UncleRus/quorum-reborn/resources/DiskDrive/disk5buf.png

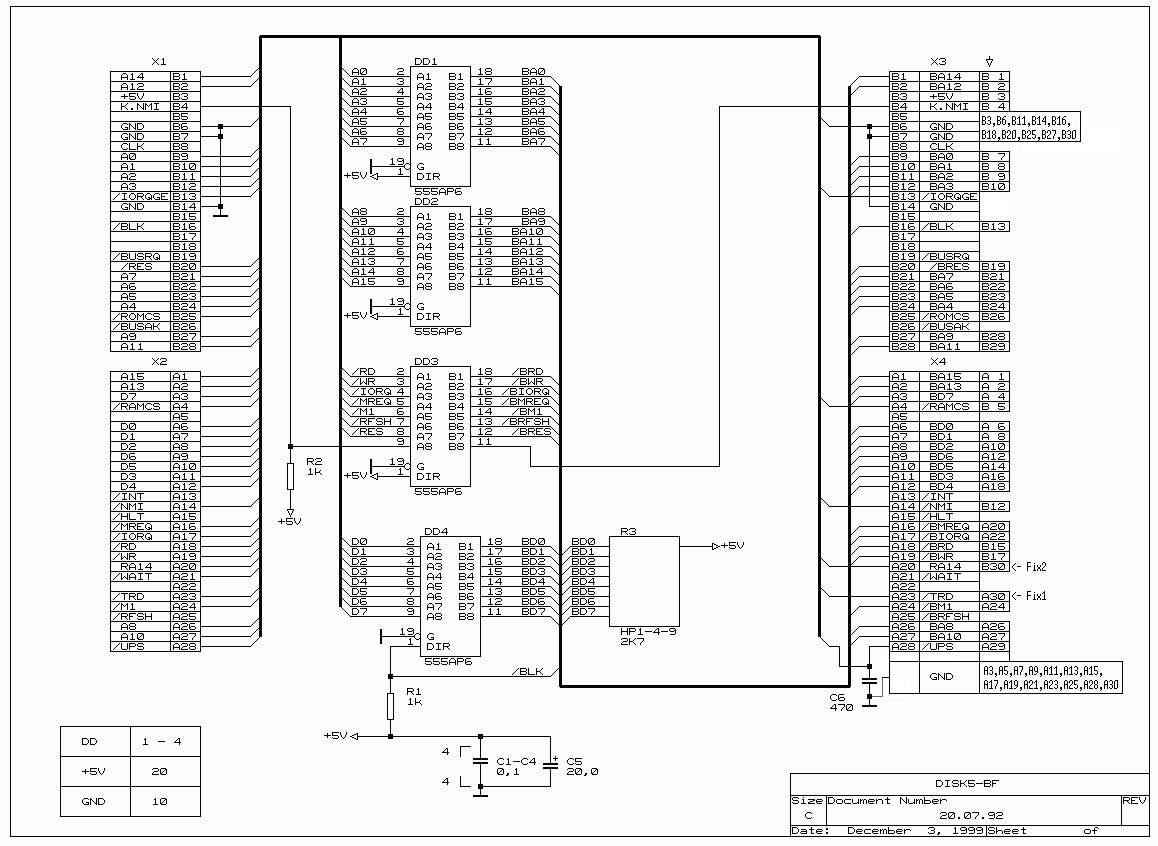
resources/DiskDrive/disk5buf.png
