UncleRus/quorum-reborn/resources/DiskDrive/disk5emu.png

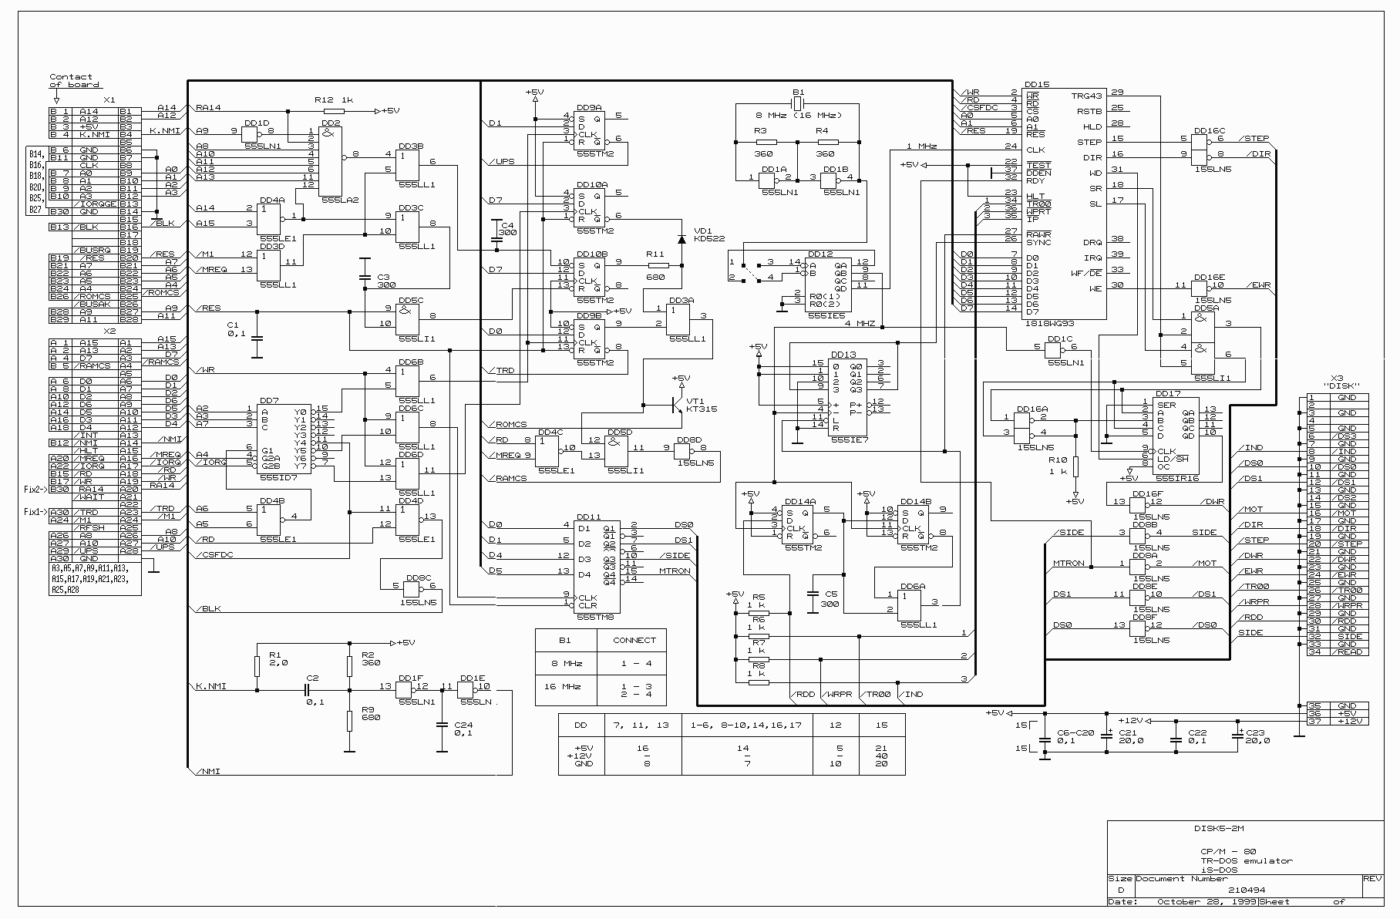
resources/DiskDrive/disk5emu.png
