UncleRus/quorum-reborn/resources/DiskDrive/DISK5RAM.PNG

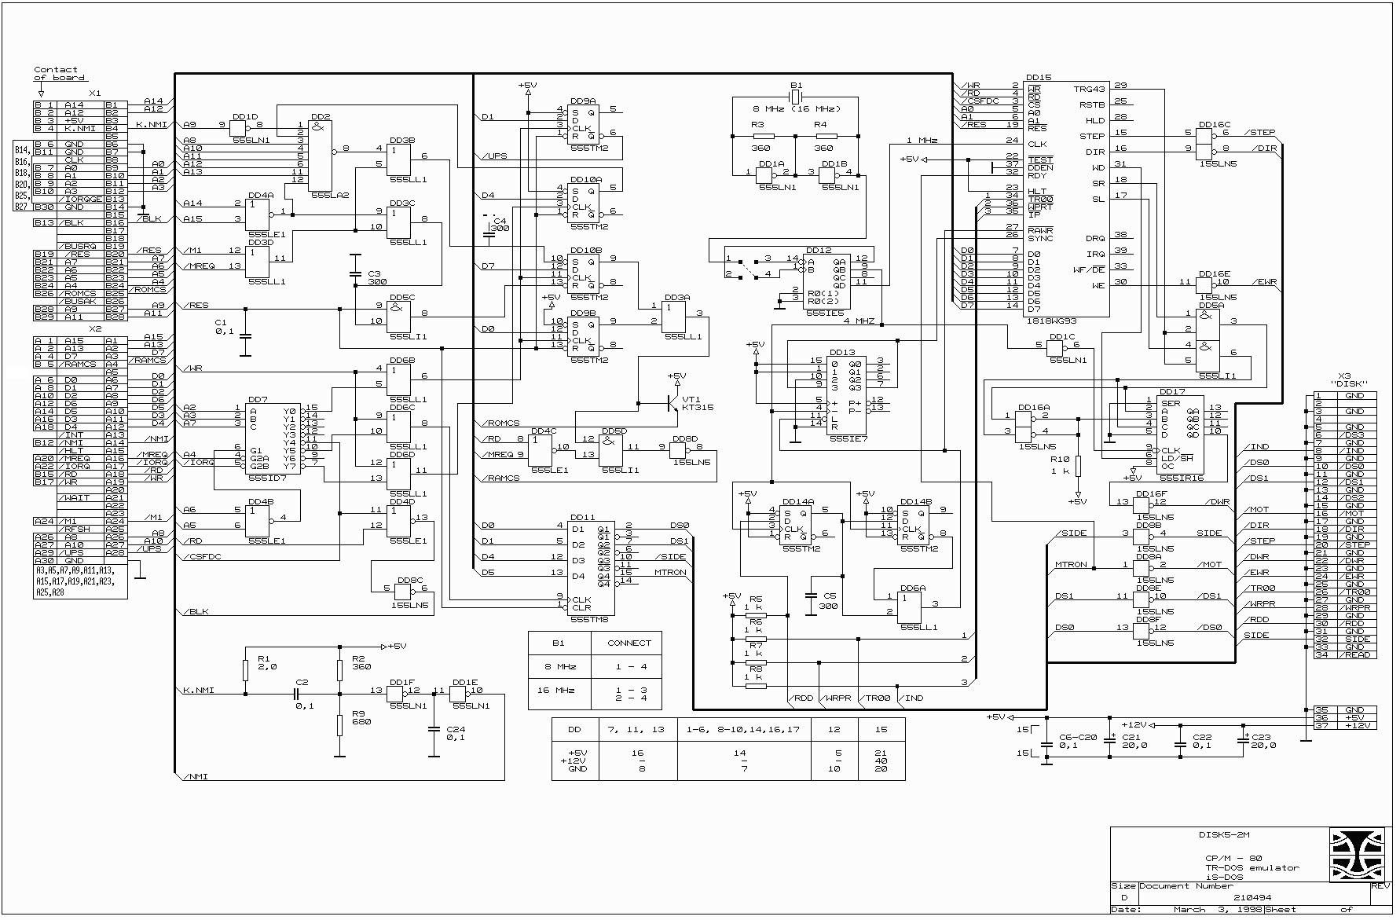
resources/DiskDrive/DISK5RAM.PNG
