UncleRus/quorum-reborn/resources/DiskDrive/disk5raz.png

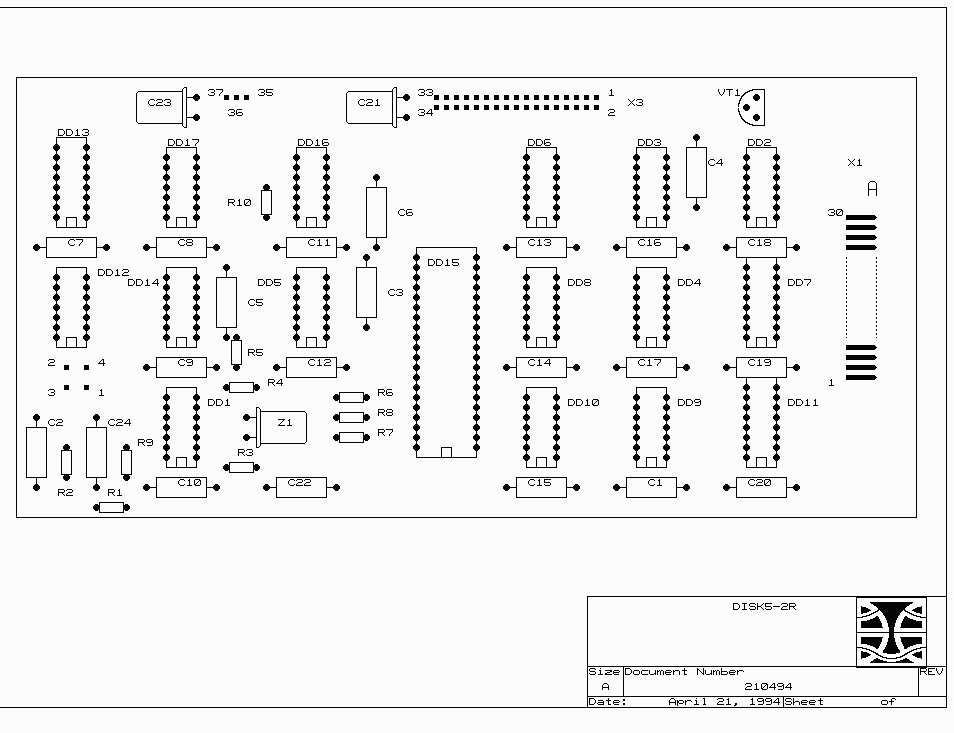
resources/DiskDrive/disk5raz.png
