UncleRus/quorum-reborn/resources/DiskDrive/disk5trd.png

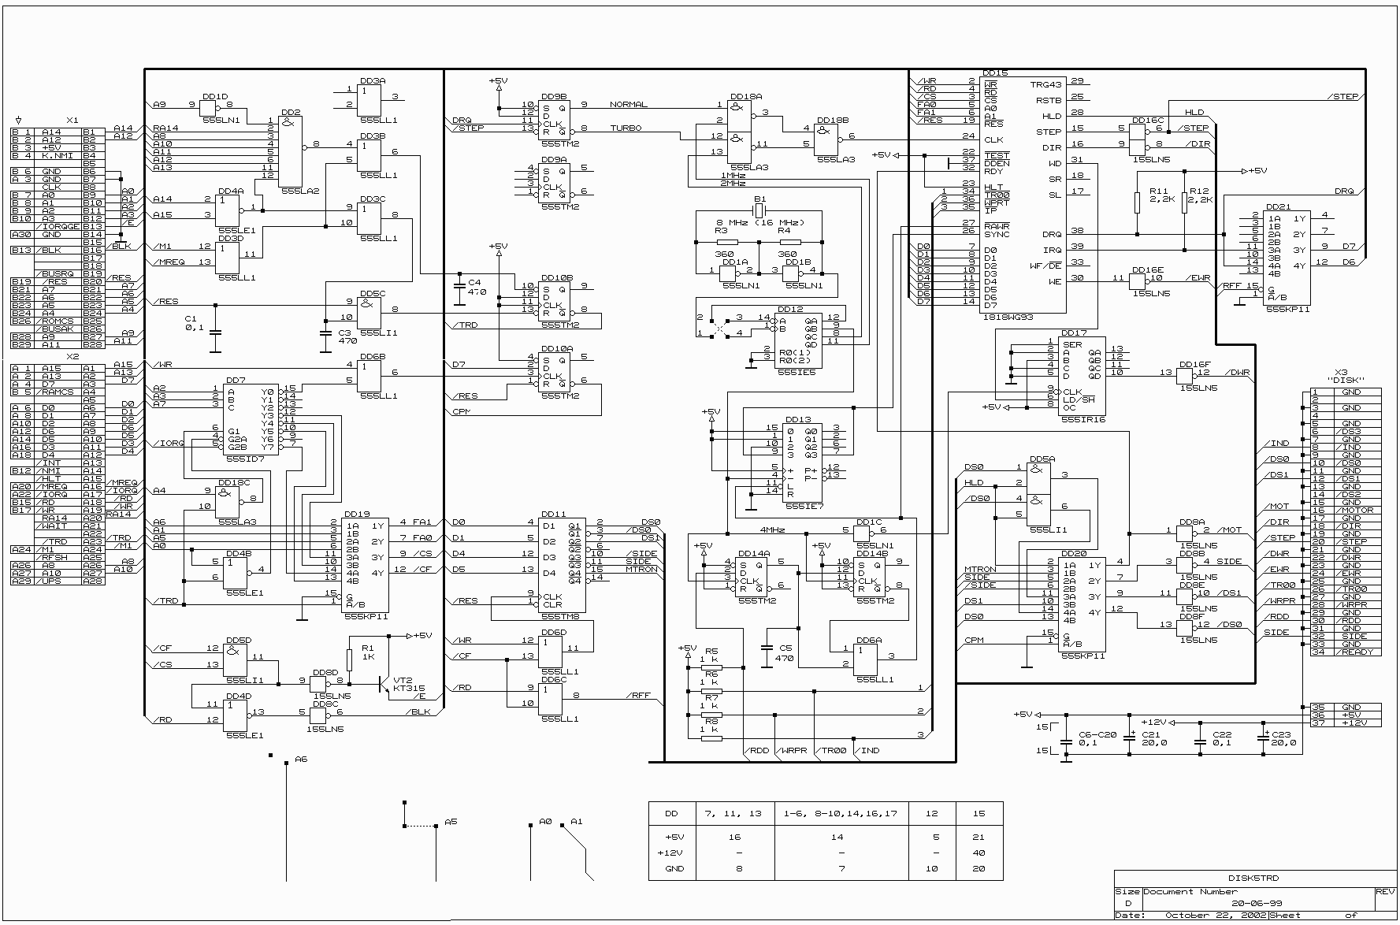
resources/DiskDrive/disk5trd.png
