UncleRus/quorum-reborn/resources/Magic-05/Schematics/Axon/p1.jpg

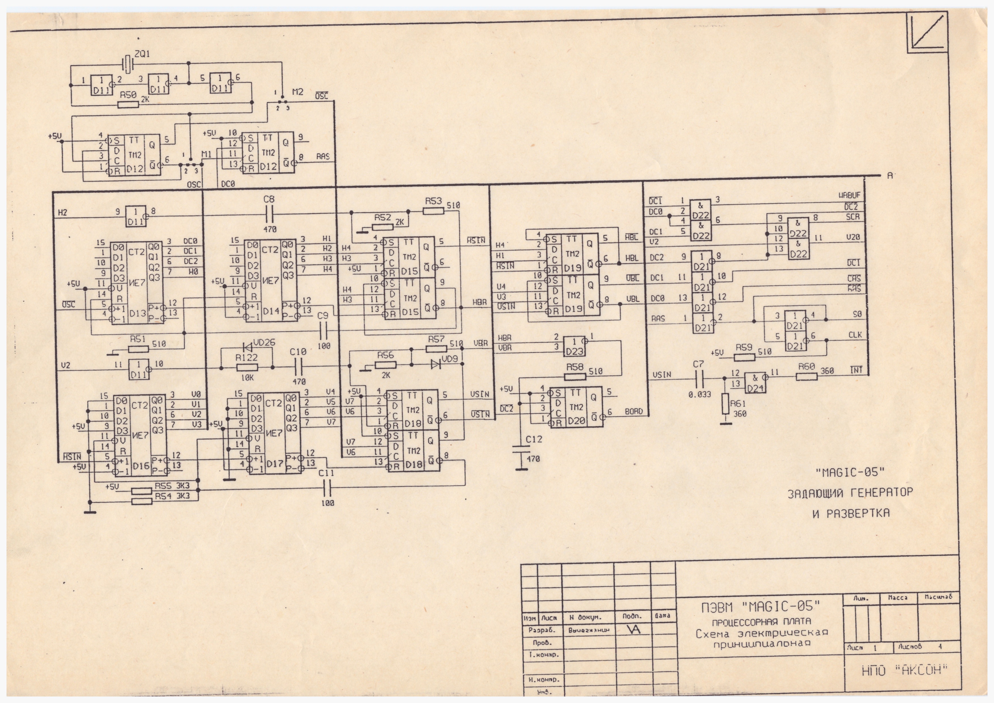
resources/Magic-05/Schematics/Axon/p1.jpg
