UncleRus/quorum-reborn/resources/Magic-05/Schematics/Axon/p2.jpg

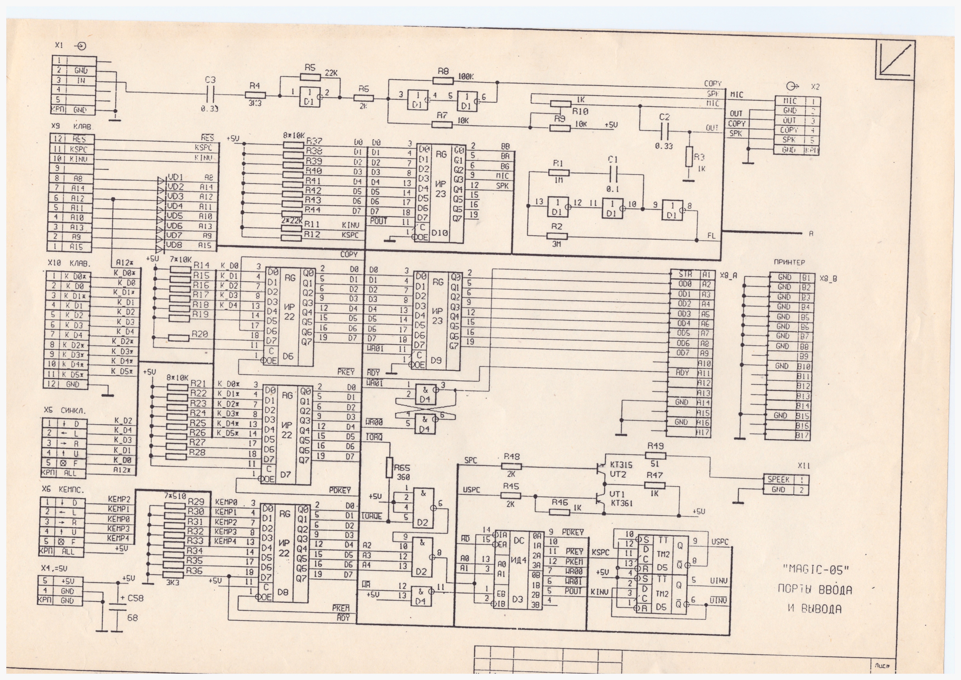
resources/Magic-05/Schematics/Axon/p2.jpg
