UncleRus/quorum-reborn/resources/Magic-05/Schematics/Axon/p5.jpg

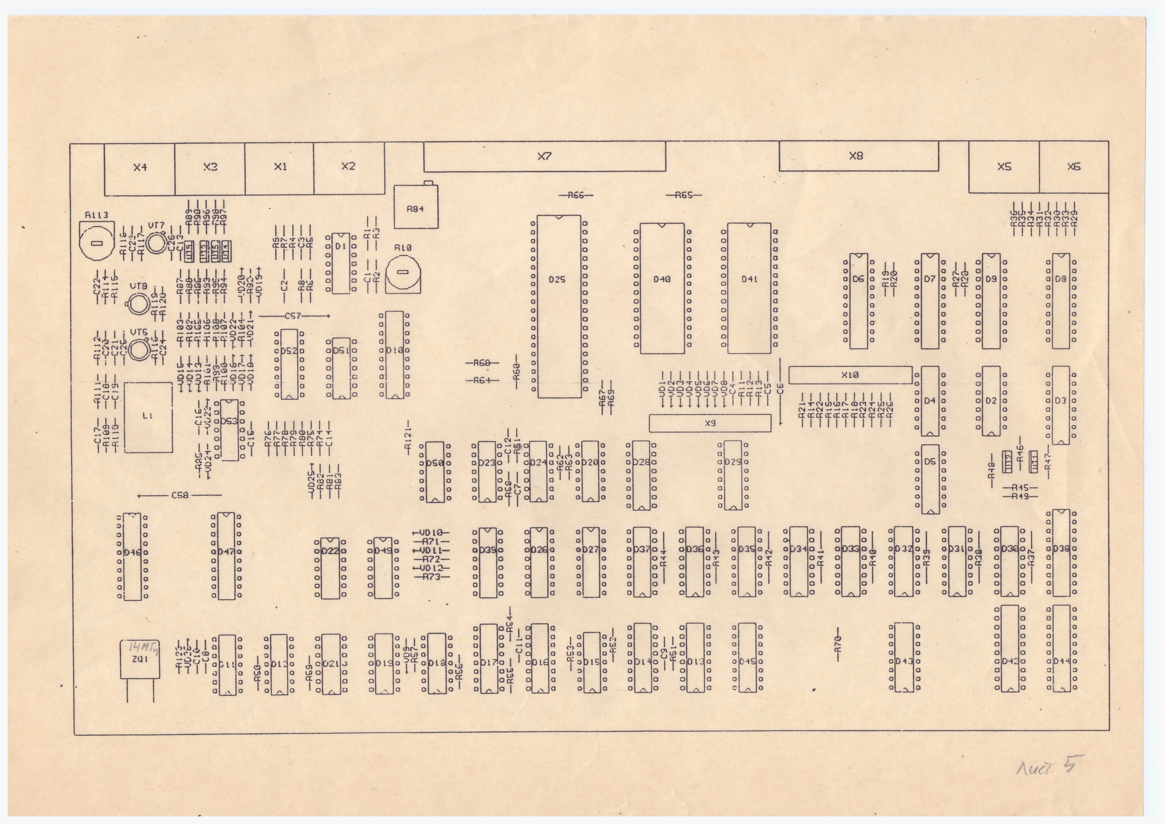
resources/Magic-05/Schematics/Axon/p5.jpg
