UncleRus/quorum-reborn/resources/Magic-06/Schematics/magic6_1.png

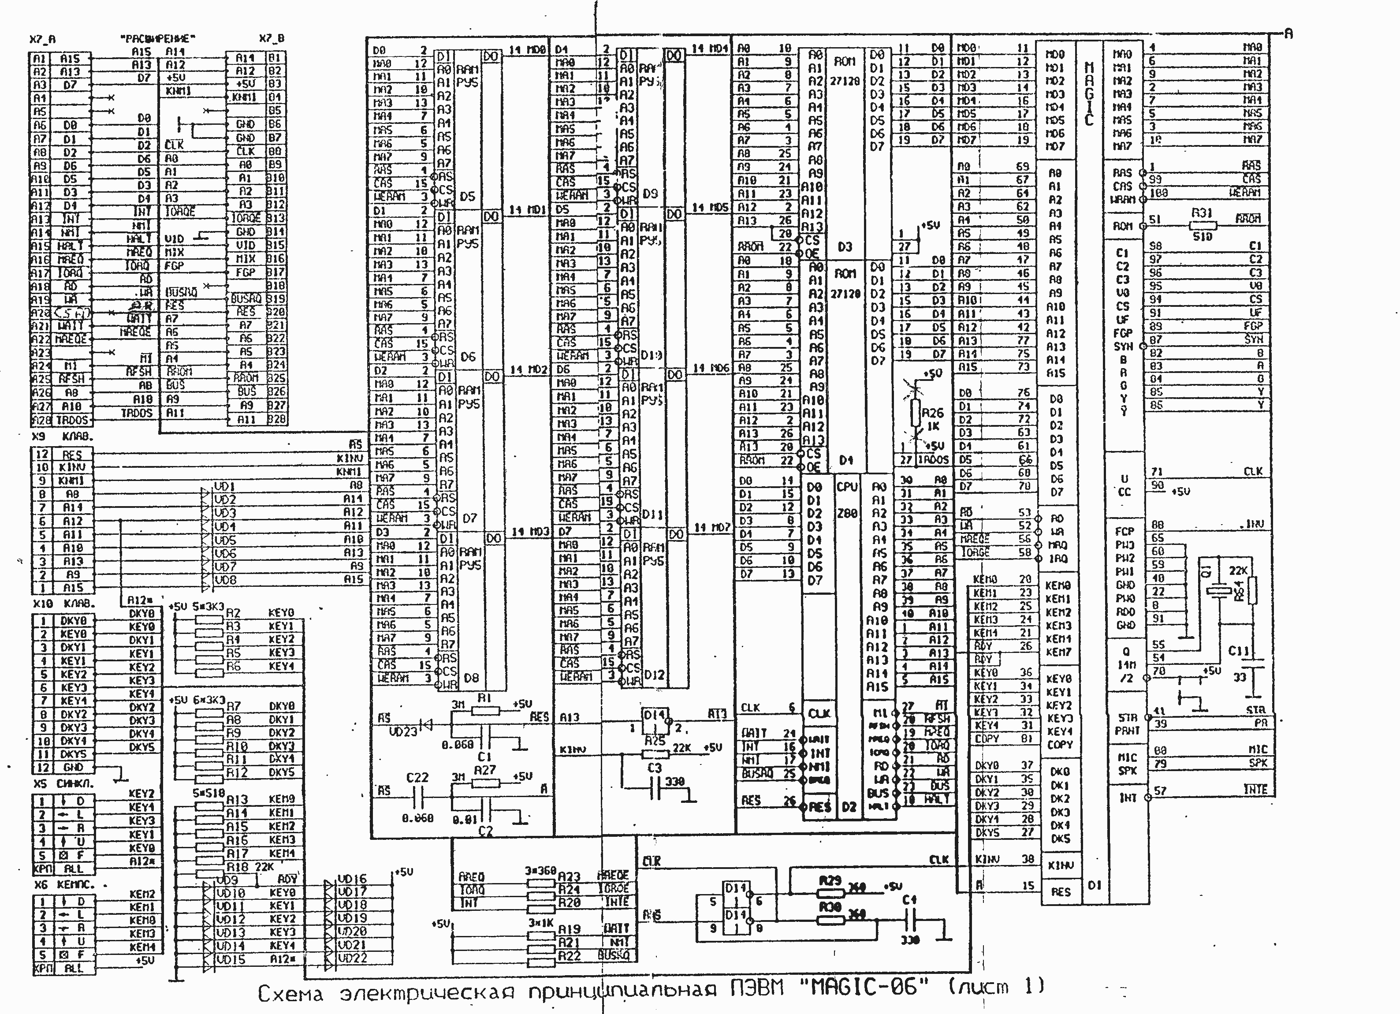
resources/Magic-06/Schematics/magic6_1.png
