UncleRus/quorum-reborn/resources/Magic-06/Schematics/magic6_2.png

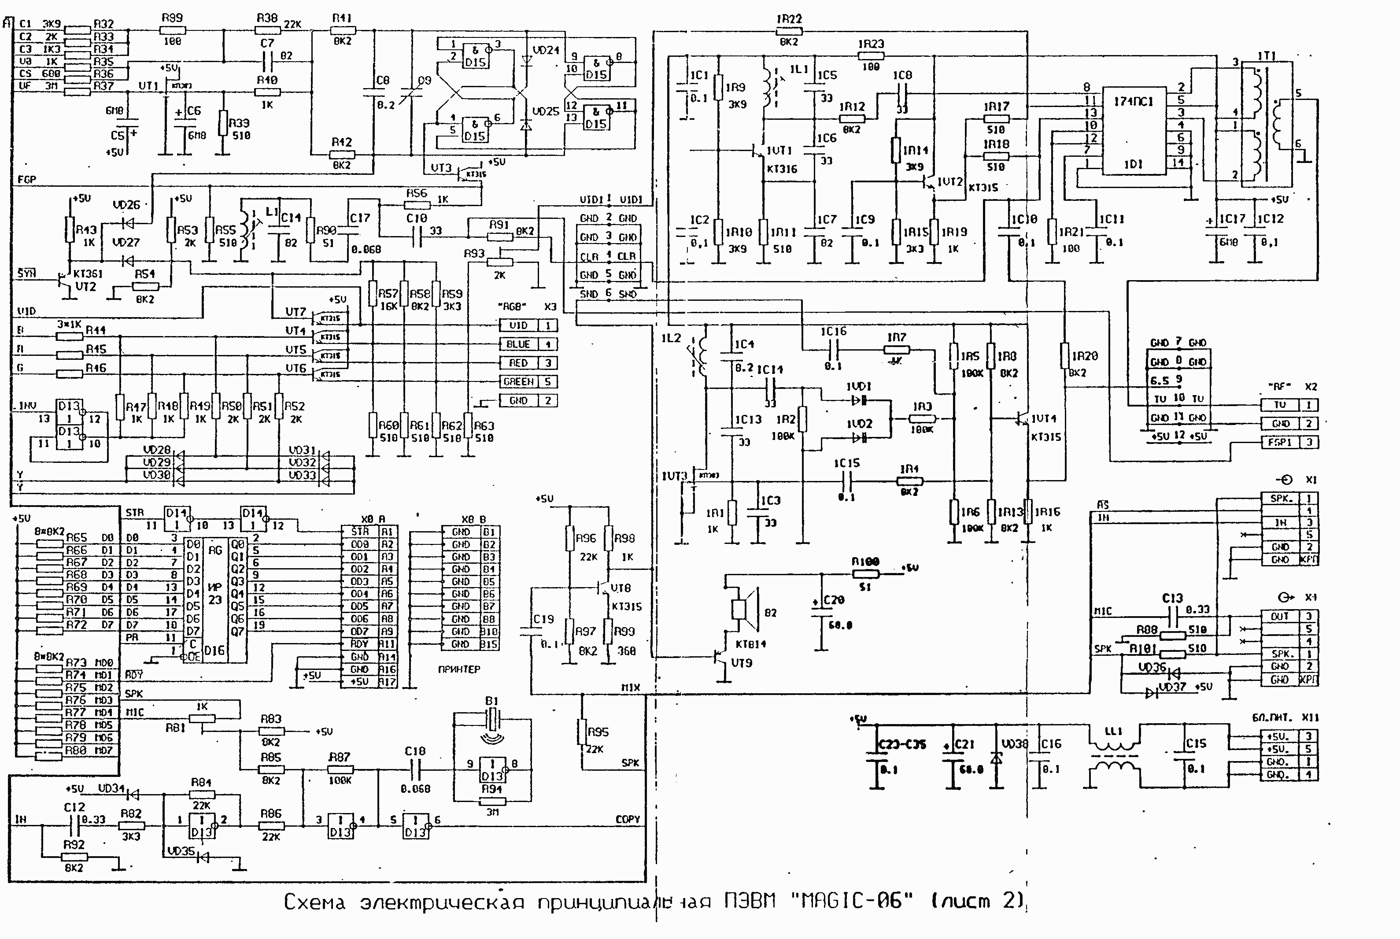
resources/Magic-06/Schematics/magic6_2.png
