UncleRus/quorum-reborn/resources/Quorum-64/Schematics/KBD_sch.jpg

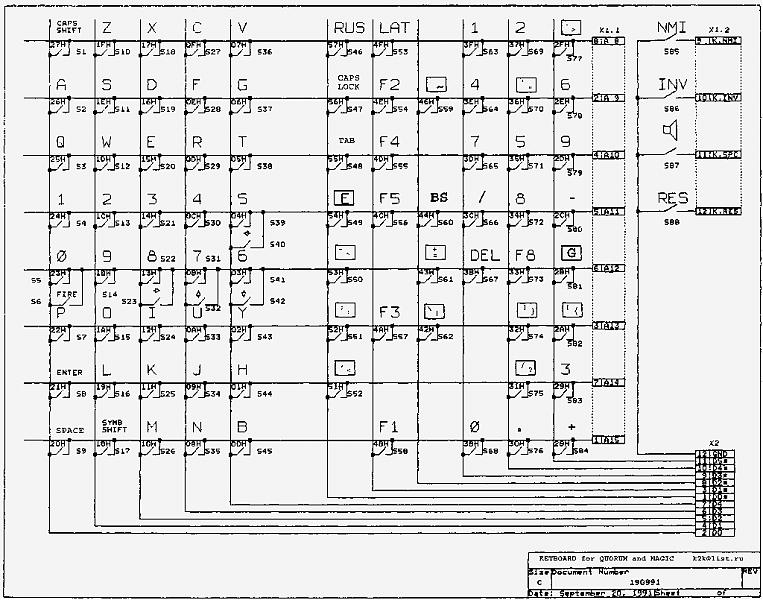
resources/Quorum-64/Schematics/KBD_sch.jpg
