UncleRus/quorum-reborn/resources/Quorum-64/Schematics/QU64_1.PNG

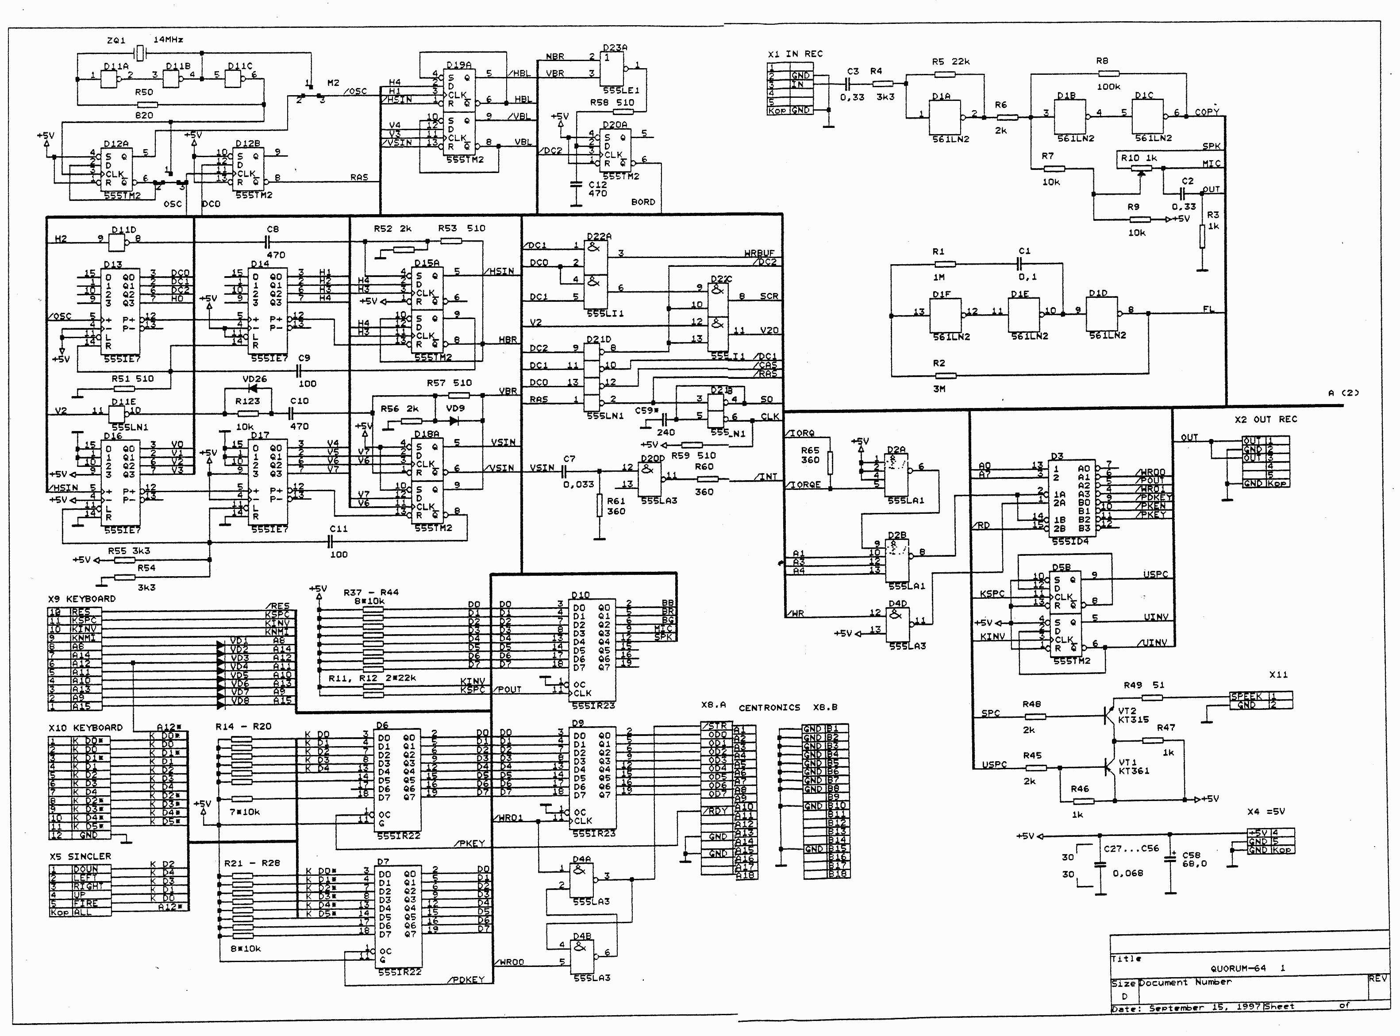
resources/Quorum-64/Schematics/QU64_1.PNG
