UncleRus/quorum-reborn/resources/Quorum-64/Schematics/QU64_2.PNG

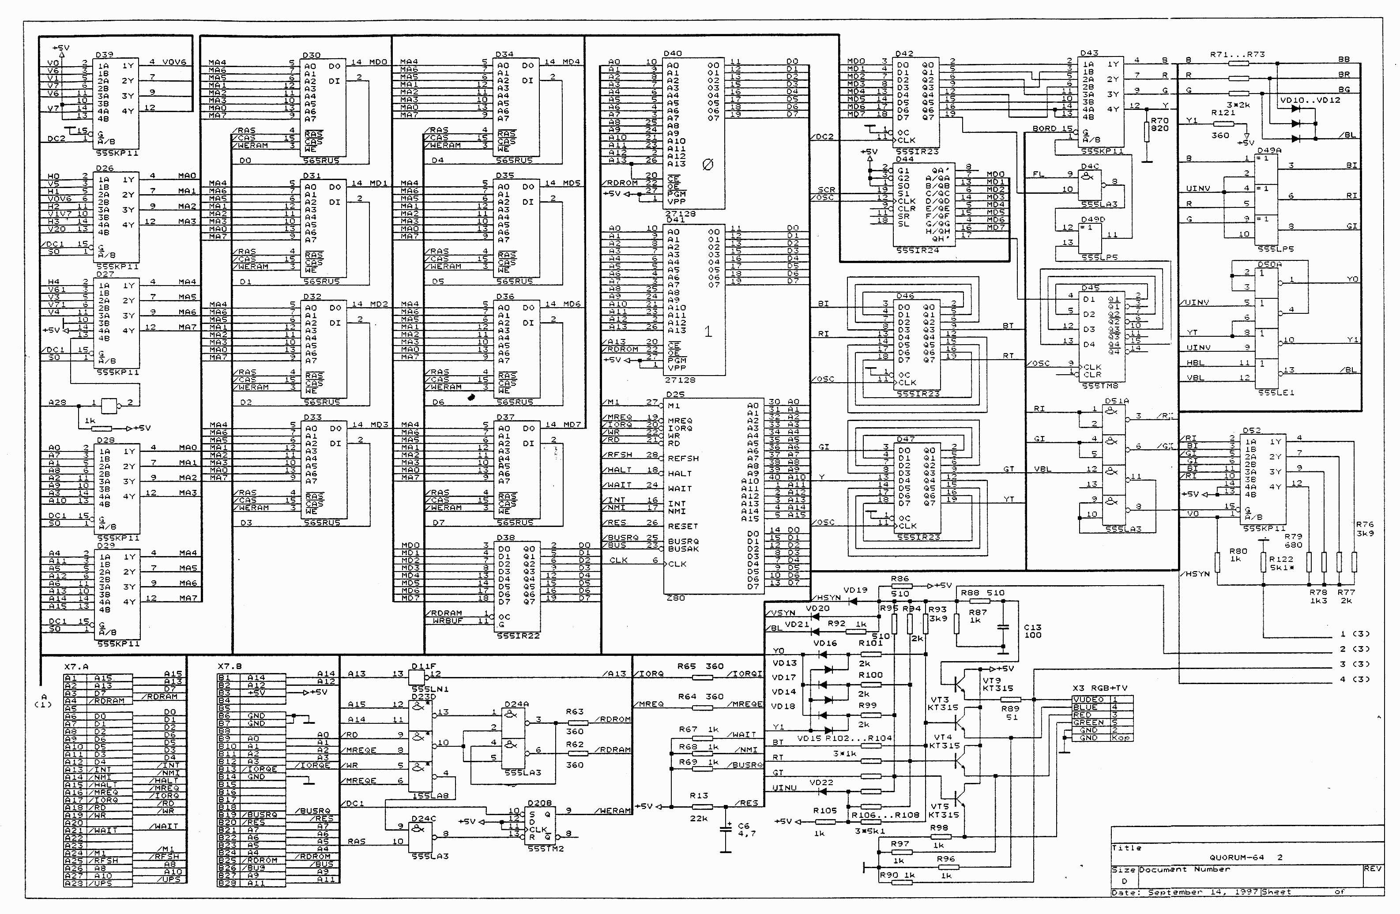
resources/Quorum-64/Schematics/QU64_2.PNG
