UncleRus/quorum-reborn/resources/Quorum-64/Schematics/Quorum_64_0893076.jpg

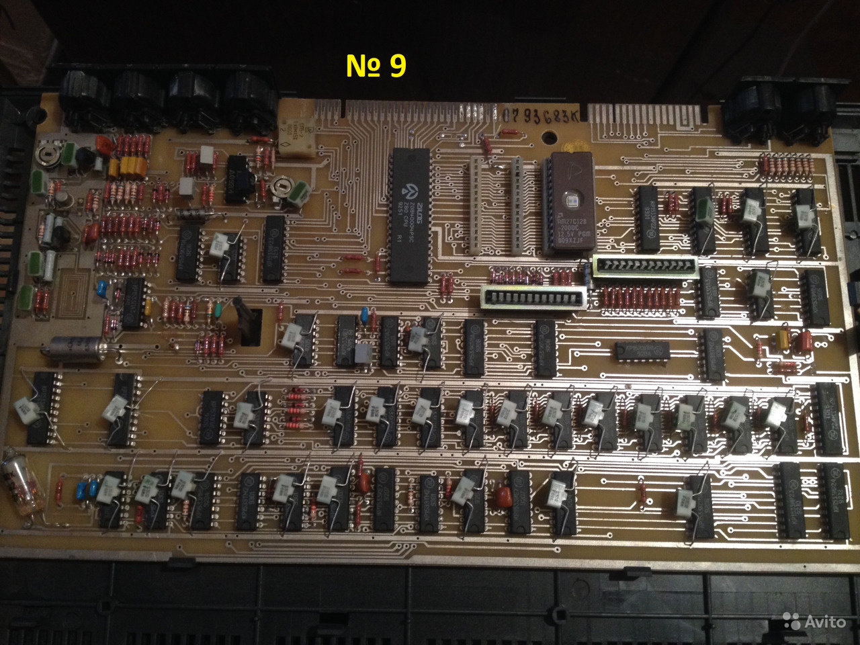
resources/Quorum-64/Schematics/Quorum_64_0893076.jpg
