UncleRus/quorum-reborn/resources/Quorum-128+/Photo/235_001.jpg

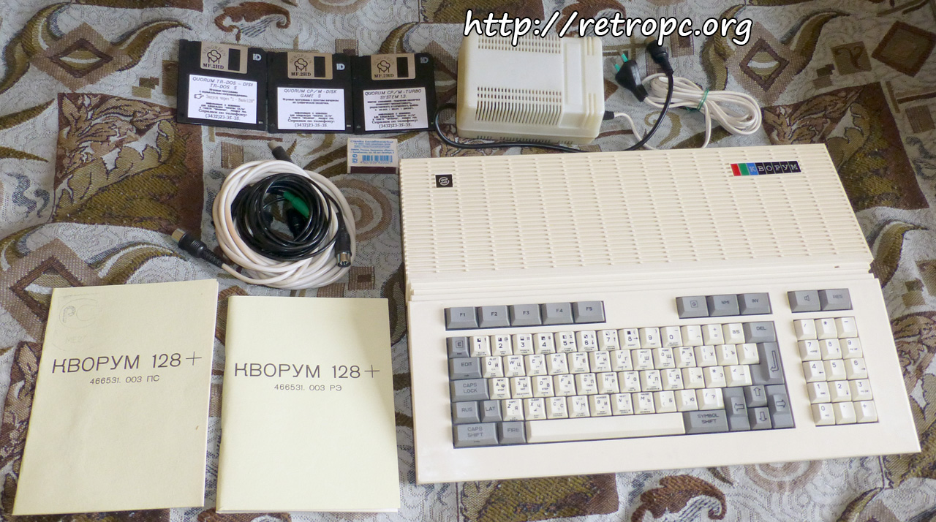
resources/Quorum-128+/Photo/235_001.jpg
