UncleRus/quorum-reborn/resources/Quorum-128+/Photo/235_002.jpg

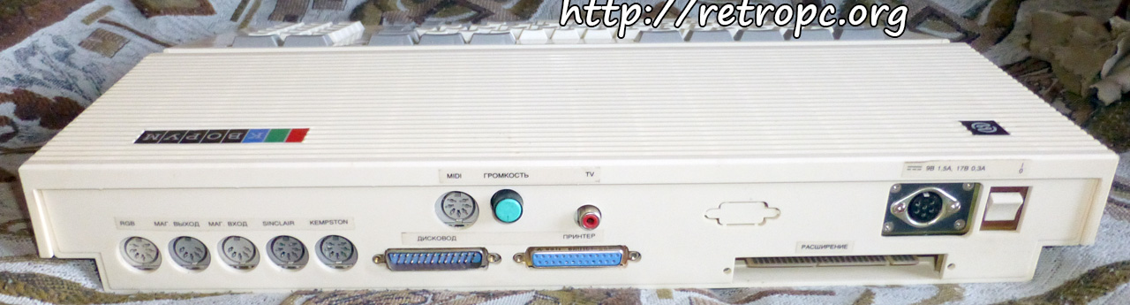
resources/Quorum-128+/Photo/235_002.jpg
