UncleRus/quorum-reborn/resources/Quorum-128+/Photo/235_007.jpg

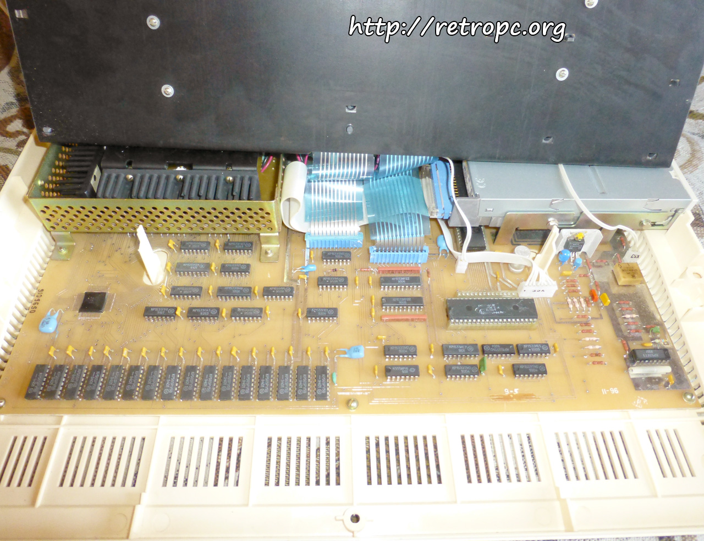
resources/Quorum-128+/Photo/235_007.jpg
