UncleRus/quorum-reborn/resources/Quorum-128+/Schematics/SECAMCODER.png

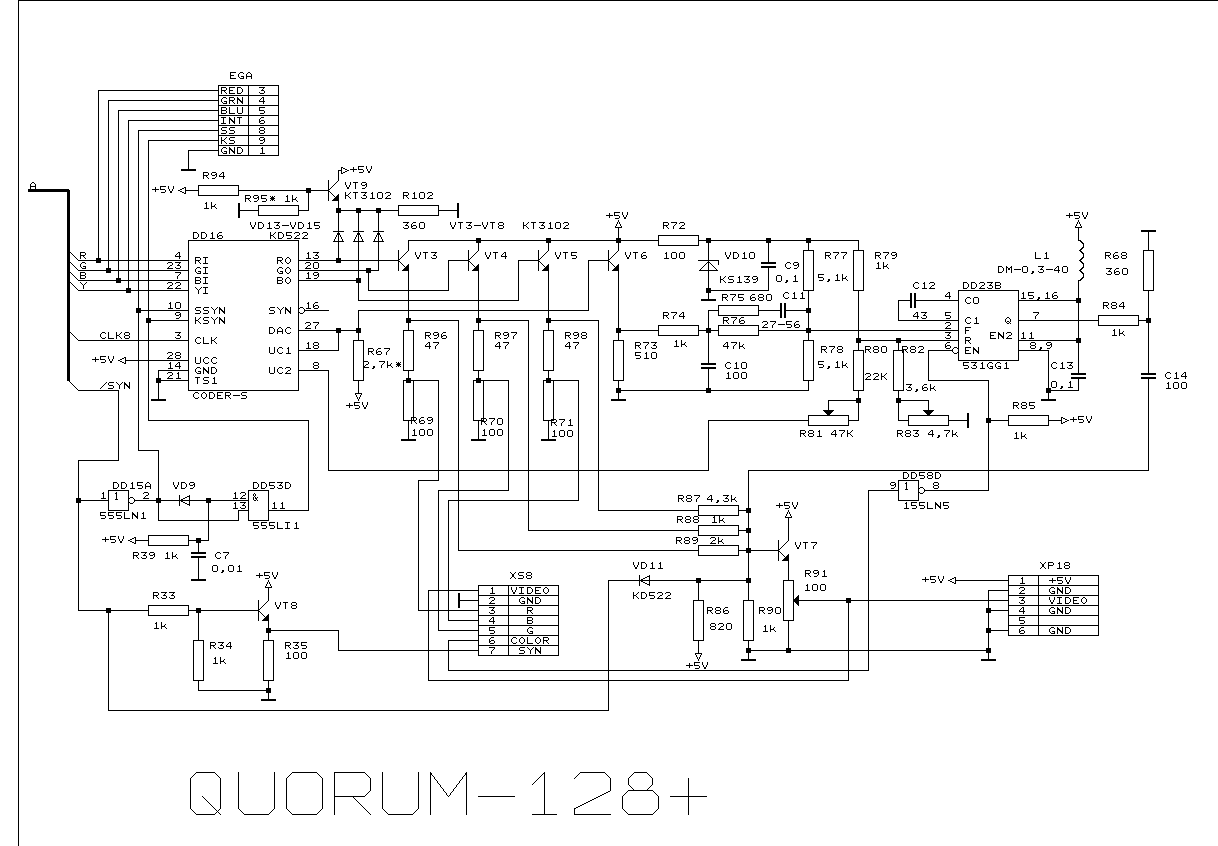
resources/Quorum-128+/Schematics/SECAMCODER.png
