UncleRus/quorum-reborn/resources/Quorum-128+/Schematics/ULA.png

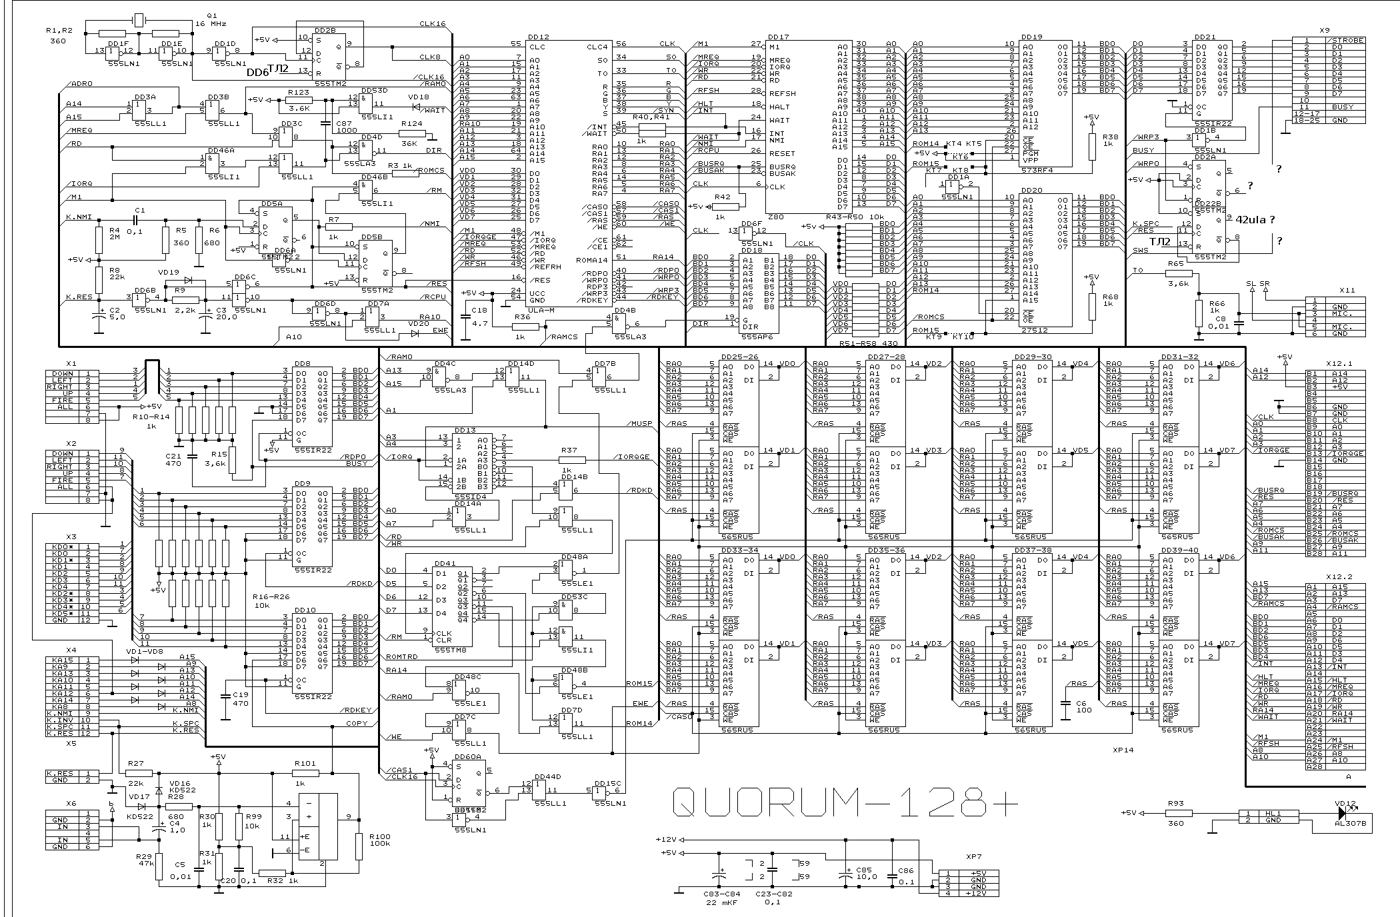
resources/Quorum-128+/Schematics/ULA.png
