UncleRus/quorum-reborn/resources/Quorum-128/Schematics/Q128_CS.PNG

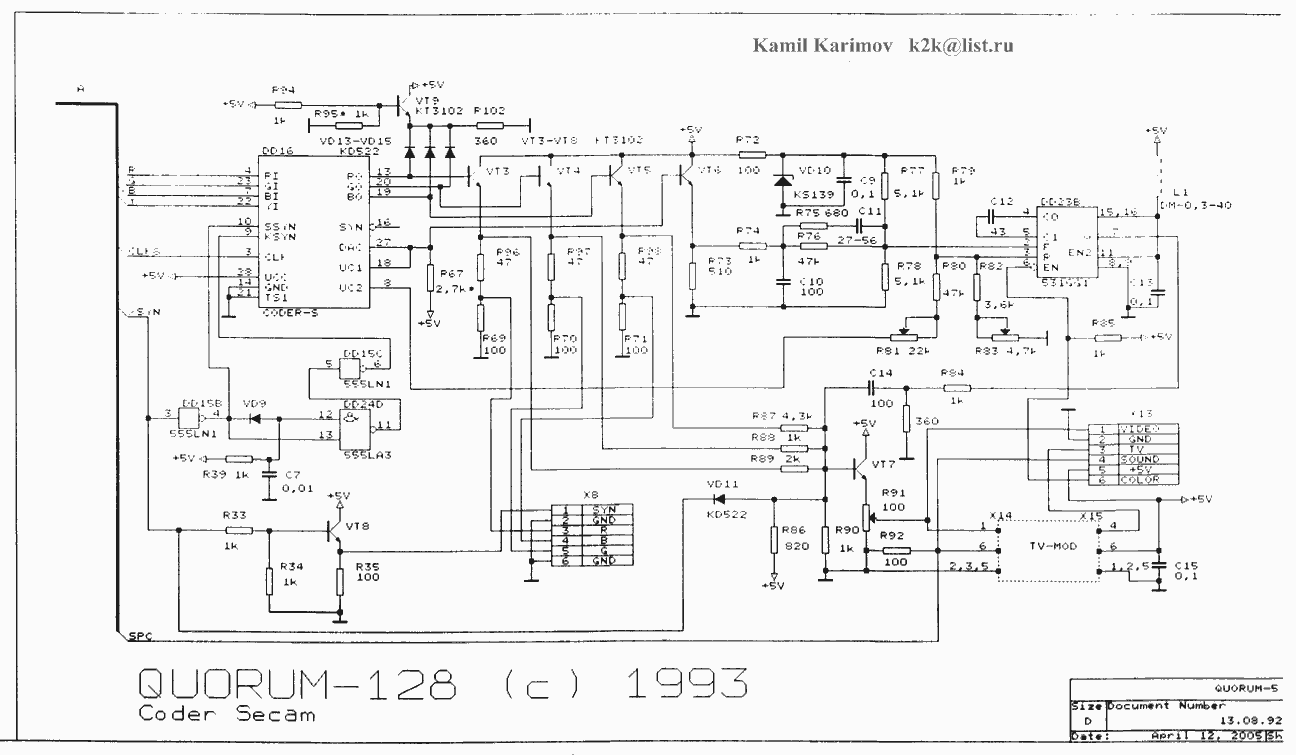
resources/Quorum-128/Schematics/Q128_CS.PNG
