UncleRus/quorum-reborn/resources/Quorum-128/Schematics/Q128P2M.PNG

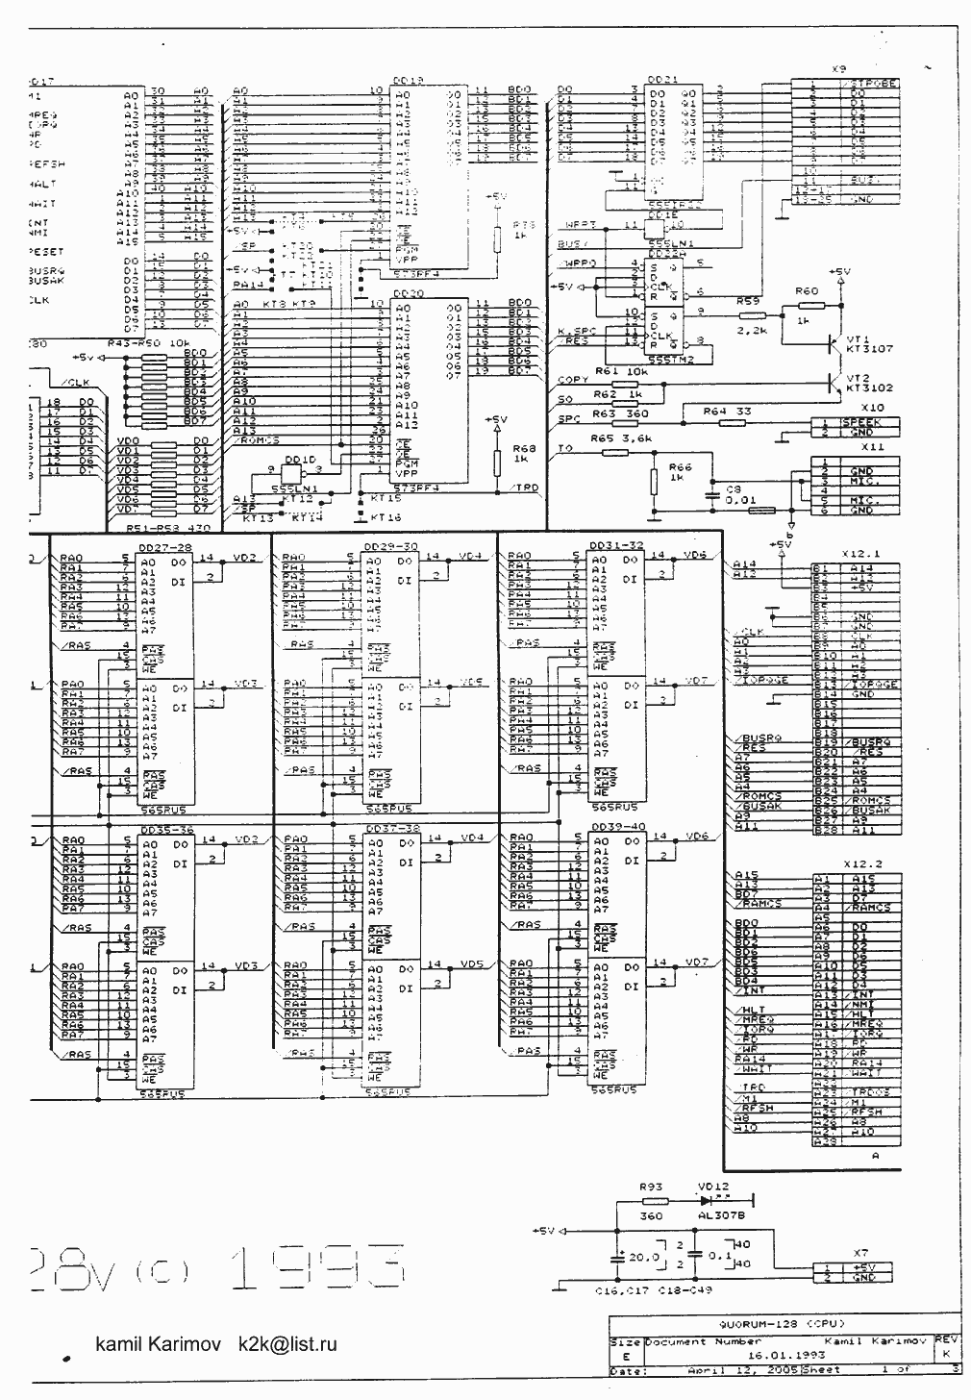
resources/Quorum-128/Schematics/Q128P2M.PNG
