UncleRus/quorum-reborn/resources/Quorum-128/Schematics/qu128mp.png

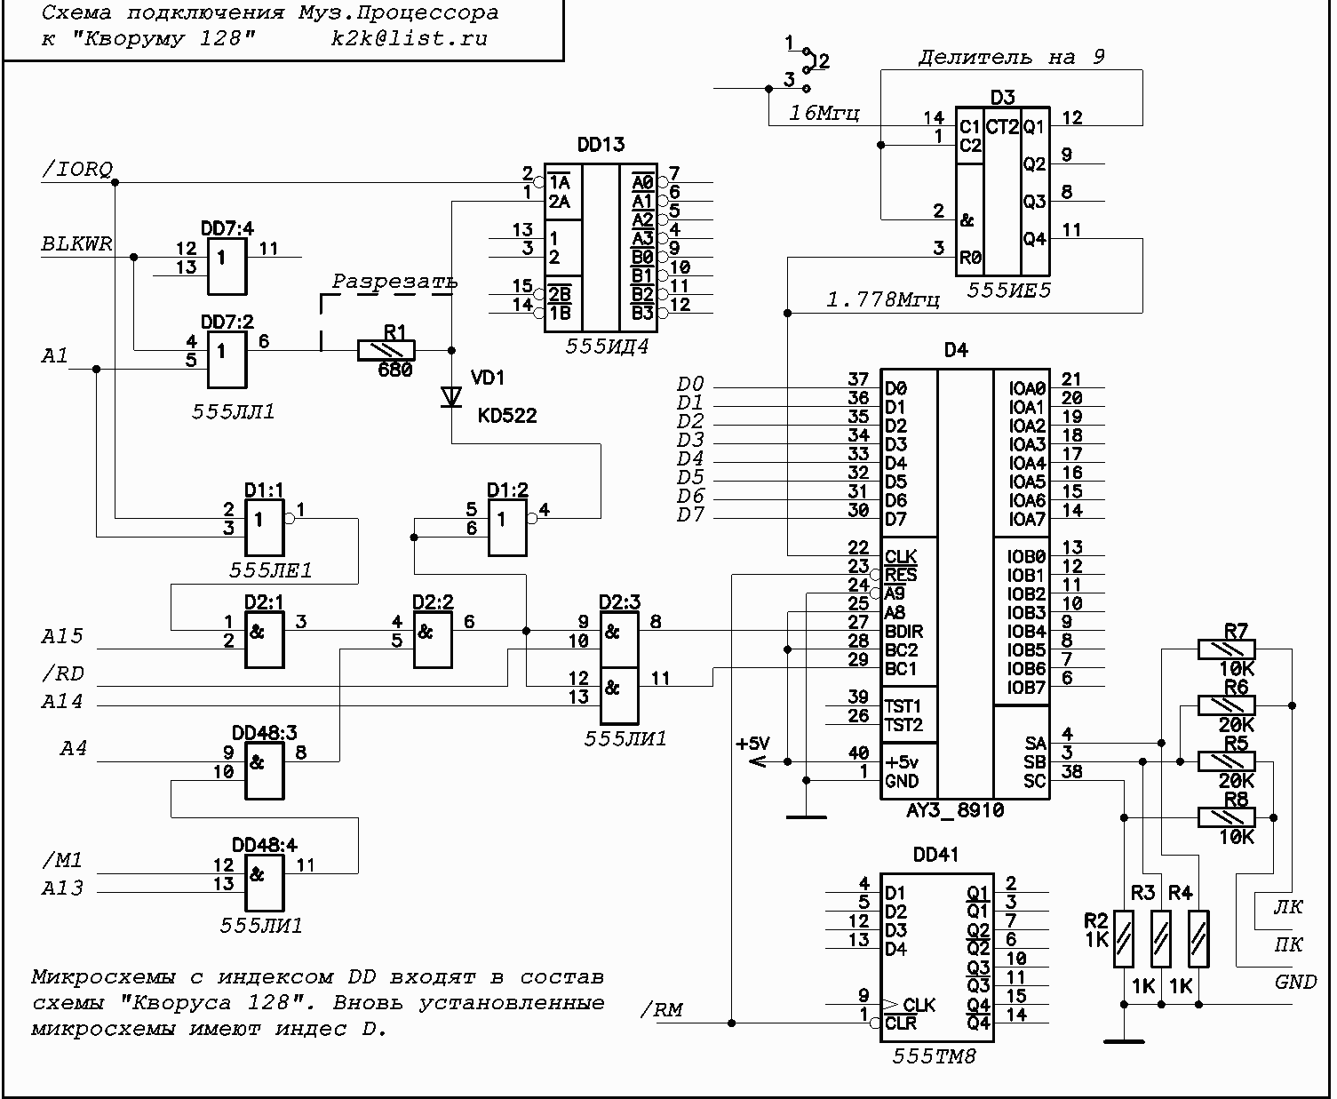
resources/Quorum-128/Schematics/qu128mp.png
