UncleRus/quorum-reborn/resources/Quorum-1024/QU1024.PNG

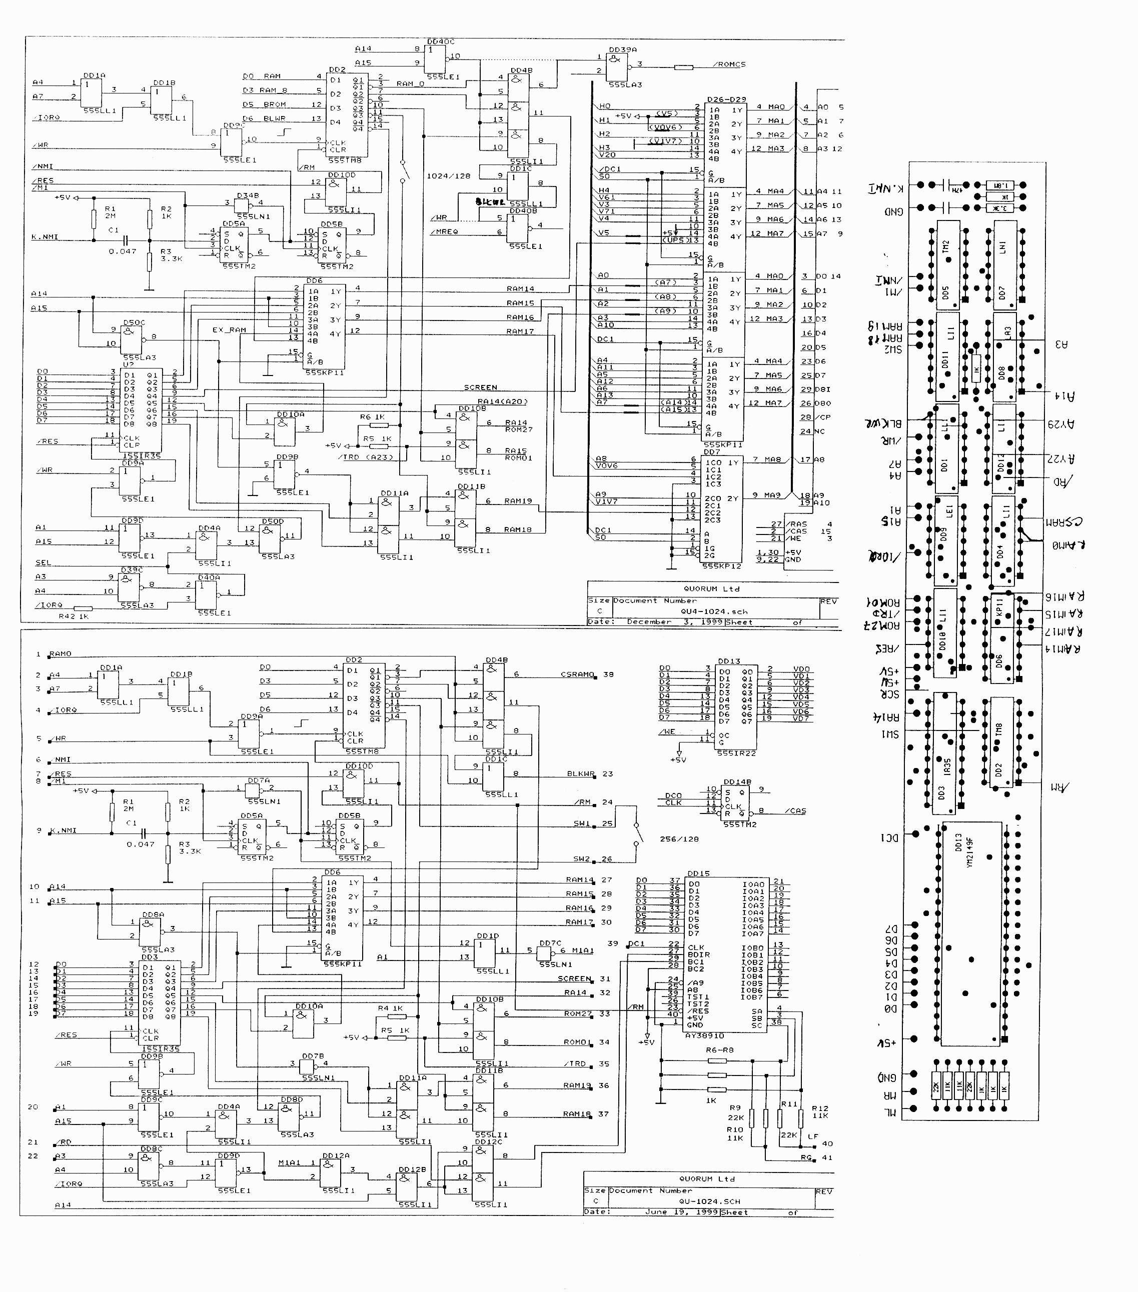
resources/Quorum-1024/QU1024.PNG
