UncleRus/quorum-reborn/resources/Quorum-1024/QU_1024.jpg

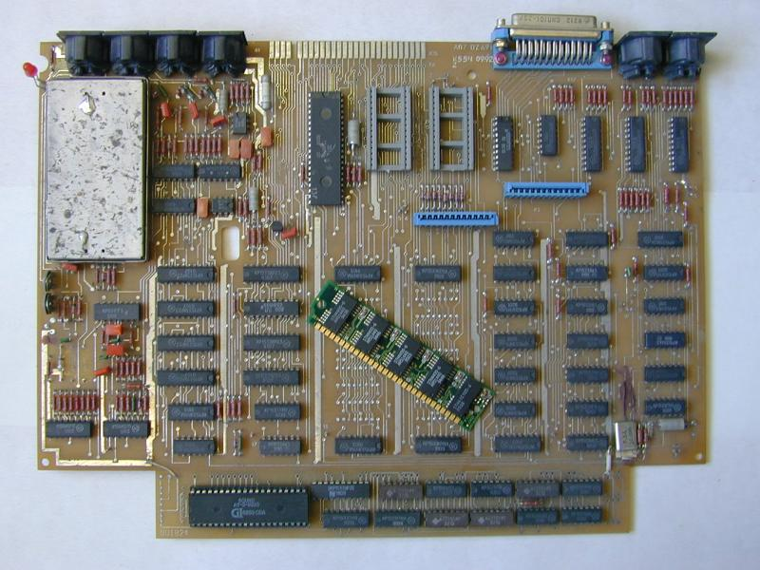
resources/Quorum-1024/QU_1024.jpg
