UncleRus/quorum-reborn/resources/Quorum-BK04/Photo/big_kvorum_3.JPG

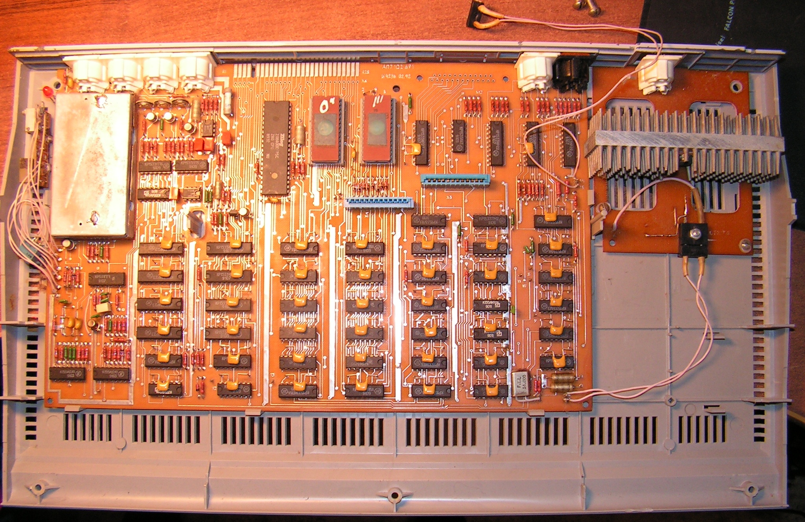
resources/Quorum-BK04/Photo/big_kvorum_3.JPG
