UncleRus/quorum-reborn/resources/Quorum-BK04/Schematics/qu4_mod.PNG

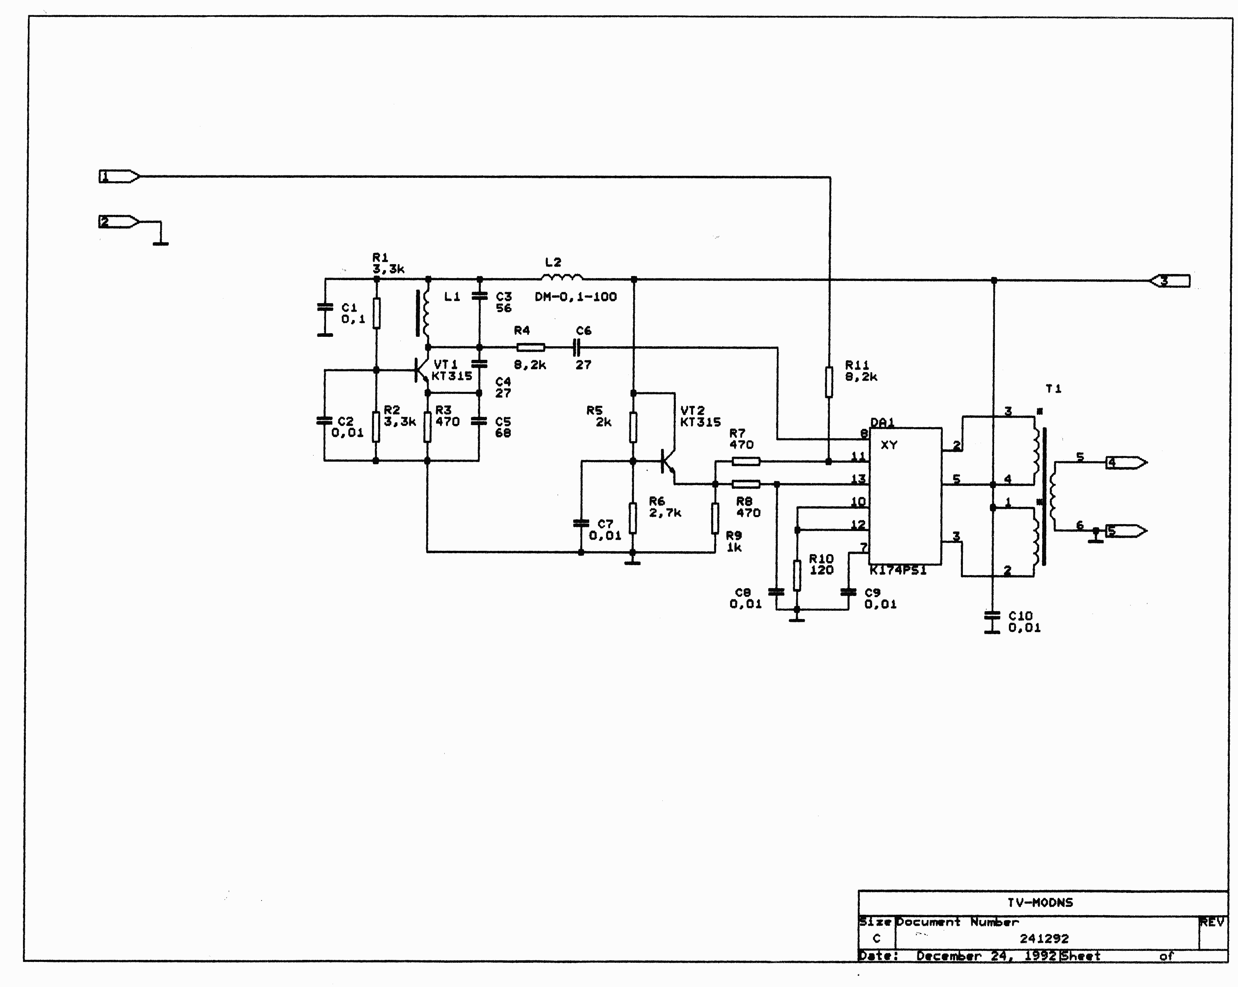
resources/Quorum-BK04/Schematics/qu4_mod.PNG
