UncleRus/quorum-reborn/resources/Quorum-BK04/Schematics/QU4_MTG.PNG

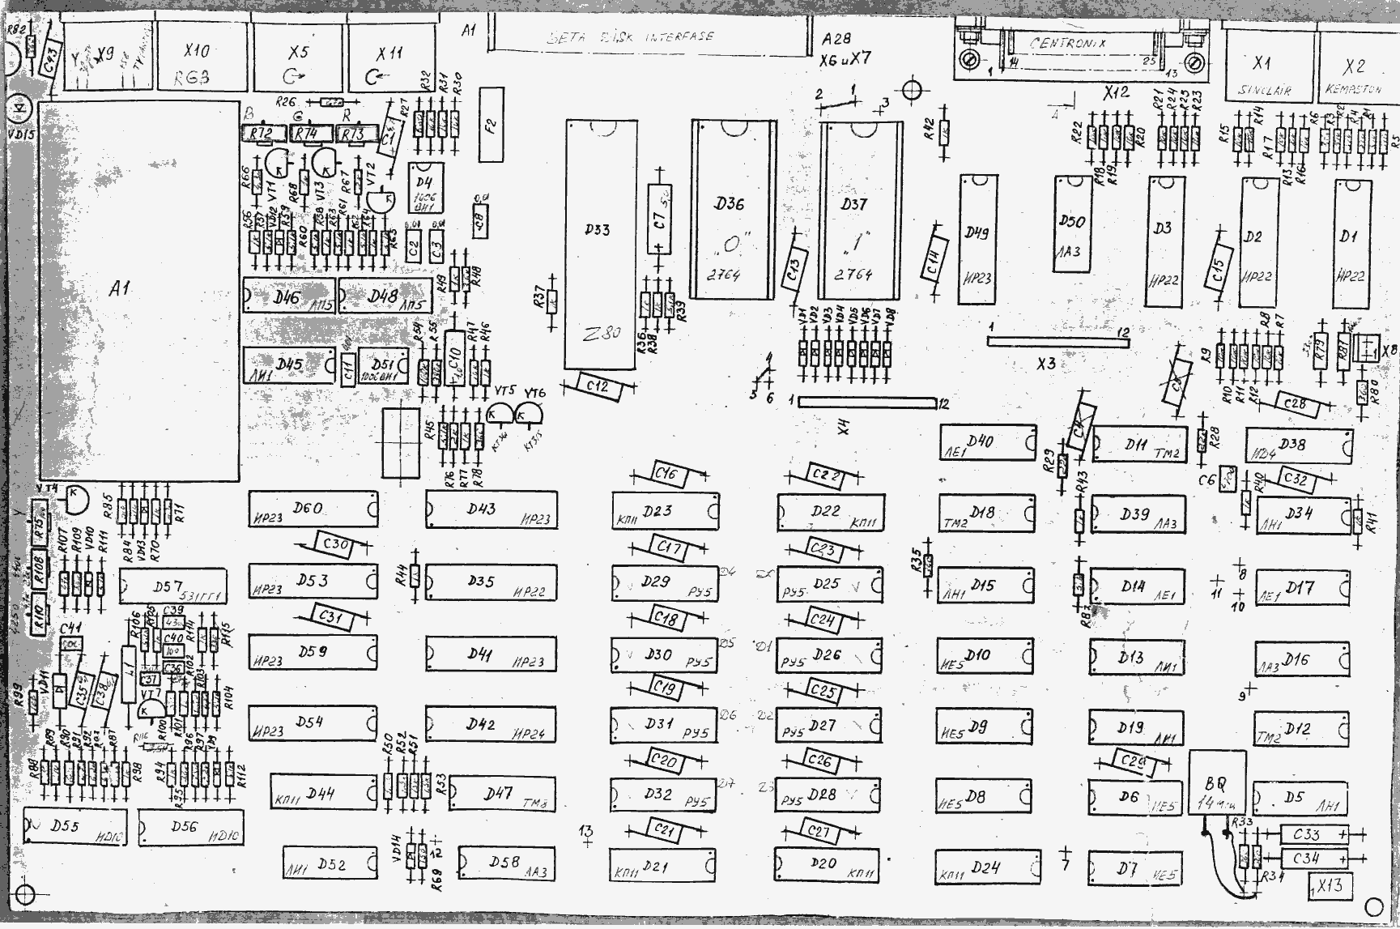
resources/Quorum-BK04/Schematics/QU4_MTG.PNG
