UncleRus/quorum-reborn/resources/Quorum-BK04/Schematics/QU4PG1.PNG

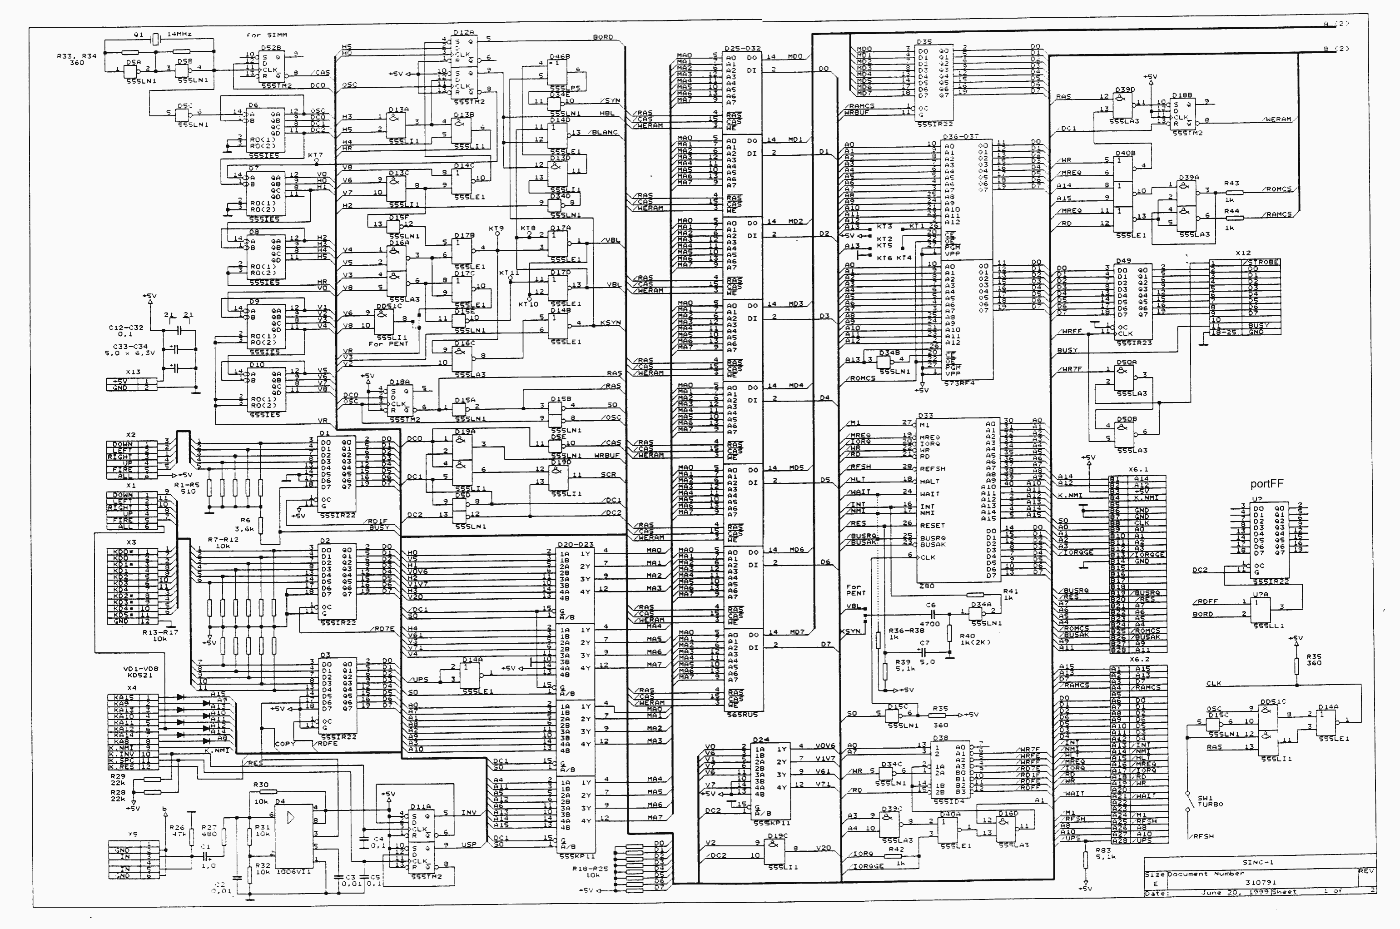
resources/Quorum-BK04/Schematics/QU4PG1.PNG
