UncleRus/quorum-reborn/resources/Quorum-BK04/Schematics/QU4PG2.PNG

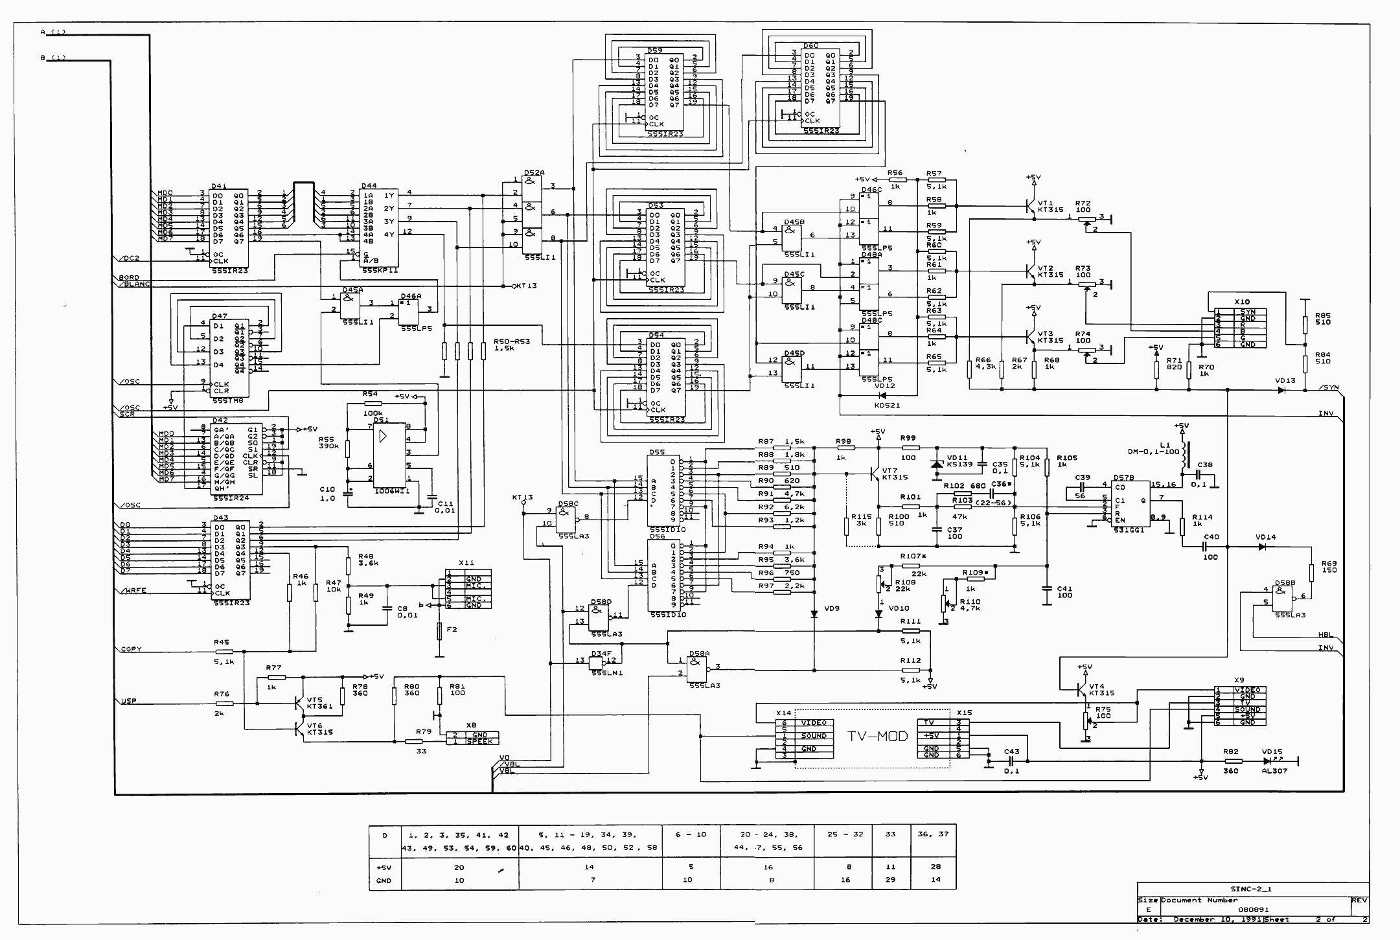
resources/Quorum-BK04/Schematics/QU4PG2.PNG
