UncleRus/quorum-reborn/resources/Quorum-BK05/Photos/quorum_bk05_1.jpg

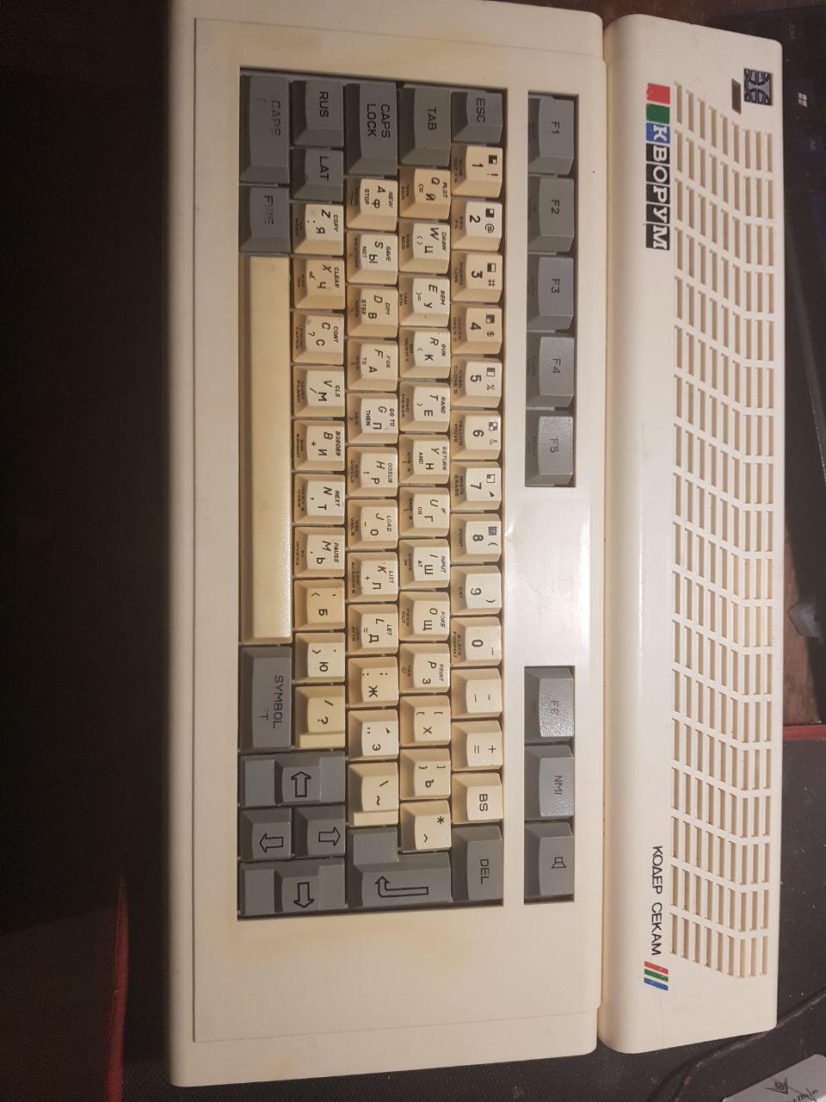
resources/Quorum-BK05/Photos/quorum_bk05_1.jpg
