UncleRus/quorum-reborn/resources/Quorum-BK05/Photos/quorum_bk05_2.jpg

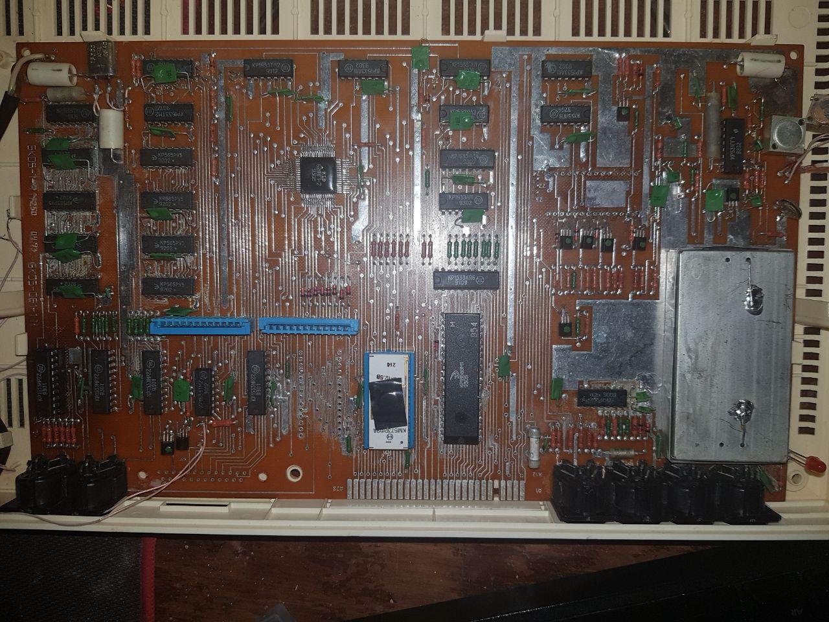
resources/Quorum-BK05/Photos/quorum_bk05_2.jpg
