UncleRus/quorum-reborn/resources/Quorum-BK05/Photos/quorum_bk05_3.jpg

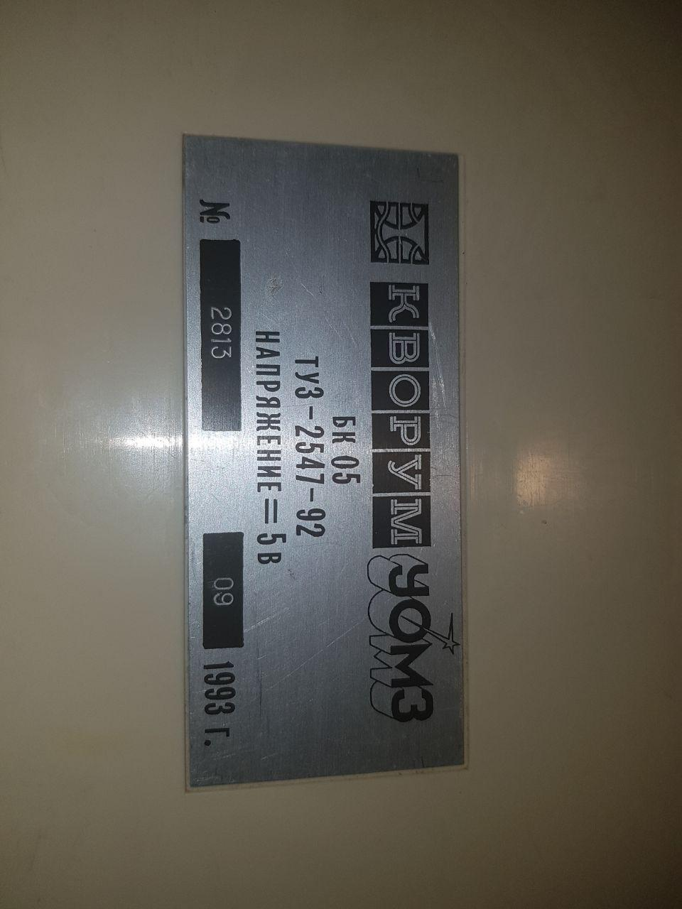
resources/Quorum-BK05/Photos/quorum_bk05_3.jpg
