UncleRus/quorum-reborn/kicad/DiskDrive/buffer.kicad_sch

## KiCad design kicad/DiskDrive/buffer.kicad_sch (2023-06-19)

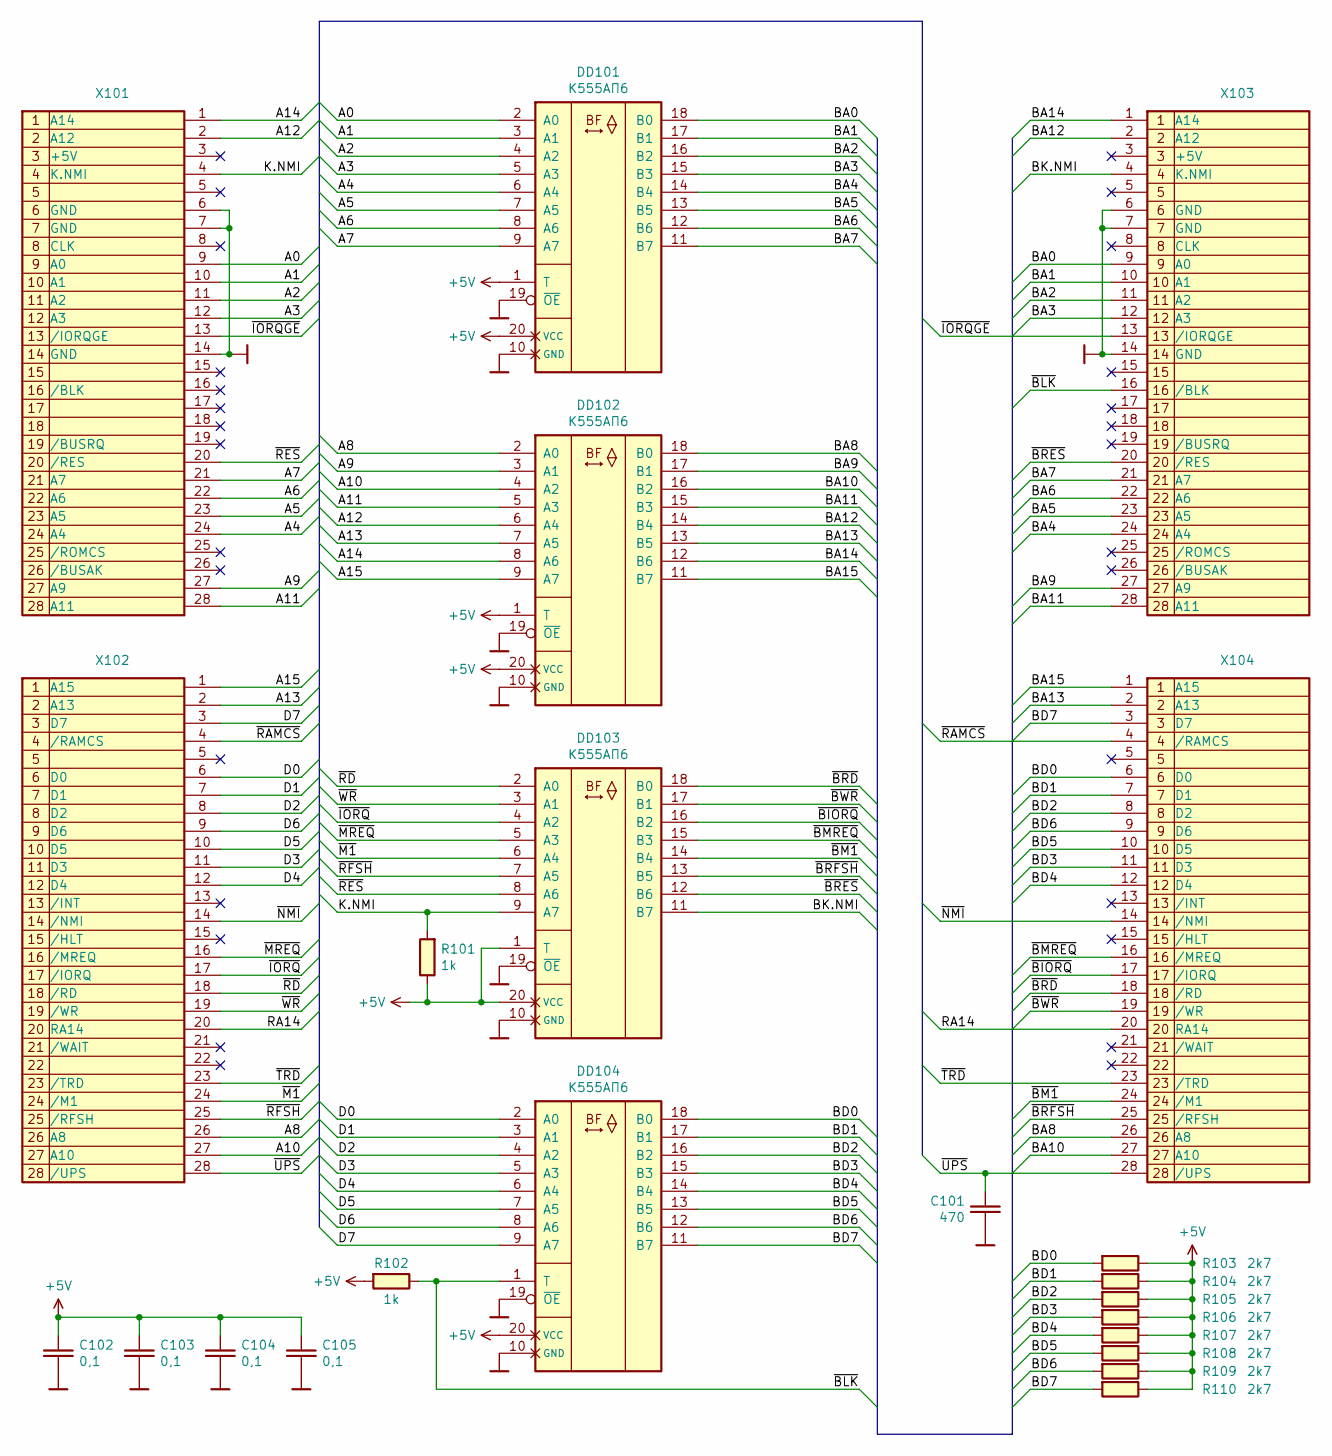
[picture p44: schematic buffer.kicad_sch]

Parts:
C101: 470; C_Rect_L7.0mm_W2.0mm_P5.00mm
C102, C103, C104, C105: 0,1; C_Rect_L7.0mm_W2.0mm_P5.00mm
DD101, DD102, DD103, DD104: К555АП6; DIP-20_W7.62mm_Socket_LongPads
R101, R102: 1k; R_Axial_DIN0207_L6.3mm_D2.5mm_P10.16mm_Horizontal
R103, R104, R105, R106, R107, R108, R109, R110: 2k7; R_Axial_DIN0207_L6.3mm_D2.5mm_P10.16mm_Horizontal
X101, X102: CONN_28
X103, X104: CONN_28; PinHeader_1x28_P2.54mm_Vertical

Connections:
+5V: C102.2, C103.2, C104.2, C105.2, DD101.1 (T), DD101.20 (VCC), DD102.1 (T), DD102.20 (VCC), DD103.1 (T), DD103.20 (VCC), DD104.20 (VCC), R101.2 (R), R102.1 (L), R103.2 (R), R104.2 (R), R105.2 (R), R106.2 (R), R107.2 (R), R108.2 (R), R109.2 (R), R110.2 (R)
A0: DD101.2 (A0), X101.9
A1: DD101.3 (A1), X101.10
A2: DD101.4 (A2), X101.11
A3: DD101.5 (A3), X101.12
A4: DD101.6 (A4), X101.24
A5: DD101.7 (A5), X101.23
A6: DD101.8 (A6), X101.22
A7: DD101.9 (A7), X101.21
A8: DD102.2 (A0), X102.26
A9: DD102.3 (A1), X101.27
A10: DD102.4 (A2), X102.27
A11: DD102.5 (A3), X101.28
A12: DD102.6 (A4), X101.2
A13: DD102.7 (A5), X102.2
A14: DD102.8 (A6), X101.1
A15: DD102.9 (A7), X102.1
BA0: DD101.18 (B0), X103.9
BA1: DD101.17 (B1), X103.10
BA2: DD101.16 (B2), X103.11
BA3: DD101.15 (B3), X103.12
BA4: DD101.14 (B4), X103.24
BA5: DD101.13 (B5), X103.23
BA6: DD101.12 (B6), X103.22
BA7: DD101.11 (B7), X103.21
BA8: DD102.18 (B0), X104.26
BA9: DD102.17 (B1), X103.27
BA10: DD102.16 (B2), X104.27
BA11: DD102.15 (B3), X103.28
BA12: DD102.14 (B4), X103.2
BA13: DD102.13 (B5), X104.2
BA14: DD102.12 (B6), X103.1
BA15: DD102.11 (B7), X104.1
BD0: DD104.18 (B0), R103.1 (L), X104.6
BD1: DD104.17 (B1), R104.1 (L), X104.7
BD2: DD104.16 (B2), R105.1 (L), X104.8
BD3: DD104.15 (B3), R106.1 (L), X104.11
BD4: DD104.14 (B4), R107.1 (L), X104.12
BD5: DD104.13 (B5), R108.1 (L), X104.10
BD6: DD104.12 (B6), R109.1 (L), X104.9
BD7: DD104.11 (B7), R110.1 (L), X104.3
BK.NMI: DD103.11 (B7), X103.4
D0: DD104.2 (A0), X102.6
D1: DD104.3 (A1), X102.7
D2: DD104.4 (A2), X102.8
D3: DD104.5 (A3), X102.11
D4: DD104.6 (A4), X102.12
D5: DD104.7 (A5), X102.10
D6: DD104.8 (A6), X102.9
D7: DD104.9 (A7), X102.3
GND: C101.2, C102.1, C103.1, C104.1, C105.1, DD101.10 (GND), DD101.19 (~OE), DD102.10 (GND), DD102.19 (~OE), DD103.10 (GND), DD103.19 (~OE), DD104.10 (GND), DD104.19 (~OE), X101.6, X101.7, X101.14, X103.6, X103.7, X103.14
K.NMI: DD103.9 (A7), R101.1 (L), X101.4
RA14: X102.20, X104.20
~BIORQ: DD103.16 (B2), X104.17
~BLK: DD104.1 (T), R102.2 (R), X103.16
~BM1: DD103.14 (B4), X104.24
~BMREQ: DD103.15 (B3), X104.16
~BRD: DD103.18 (B0), X104.18
~BRES: DD103.12 (B6), X103.20
~BRFSH: DD103.13 (B5), X104.25
~BWR: DD103.17 (B1), X104.19
~IORQGE: X101.13, X103.13
~IORQ: DD103.4 (A2), X102.17
~M1: DD103.6 (A4), X102.24
~MREQ: DD103.5 (A3), X102.16
~NMI: X102.14, X104.14
~RAMCS: X102.4, X104.4
~RD: DD103.2 (A0), X102.18
~RES: DD103.8 (A6), X101.20
~RFSH: DD103.7 (A5), X102.25
~TRD: X102.23, X104.23
~UPS: C101.1, X102.28, X104.28
~WR: DD103.3 (A1), X102.19
