UncleRus/quorum-reborn/kicad/DiskDrive/quorum_disk_drive_emu.kicad_sch

## KiCad design kicad/DiskDrive/quorum_disk_drive_emu.kicad_sch (2023-06-19)

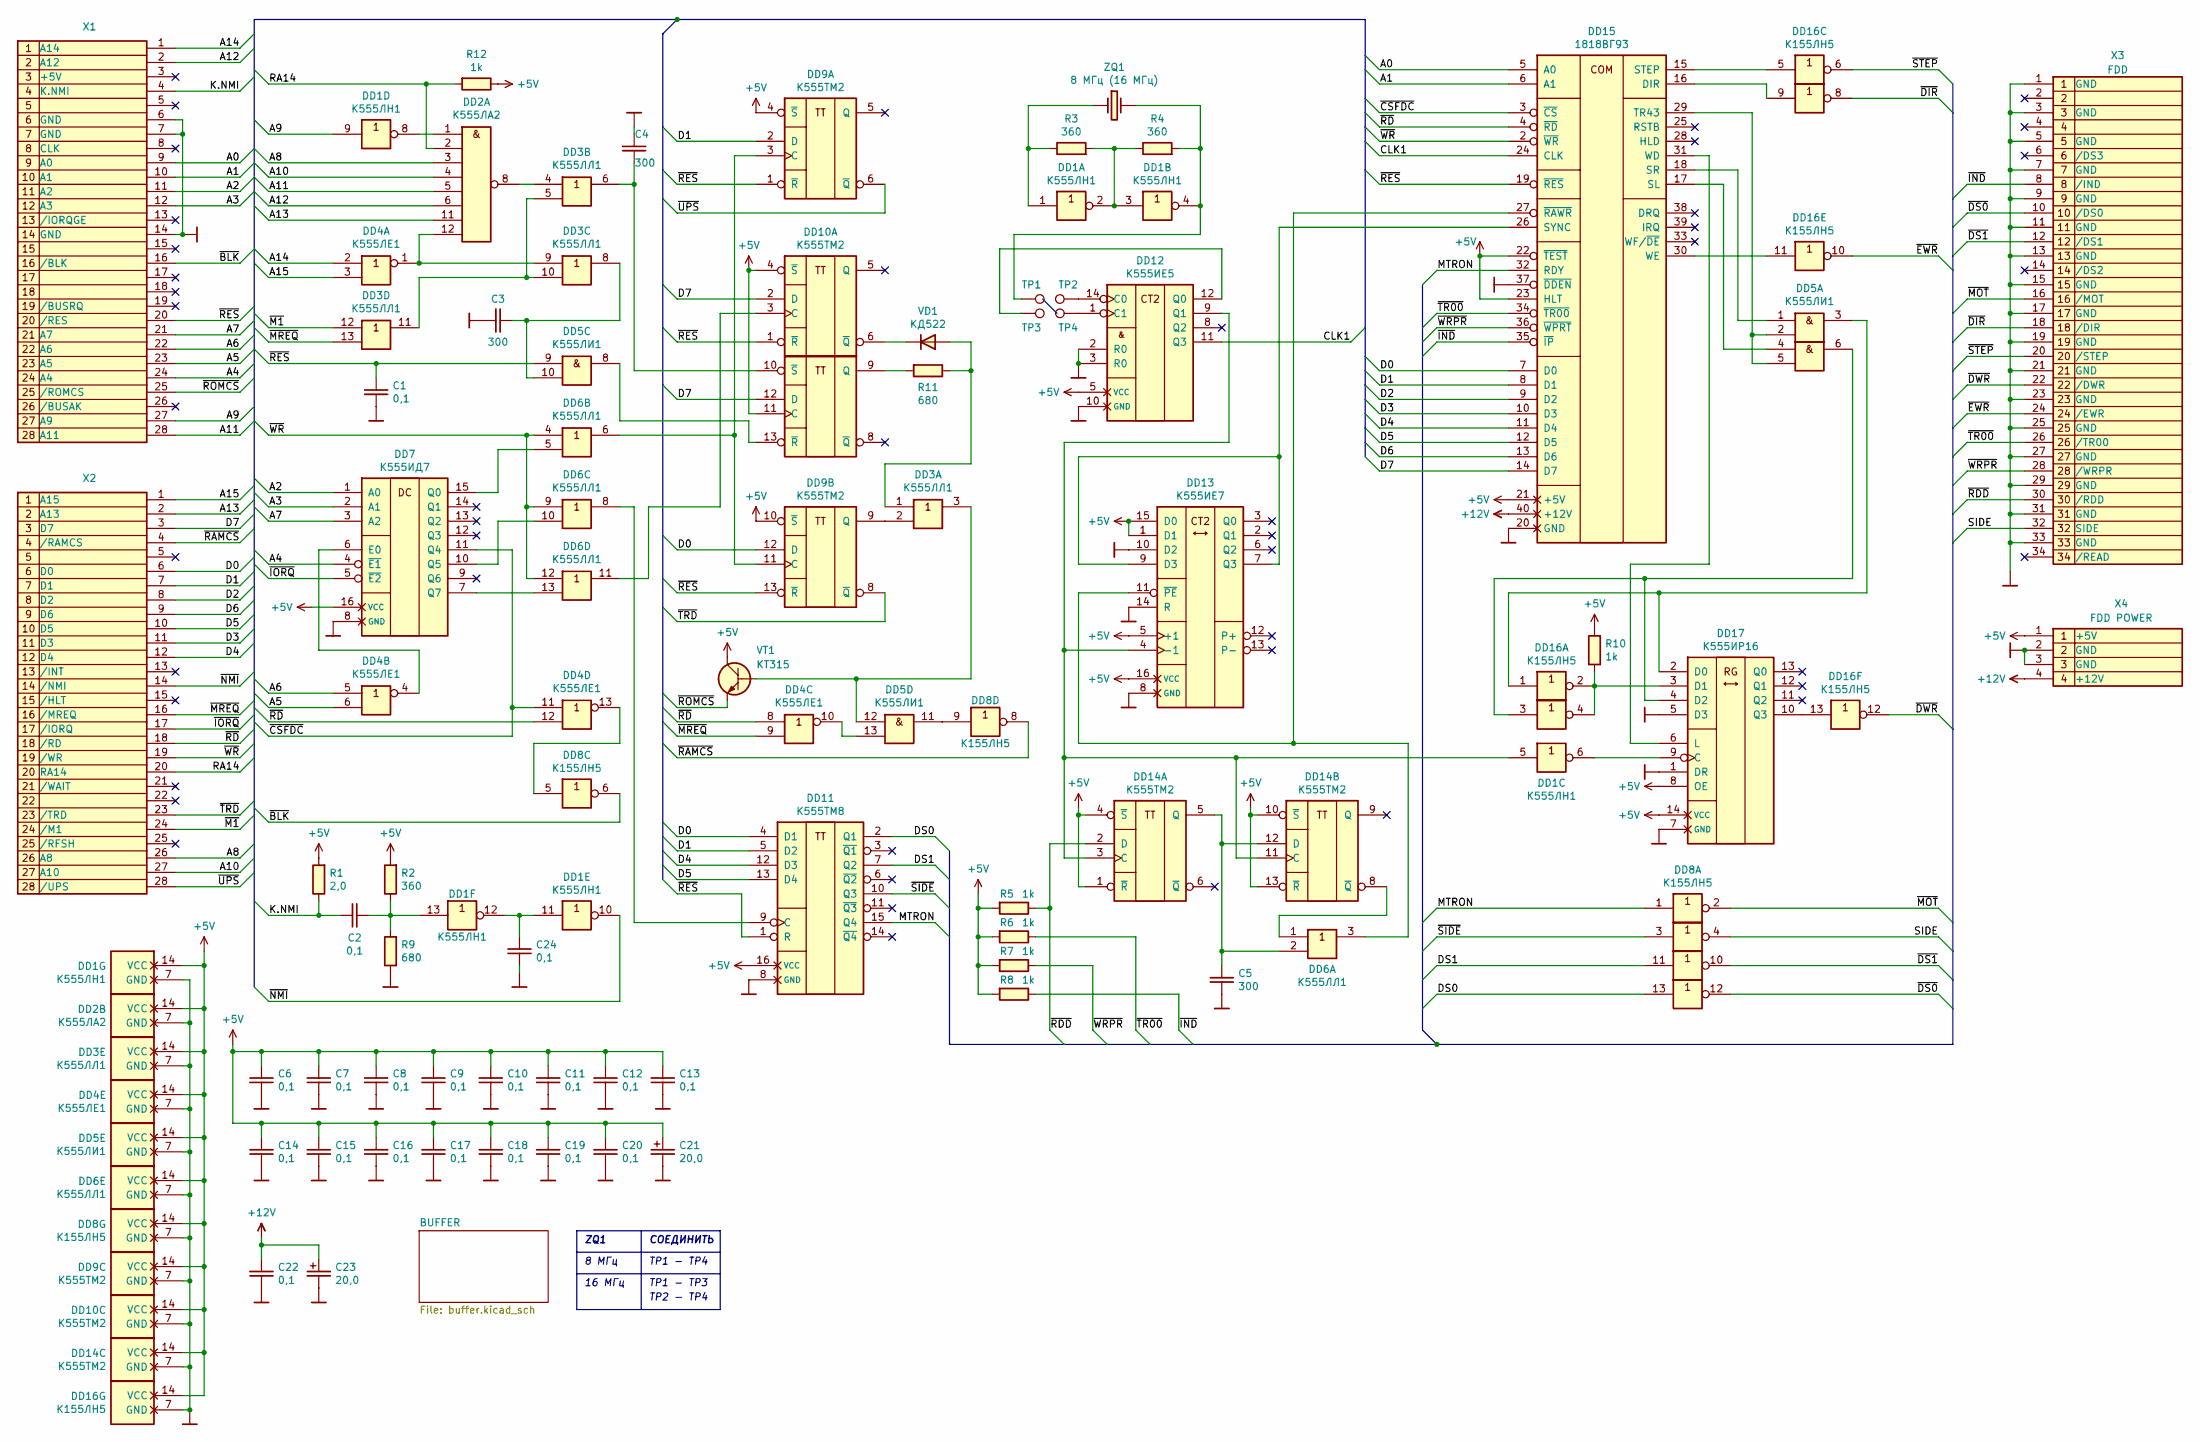
[picture p45: schematic quorum_disk_drive_emu.kicad_sch]

Parts:
C1, C2, C6, C7, C8, C9, C10, C11, C12, C13, C14, C15, C16, C17, C18, C19, C20, C22, C24: 0,1; C_Rect_L7.0mm_W2.0mm_P5.00mm
C3, C4, C5: 300; C_Rect_L7.0mm_W2.0mm_P5.00mm
C21, C23: 20,0; CP_Radial_D7.5mm_P2.50mm
DD1: К555ЛН1; DIP-14_W7.62mm_Socket_LongPads
DD2: К555ЛА2; DIP-14_W7.62mm_Socket_LongPads
DD3, DD6: К555ЛЛ1; DIP-14_W7.62mm_Socket_LongPads
DD4: К555ЛЕ1; DIP-14_W7.62mm_Socket_LongPads
DD5: К555ЛИ1; DIP-14_W7.62mm_Socket_LongPads
DD7: К555ИД7; DIP-16_W7.62mm_Socket_LongPads
DD8, DD16: К155ЛН5; DIP-14_W7.62mm_Socket_LongPads
DD9, DD10, DD14: К555ТМ2; DIP-14_W7.62mm_Socket_LongPads
DD11: К555ТМ8; DIP-16_W7.62mm_Socket_LongPads
DD12: К555ИЕ5; DIP-14_W7.62mm_Socket_LongPads
DD13: К555ИЕ7; DIP-16_W7.62mm_Socket_LongPads
DD15: 1818ВГ93; DIP-42_W15.24mm_Socket_LongPads
DD17: К555ИР16; DIP-14_W7.62mm_Socket_LongPads
R1: 2,0; R_Axial_DIN0207_L6.3mm_D2.5mm_P10.16mm_Horizontal
R2, R3, R4: 360; R_Axial_DIN0207_L6.3mm_D2.5mm_P10.16mm_Horizontal
R5, R6, R7, R8, R10, R12: 1k; R_Axial_DIN0207_L6.3mm_D2.5mm_P10.16mm_Horizontal
R9, R11: 680; R_Axial_DIN0207_L6.3mm_D2.5mm_P10.16mm_Horizontal
TP1, TP2, TP3, TP4: TestPoint; TestPoint_THTPad_D1.5mm_Drill0.7mm
VD1: КД522; D_DO-35_SOD27_P10.16mm_Horizontal
VT1: КТ315; TO-92_Inline_Wide
X1, X2: CONN_28; PinSocket_1x28_P2.54mm_Vertical
X3: FDD; IDC-Header_2x17_P2.54mm_Vertical
X4: FDD POWER; MOLEX-1X4
ZQ1: 8 МГц (16 МГц); Crystal_HC49-U_Vertical

Connections:
+5V: C6.2, C7.2, C8.2, C9.2, C10.2, C11.2, C12.2, C13.2, C14.2, C15.2, C16.2, C17.2, C18.2, C19.2, C20.2, C21.1, DD1.14 (VCC), DD2.14 (VCC), DD3.14 (VCC), DD4.14 (VCC), DD5.14 (VCC), DD6.14 (VCC), DD7.16 (VCC), DD8.14 (VCC), DD9.4 (~S), DD9.10 (~S), DD9.14 (VCC), DD10.4 (~S), DD10.11 (C), DD10.14 (VCC), DD11.16 (VCC), DD12.5 (VCC), DD13.1 (D1), DD13.5 (+1), DD13.15 (D0), DD13.16 (VCC), DD14.1 (~R), DD14.4 (~S), DD14.10 (~S), DD14.13 (~R), DD14.14 (VCC), DD15.21 (+5V), DD15.22 (~TEST), DD15.23 (HLT), DD16.14 (VCC), DD17.8 (OE), DD17.14 (VCC), R1.1 (L), R2.1 (L), R5.1 (L), R6.1 (L), R7.1 (L), R8.1 (L), R10.1 (L), R12.2 (R), VT1.3 (C), X4.1
+12V: C22.2, C23.1, DD15.40 (+12V), X4.4
A0: DD15.5 (A0), X1.9
A1: DD15.6 (A1), X1.10
A2: DD7.1 (A0), X1.11
A3: DD7.2 (A1), X1.12
A4: DD7.4 (~E1), X1.24
A5: DD4.6, X1.23
A6: DD4.5, X1.22
A7: DD7.3 (A2), X1.21
A8: DD2.3, X2.26
A9: DD1.9, X1.27
A10: DD2.4, X2.27
A11: DD2.5, X1.28
A12: DD2.6, X1.2
A13: DD2.11, X2.2
A14: DD4.2, X1.1
A15: DD4.3, X2.1
CLK1: DD12.11 (Q3), DD15.24 (CLK)
D0: DD9.12 (D), DD11.4 (D1), DD15.7 (D0), X2.6
D1: DD9.2 (D), DD11.5 (D2), DD15.8 (D1), X2.7
D2: DD15.9 (D2), X2.8
D3: DD15.10 (D3), X2.11
D4: DD11.12 (D3), DD15.11 (D4), X2.12
D5: DD11.13 (D4), DD15.12 (D5), X2.10
D6: DD15.13 (D6), X2.9
D7: DD10.2 (D), DD10.12 (D), DD15.14 (D7), X2.3
DS0: DD8.13, DD11.2 (Q1)
DS1: DD8.11, DD11.7 (Q2)
GND: C1.2, C3.2, C4.1, C5.2, C6.1, C7.1, C8.1, C9.1, C10.1, C11.1, C12.1, C13.1, C14.1, C15.1, C16.1, C17.1, C18.1, C19.1, C20.1, C21.2, C22.1, C23.2, C24.1, DD1.7 (GND), DD2.7 (GND), DD3.7 (GND), DD4.7 (GND), DD5.7 (GND), DD6.7 (GND), DD7.8 (GND), DD8.7 (GND), DD9.7 (GND), DD10.7 (GND), DD11.8 (GND), DD12.2 (R0), DD12.3 (R0), DD12.10 (GND), DD13.8 (GND), DD13.10 (D2), DD13.14 (R), DD14.7 (GND), DD15.20 (GND), DD15.37 (~DDEN), DD16.7 (GND), DD17.1 (DR), DD17.5 (D3), DD17.7 (GND), R9.2 (R), X1.6, X1.7, X1.14, X3.1, X3.3, X3.5, X3.7, X3.9, X3.11, X3.13, X3.15, X3.17, X3.19, X3.21, X3.23, X3.25, X3.27, X3.29, X3.31, X3.33, X4.2, X4.3
K.NMI: C2.2, R1.2 (R), X1.4
MTRON: DD8.1, DD11.15 (Q4), DD15.32 (RDY)
unnamed: C2.1, DD1.13, R2.2 (R), R9.1 (L)
unnamed: C3.1, DD3.8, DD5.10
unnamed: C4.2, DD3.6, DD10.10 (~S)
unnamed: C5.1, DD6.2, DD14.5 (Q), DD14.12 (D)
unnamed: C24.2, DD1.11, DD1.12
unnamed: DD1.1, R3.2 (R), ZQ1.1
unnamed: DD1.2, DD1.3, R3.1 (L), R4.2 (R)
unnamed: DD1.4, R4.1 (L), TP1.1, ZQ1.2
unnamed: DD1.5, DD12.9 (Q1), DD13.4 (-1), DD14.3 (C), DD14.11 (C)
unnamed: DD1.6, DD17.9 (C)
unnamed: DD1.8, DD2.1
unnamed: DD2.8, DD3.4
unnamed: DD2.12, DD3.9, DD4.1
unnamed: DD3.1, R11.2 (R), VD1.2 (A)
unnamed: DD3.2, DD9.9 (Q)
unnamed: DD3.3, DD5.12, VT1.2 (B)
unnamed: DD3.5, DD3.10, DD3.11
unnamed: DD4.4, DD7.6 (E0)
unnamed: DD4.10, DD5.13
unnamed: DD4.13, DD8.5
unnamed: DD5.11, DD8.9
unnamed: DD6.5, DD7.15 (Q0)
unnamed: DD6.6, DD9.3 (C), DD9.11 (C)
unnamed: DD6.10, DD7.10 (Q5)
unnamed: DD6.13, DD7.7 (Q7)
unnamed: DD6.11, DD10.3 (C)
unnamed: DD10.6 (~Q), VD1.1 (K)
unnamed: DD10.9 (Q), R11.1 (L)
unnamed: DD5.8, DD10.13 (~R)
unnamed: DD6.8, DD11.9 (C)
unnamed: DD12.1 (С1), TP4.1
unnamed: DD12.12 (Q0), TP3.1
unnamed: DD12.14 (С0), TP2.1
unnamed: DD13.7 (Q3), DD13.9 (D3), DD15.26 (SYNC)
unnamed: DD6.3, DD13.11 (~PE), DD15.27 (~RAWR)
unnamed: DD6.1, DD14.8 (~Q)
unnamed: DD15.15 (STEP), DD16.5
unnamed: DD15.16 (DIR), DD16.9
unnamed: DD5.4, DD15.17 (SL)
unnamed: DD5.1, DD15.18 (SR)
unnamed: DD5.2, DD5.5, DD15.29 (TR43)
unnamed: DD15.30 (WE), DD16.11
unnamed: DD15.31 (WD), DD17.6 (L)
unnamed: DD5.3, DD16.1, DD17.2 (D0)
unnamed: DD16.2, DD16.4, DD17.3 (D1), R10.2 (R)
unnamed: DD5.6, DD16.3, DD17.4 (D2)
unnamed: DD16.13, DD17.10 (Q3)
RA14: DD2.2, R12.1 (L), X2.20
SIDE: DD8.4, X3.32
~BLK: DD8.6, X1.16
~CSFDC: DD4.11, DD7.11 (Q4), DD15.3 (~CS)
~DIR: DD16.8, X3.18
~DS0: DD8.12, X3.10
~DS1: DD8.10, X3.12
~DWR: DD16.12, X3.22
~EWR: DD16.10, X3.24
~IND: DD15.35 (~IP), R8.2 (R), X3.8
~IORQ: DD7.5 (~E2), X2.17
~M1: DD3.12, X2.24
~MOT: DD8.2, X3.16
~MREQ: DD3.13, DD4.9, X2.16
~NMI: DD1.10, X2.14
~RAMCS: DD8.8, X2.4
~RDD: DD14.2 (D), R5.2 (R), X3.30
~RD: DD4.8, DD4.12, DD15.4 (~RD), X2.18
~RES: C1.1, DD5.9, DD9.1 (~R), DD9.13 (~R), DD10.1 (~R), DD11.1 (R), DD15.19 (~RES), X1.20
~ROMCS: VT1.1 (E), X1.25
~SIDE: DD8.3, DD11.10 (Q3)
~STEP: DD16.6, X3.20
~TR00: DD15.34 (~TR00), R6.2 (R), X3.26
~TRD: DD9.8 (~Q), X2.23
~UPS: DD9.6 (~Q), X2.28
~WRPR: DD15.36 (~WPRT), R7.2 (R), X3.28
~WR: DD6.4, DD6.9, DD6.12, DD15.2 (~WR), X2.19

Notes on the sheet:
СОЕДИНИТЬ
ZQ1
TP2 - TP4
TP1 - TP4
TP1 - TP3
8 МГц
16 МГц
