UncleRus/quorum-reborn/kicad/Magic-05/Magic-05.kicad_sch

## KiCad design kicad/Magic-05/Magic-05.kicad_sch (2023-06-19)

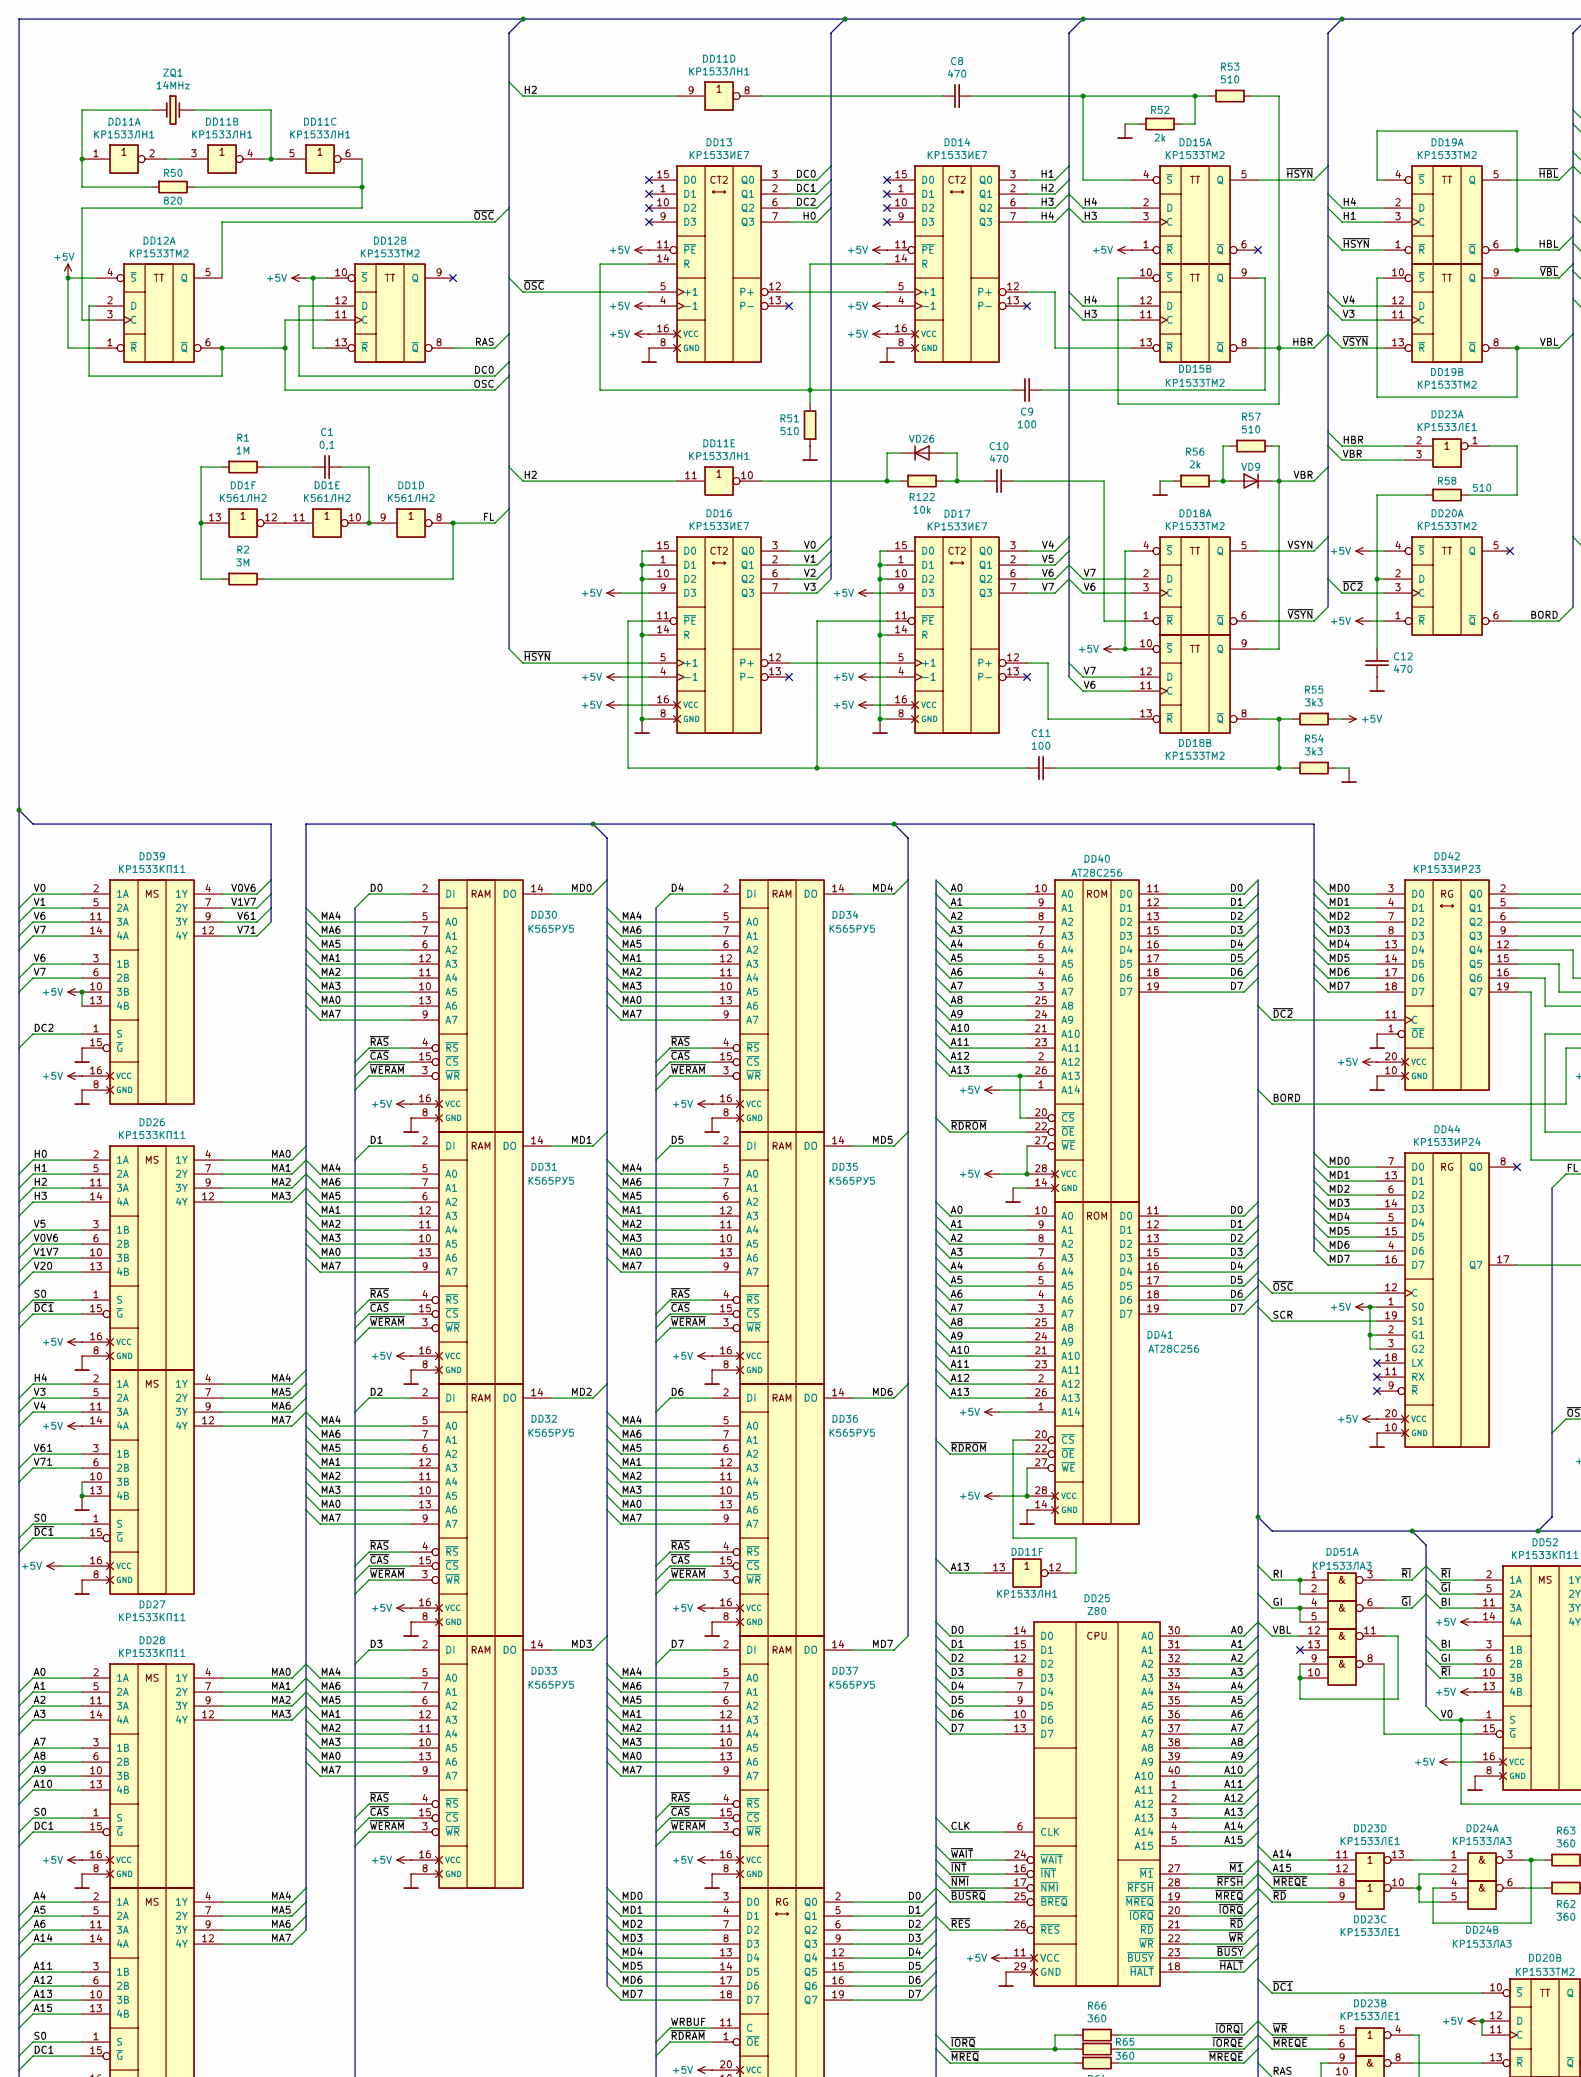
[picture p46: schematic Magic-05.kicad_sch, part in row 1, column 1]

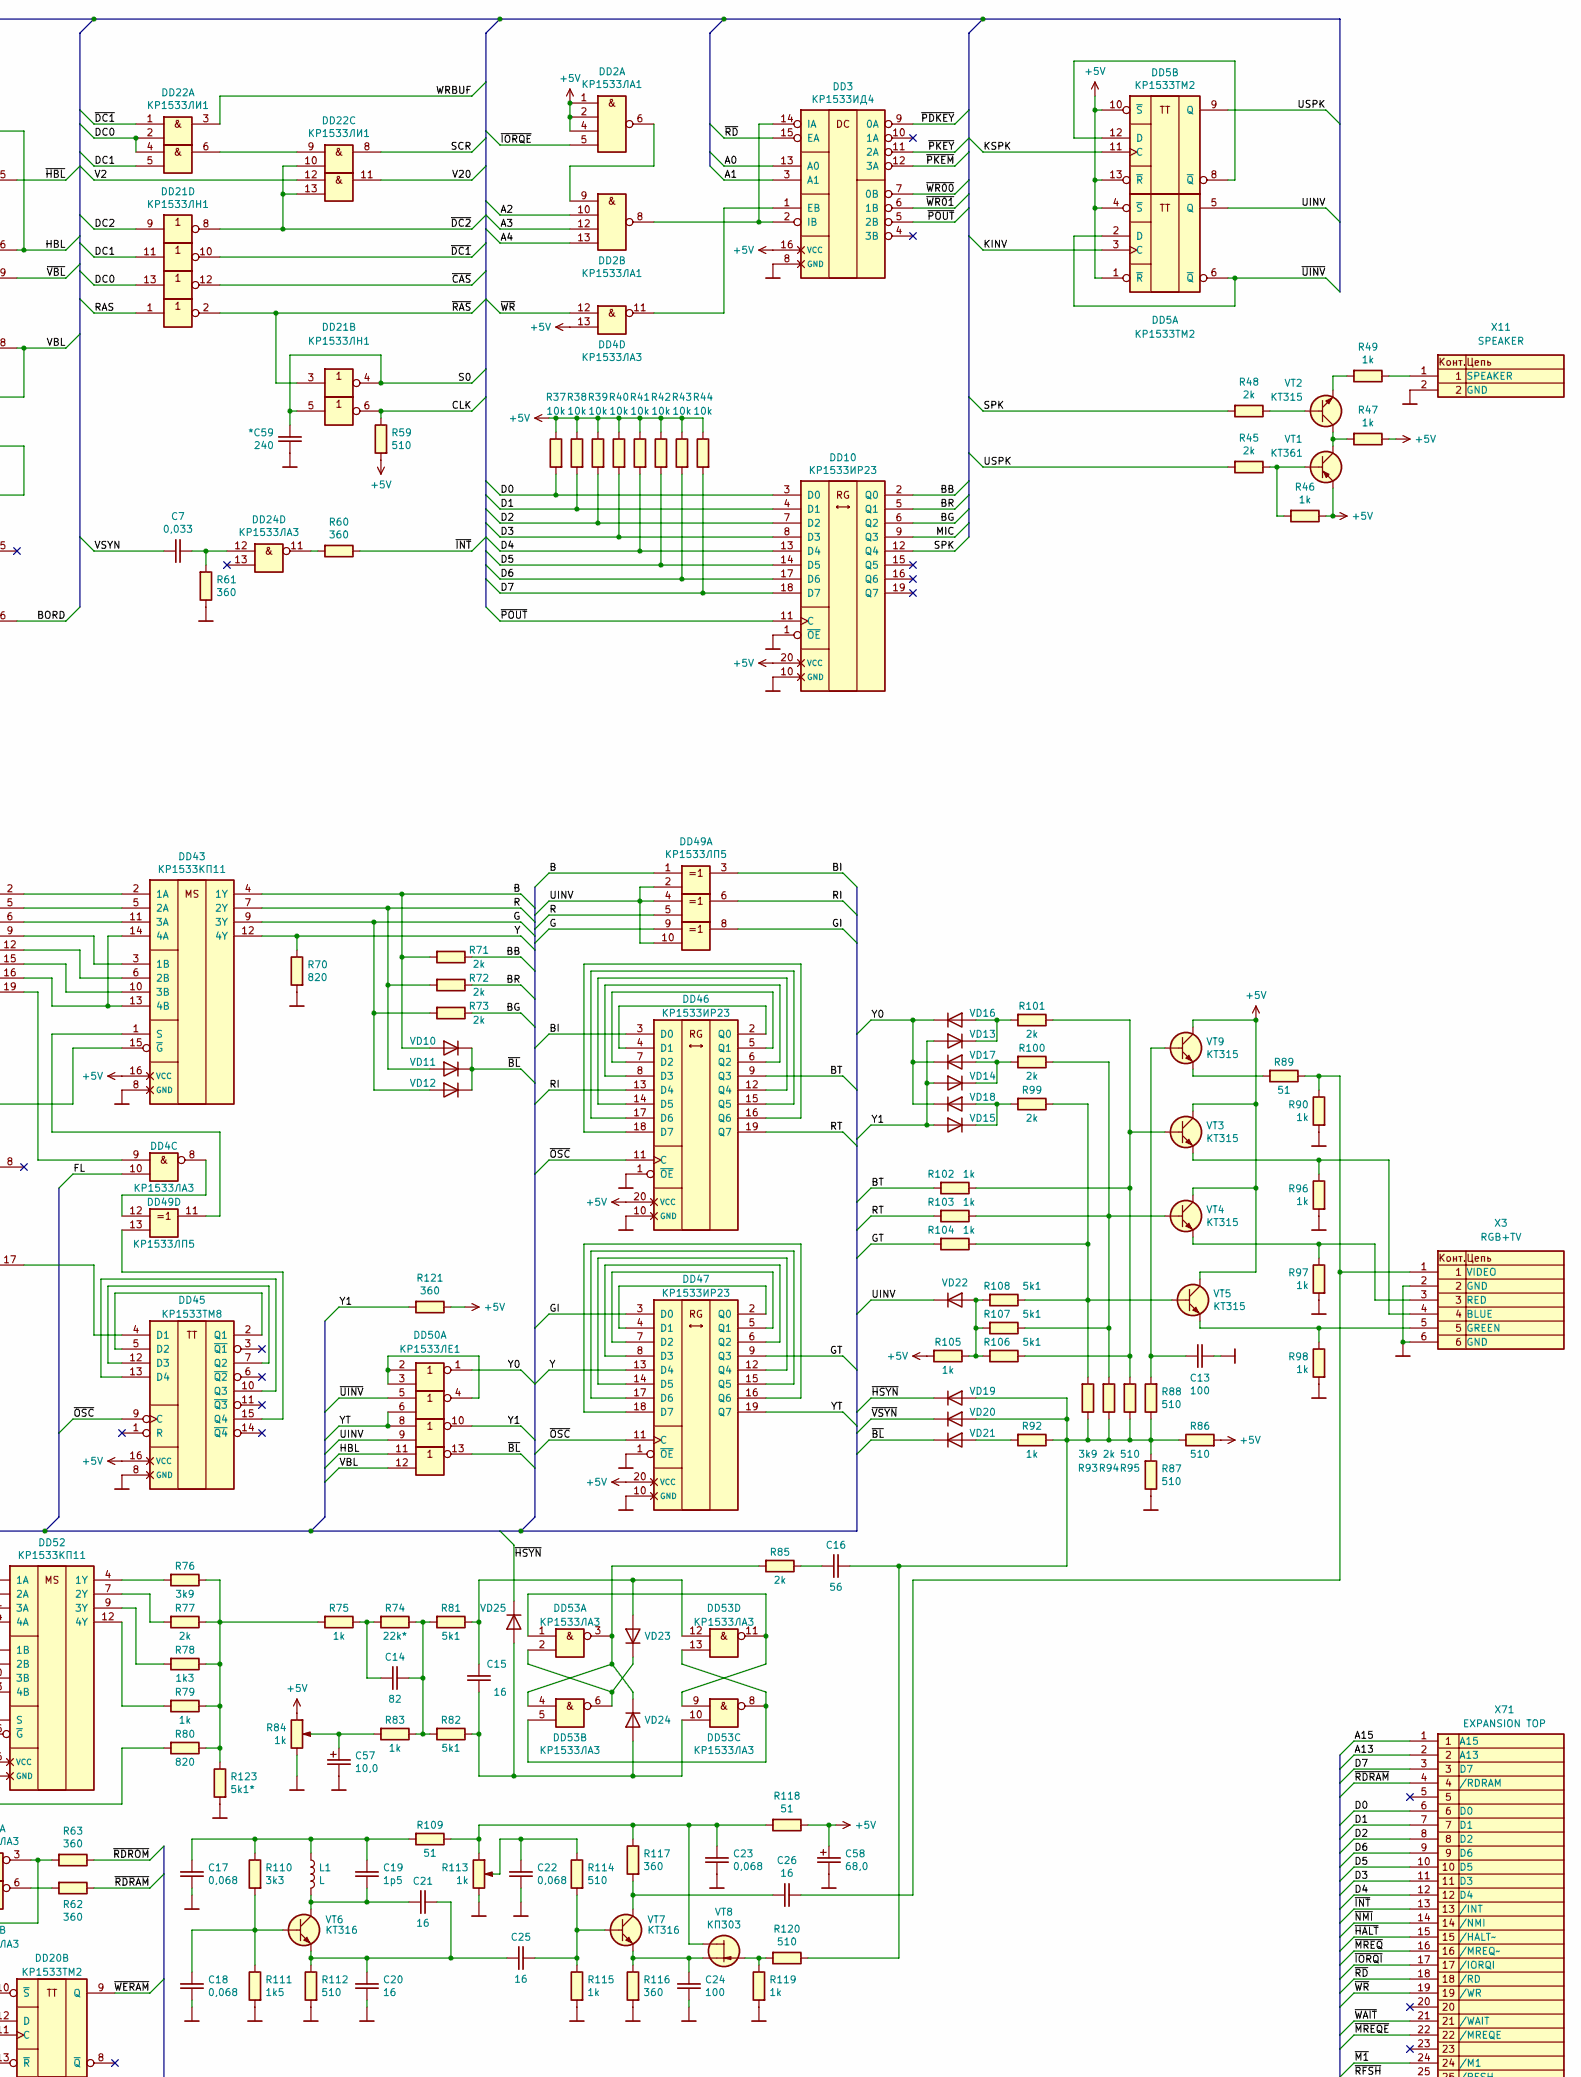
[picture p47: schematic Magic-05.kicad_sch, part in row 1, column 2]

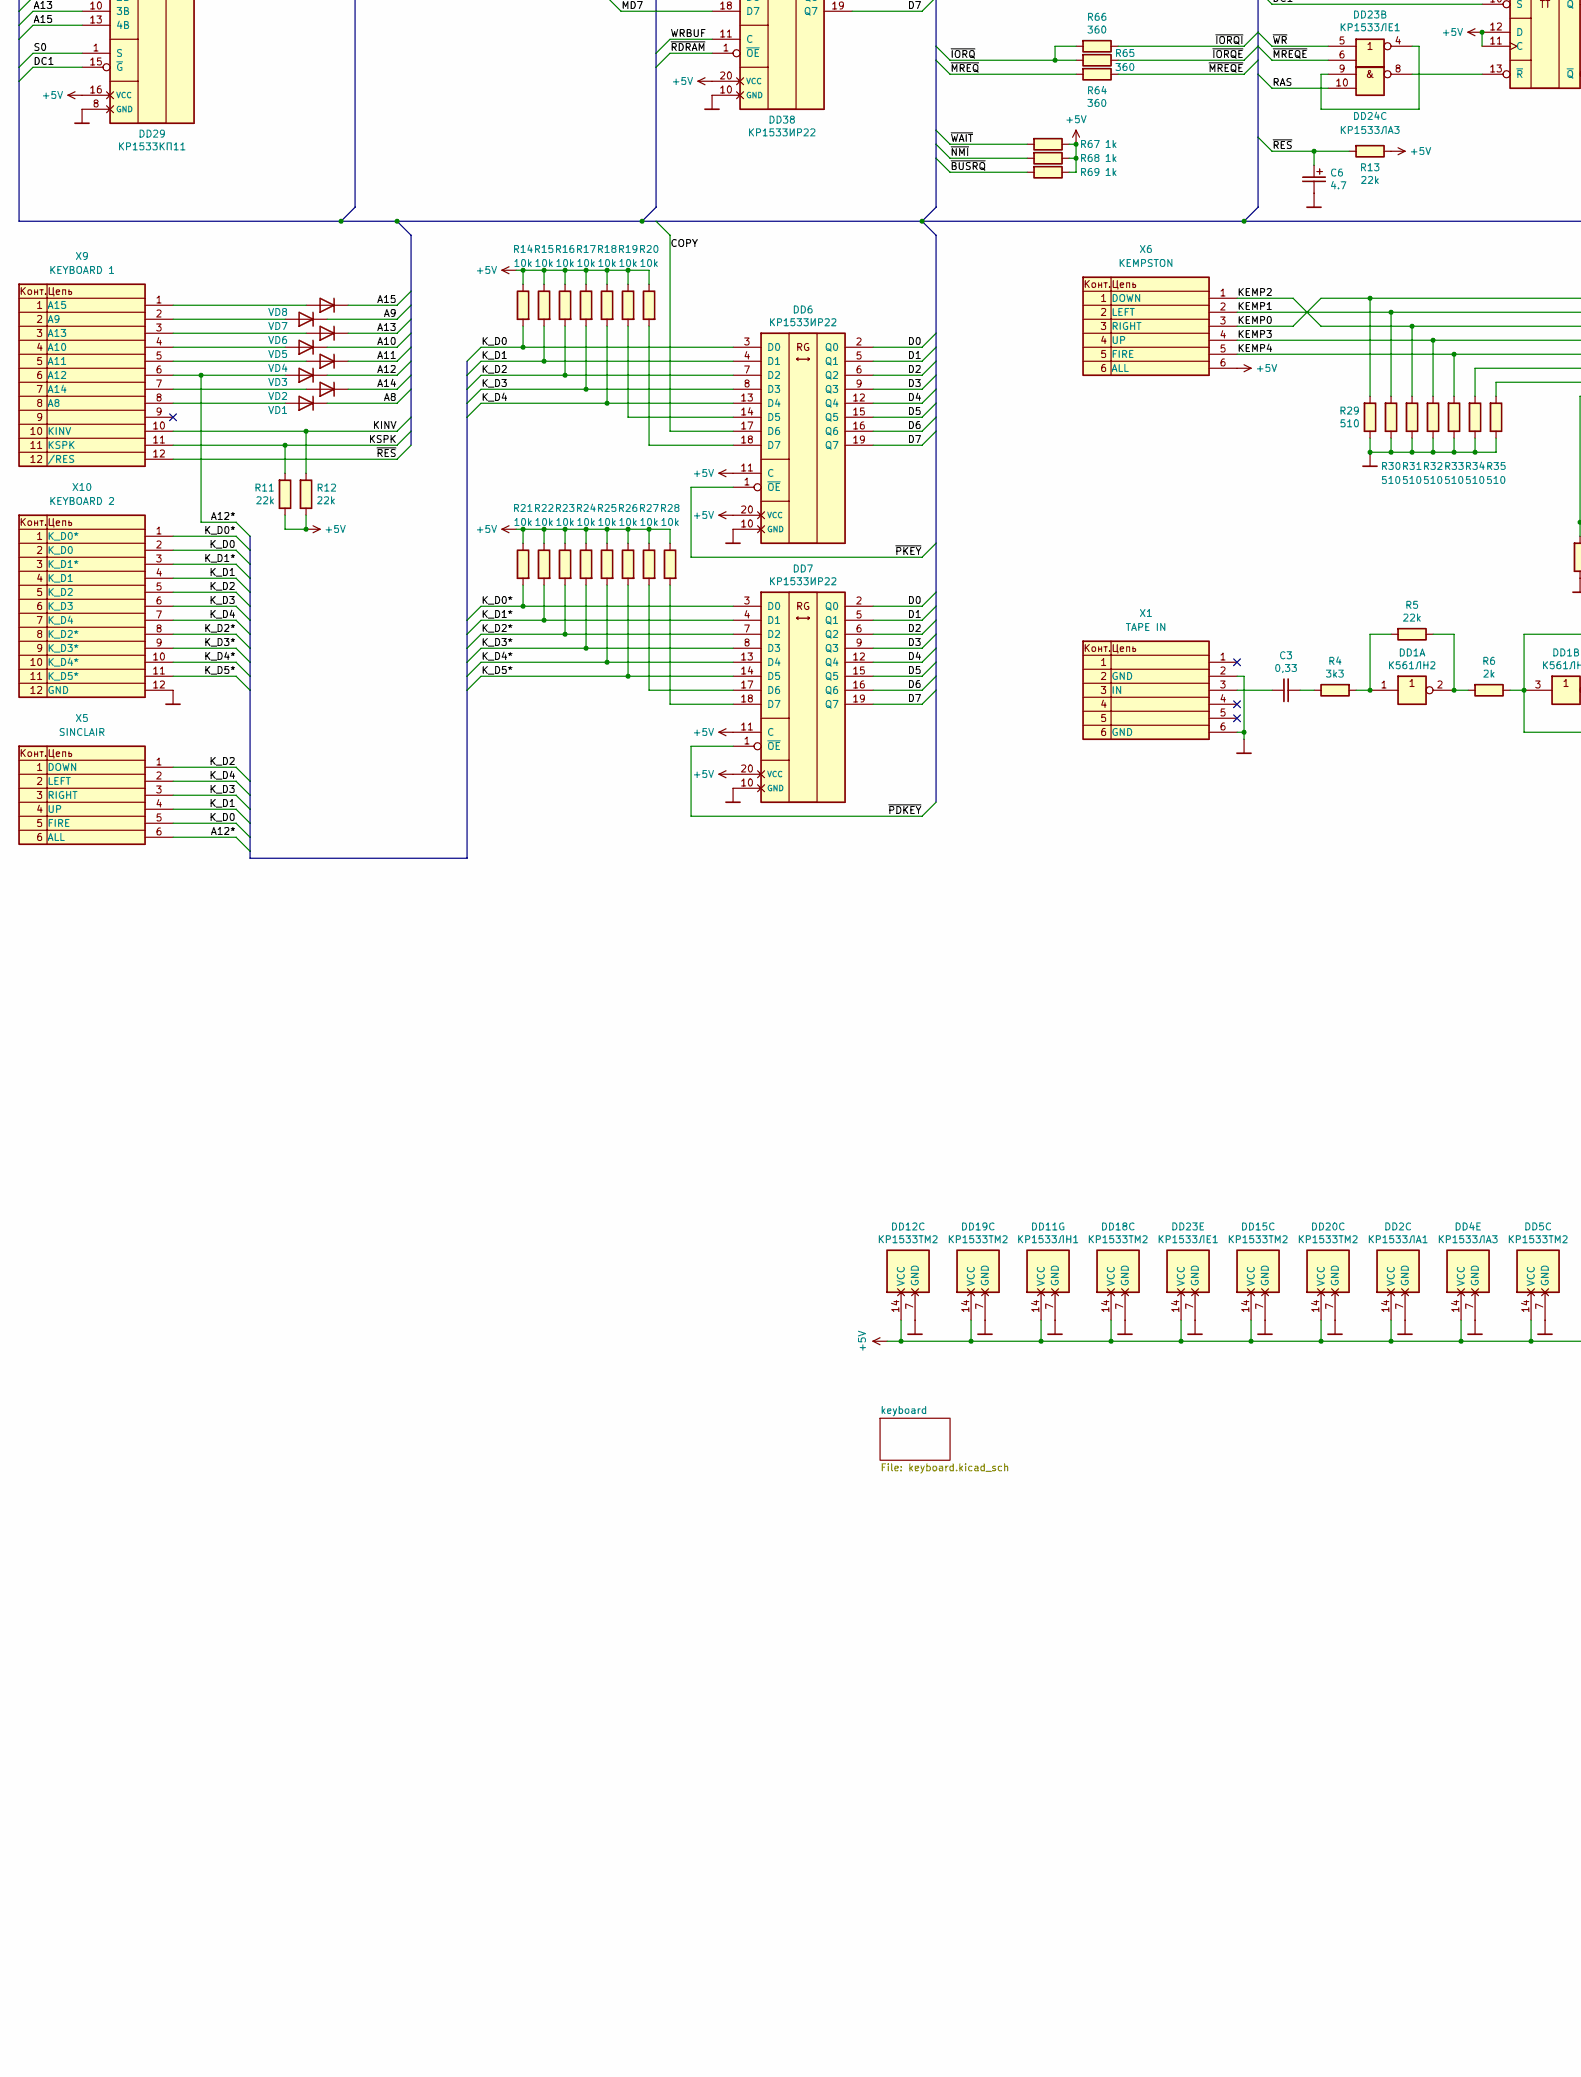
[picture p48: schematic Magic-05.kicad_sch, part in row 2, column 1]

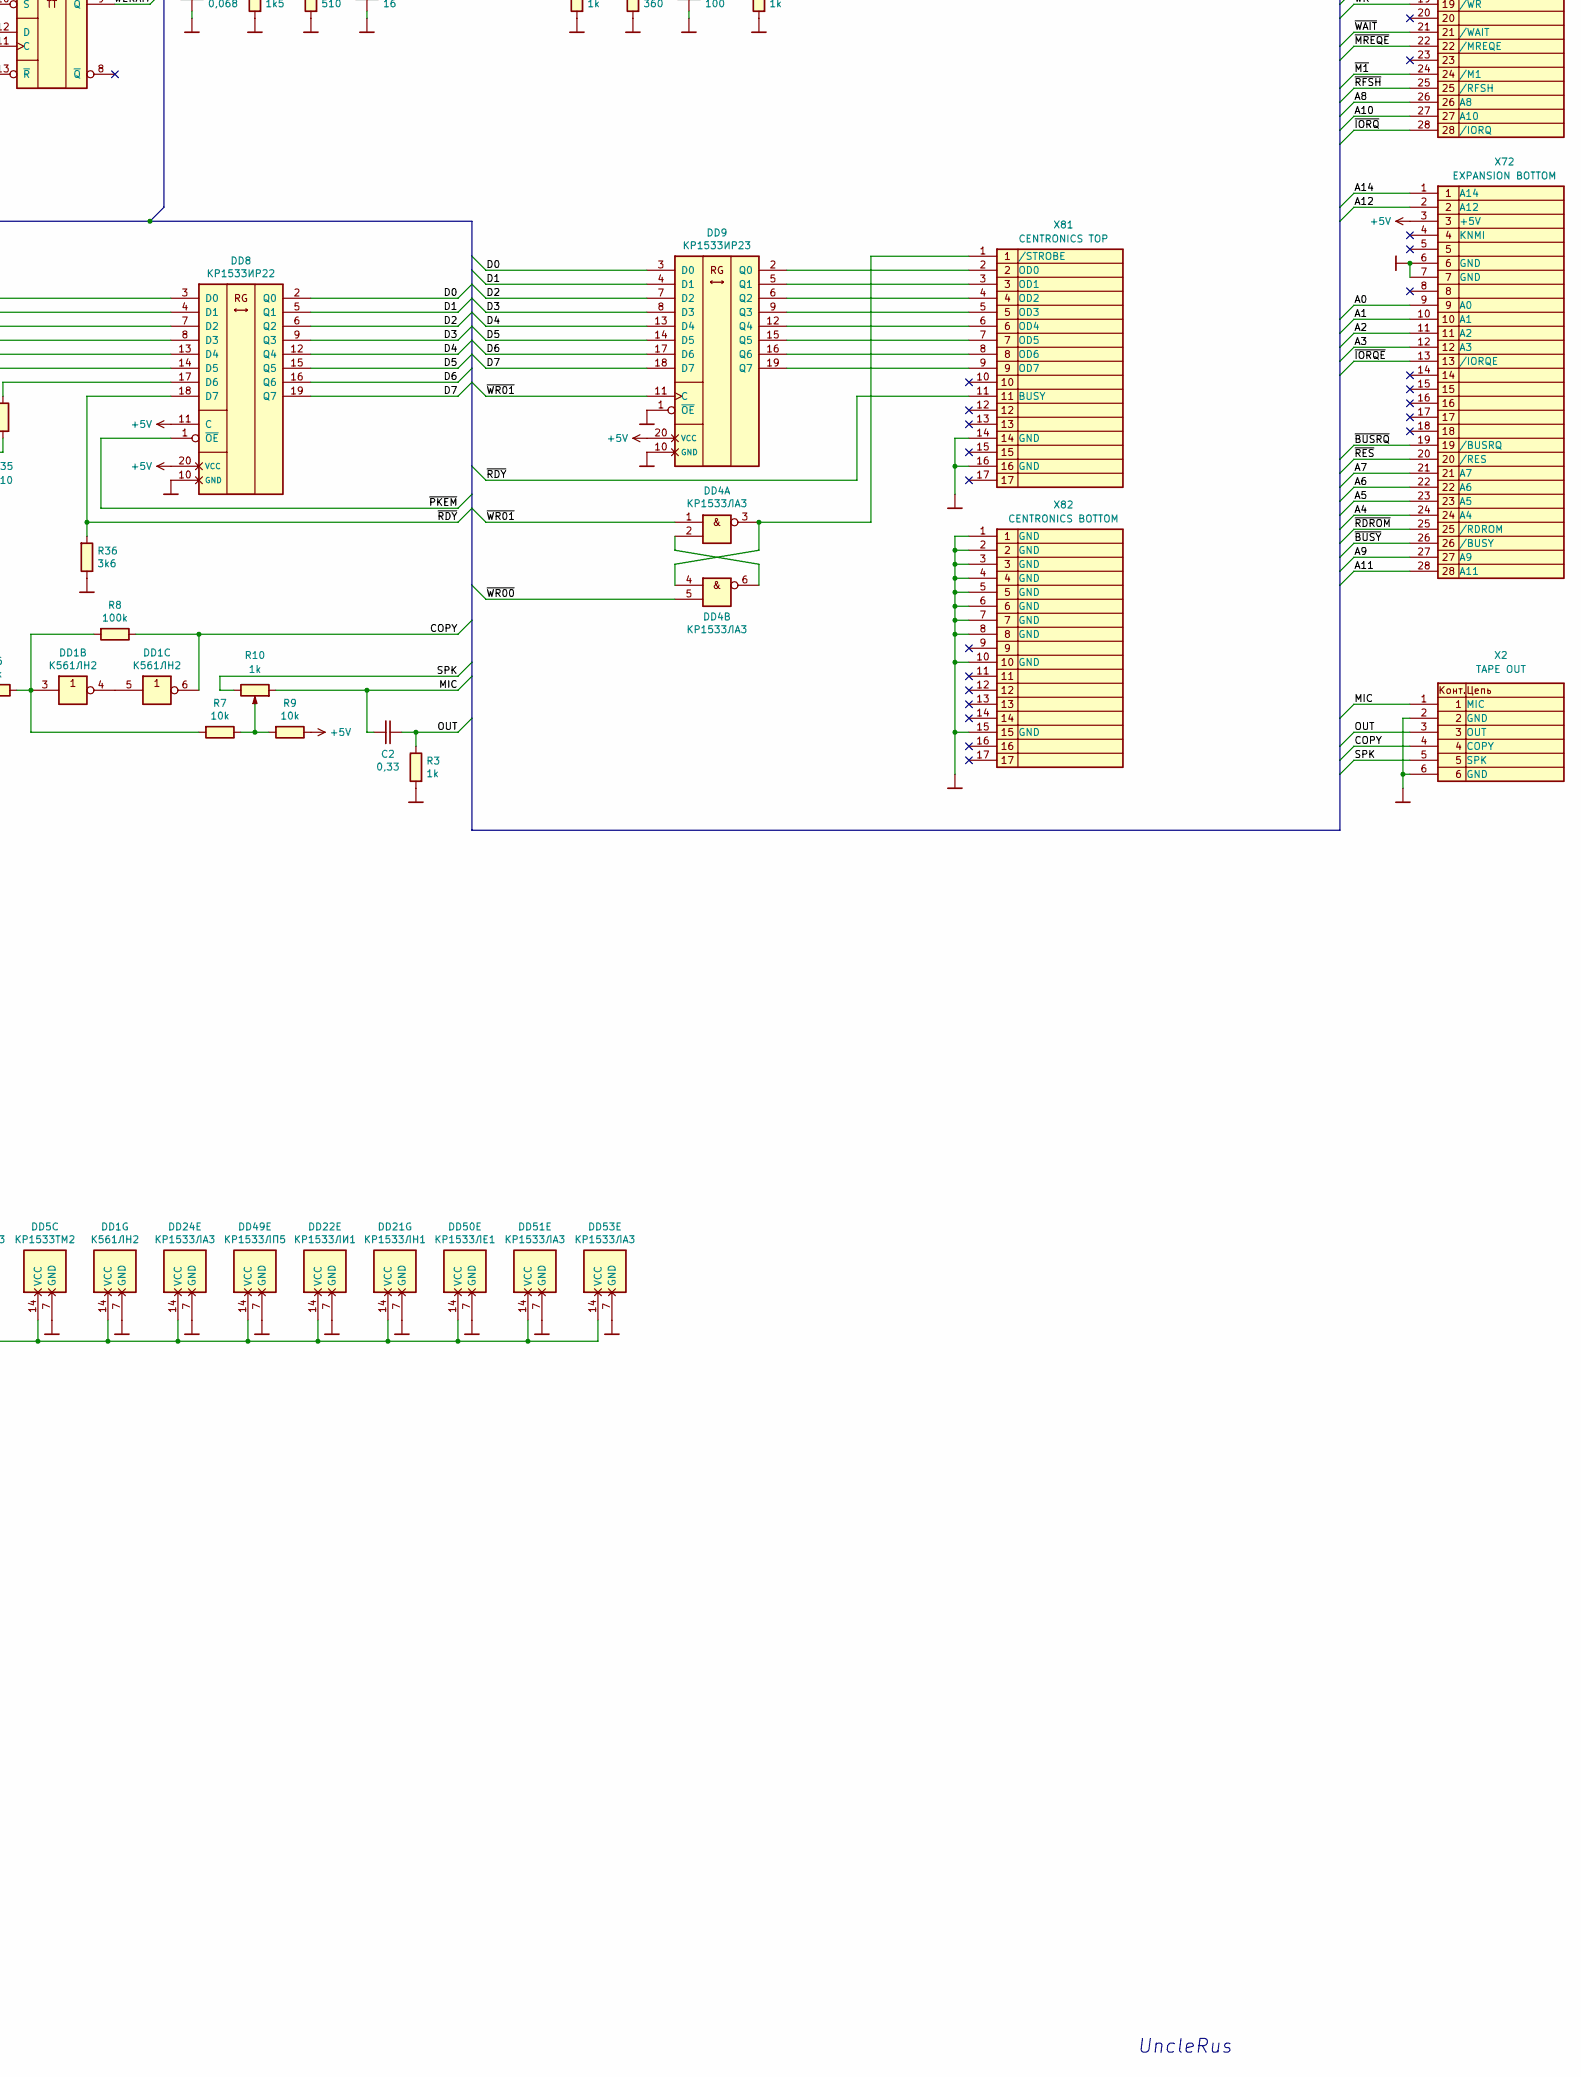
[picture p49: schematic Magic-05.kicad_sch, part in row 2, column 2]

Parts:
*C59: 240; C_Rect_L7.0mm_W2.5mm_P5.00mm
C1: 0,1; C_Rect_L7.0mm_W2.5mm_P5.00mm
C2, C3: 0,33; C_Rect_L7.0mm_W2.5mm_P5.00mm
C6: 4.7; CP_Radial_D7.5mm_P2.50mm
C7: 0,033; C_Rect_L7.0mm_W2.5mm_P5.00mm
C8, C10, C12: 470; C_Rect_L7.0mm_W2.5mm_P5.00mm
C9, C11, C13, C24: 100; C_Rect_L7.0mm_W2.5mm_P5.00mm
C14: 82; C_Rect_L7.0mm_W2.5mm_P5.00mm
C15, C20, C21, C25, C26: 16; C_Rect_L7.0mm_W2.5mm_P5.00mm
C16: 56; C_Rect_L7.0mm_W2.5mm_P5.00mm
C17, C18, C22, C23: 0,068; C_Rect_L7.0mm_W2.5mm_P5.00mm
C19: 1p5; C_Rect_L7.0mm_W2.5mm_P5.00mm
C57: 10,0; CP_Radial_D7.5mm_P2.50mm
C58: 68,0; CP_Radial_D7.5mm_P2.50mm
DD1: К561ЛН2; DIP-14_W7.62mm_Socket_LongPads
DD2: КР1533ЛА1; DIP-14_W7.62mm_Socket_LongPads
DD3: КР1533ИД4; DIP-16_W7.62mm_Socket_LongPads
DD4, DD24, DD51, DD53: КР1533ЛА3; DIP-14_W7.62mm_Socket_LongPads
DD5, DD12, DD15, DD18, DD19, DD20: КР1533ТМ2; DIP-14_W7.62mm_Socket_LongPads
DD6, DD7, DD8, DD38: КР1533ИР22; DIP-20_W7.62mm_Socket_LongPads
DD9, DD10, DD42, DD46, DD47: КР1533ИР23; DIP-20_W7.62mm_Socket_LongPads
DD11, DD21: КР1533ЛН1; DIP-14_W7.62mm_Socket_LongPads
DD13, DD14, DD16, DD17: КР1533ИЕ7; DIP-16_W7.62mm_Socket_LongPads
DD22: КР1533ЛИ1; DIP-14_W7.62mm_Socket_LongPads
DD23, DD50: КР1533ЛЕ1; DIP-14_W7.62mm_Socket_LongPads
DD25: Z80; DIP-40_W15.24mm_Socket_LongPads
DD26, DD27, DD28, DD29, DD39, DD43, DD52: КР1533КП11; DIP-16_W7.62mm_Socket_LongPads
DD30, DD31, DD32, DD33, DD34, DD35, DD36, DD37: К565РУ5; DIP-16_W7.62mm_Socket_LongPads
DD40, DD41: AT28C256; DIP-28_W15.24mm_Socket_LongPads
DD44: КР1533ИР24; DIP-20_W7.62mm_Socket_LongPads
DD45: КР1533ТМ8; DIP-16_W7.62mm_Socket_LongPads
DD49: КР1533ЛП5; DIP-14_W7.62mm_Socket_LongPads
L1: L
R1: 1M; R_Axial_DIN0204_L3.6mm_D1.6mm_P7.62mm_Horizontal
R2: 3M; R_Axial_DIN0204_L3.6mm_D1.6mm_P7.62mm_Horizontal
R3, R46, R47, R49, R67, R68, R69, R75, R79, R83, R90, R92, R96, R97, R98, R102, R103, R104, R105, R115, R119: 1k; R_Axial_DIN0204_L3.6mm_D1.6mm_P7.62mm_Horizontal
R4, R54, R55, R110: 3k3; R_Axial_DIN0204_L3.6mm_D1.6mm_P7.62mm_Horizontal
R5, R11, R12, R13: 22k; R_Axial_DIN0204_L3.6mm_D1.6mm_P7.62mm_Horizontal
R6, R45, R48, R52, R56, R71, R72, R73, R77, R85, R94, R99, R100, R101: 2k; R_Axial_DIN0204_L3.6mm_D1.6mm_P7.62mm_Horizontal
R7, R9, R14, R15, R16, R17, R18, R19, R20, R21, R22, R23, R24, R25, R26, R27, R28, R37, R38, R39, R40, R41, R42, R43, R44, R122: 10k; R_Axial_DIN0204_L3.6mm_D1.6mm_P7.62mm_Horizontal
R8: 100k; R_Axial_DIN0204_L3.6mm_D1.6mm_P7.62mm_Horizontal
R10, R84, R113: 1k; Potentiometer_Bourns_3296Y_Vertical
R29, R30, R31, R32, R33, R34, R35, R51, R53, R57, R58, R59, R86, R87, R88, R95, R112, R114, R120: 510; R_Axial_DIN0204_L3.6mm_D1.6mm_P7.62mm_Horizontal
R36: 3k6; R_Axial_DIN0204_L3.6mm_D1.6mm_P7.62mm_Horizontal
R50, R70, R80: 820; R_Axial_DIN0204_L3.6mm_D1.6mm_P7.62mm_Horizontal
R60, R61, R62, R63, R64, R65, R66, R116, R117, R121: 360; R_Axial_DIN0204_L3.6mm_D1.6mm_P7.62mm_Horizontal
R74: 22k*; R_Axial_DIN0204_L3.6mm_D1.6mm_P7.62mm_Horizontal
R76, R93: 3k9; R_Axial_DIN0204_L3.6mm_D1.6mm_P7.62mm_Horizontal
R78: 1k3; R_Axial_DIN0204_L3.6mm_D1.6mm_P7.62mm_Horizontal
R81, R82, R106, R107, R108: 5k1; R_Axial_DIN0204_L3.6mm_D1.6mm_P7.62mm_Horizontal
R89, R109, R118: 51; R_Axial_DIN0204_L3.6mm_D1.6mm_P7.62mm_Horizontal
R111: 1k5; R_Axial_DIN0204_L3.6mm_D1.6mm_P7.62mm_Horizontal
R123: 5k1*; R_Axial_DIN0204_L3.6mm_D1.6mm_P7.62mm_Horizontal
VD1, VD2, VD3, VD4, VD5, VD6, VD7, VD8, VD9, VD10, VD11, VD12, VD13, VD14, VD15, VD16, VD17, VD18, VD19, VD20, VD21, VD22, VD23, VD24, VD25, VD26: D; D_DO-35_SOD27_P7.62mm_Horizontal
VT1: KT361; TO-92_Inline_Wide
VT2, VT3, VT4, VT5, VT9: KT315; TO-92_Inline_Wide
VT6, VT7: КТ316; TO-92_Inline_Wide
VT8: КП303; TO-92_Inline_Wide
X1: TAPE IN; DIN5-RA-PTH
X2: TAPE OUT; DIN5-RA-PTH
X3: RGB+TV; DIN5-RA-PTH
X5: SINCLAIR; DIN5-RA-PTH
X6: KEMPSTON; DIN5-RA-PTH
X9: KEYBOARD 1; PinHeader_1x12_P2.54mm_Vertical
X10: KEYBOARD 2; PinHeader_1x12_P2.54mm_Vertical
X11: SPEAKER; PinHeader_1x02_P2.54mm_Vertical
X71: EXPANSION TOP
X72: EXPANSION BOTTOM
X81: CENTRONICS TOP
X82: CENTRONICS BOTTOM
ZQ1: 14MHz; Crystal_HC49-U_Horizontal_1EP_style2

Connections:
+5V: C58.1, DD1.14 (VCC), DD2.1, DD2.2, DD2.4, DD2.14 (VCC), DD3.16 (VCC), DD4.13, DD4.14 (VCC), DD5.1 (~R), DD5.4 (~S), DD5.10 (~S), DD5.13 (~R), DD5.14 (VCC), DD6.11 (C), DD6.20 (VCC), DD7.11 (C), DD7.20 (VCC), DD8.11 (C), DD8.20 (VCC), DD9.20 (VCC), DD10.20 (VCC), DD11.14 (VCC), DD12.1 (~R), DD12.4 (~S), DD12.10 (~S), DD12.13 (~R), DD12.14 (VCC), DD13.4 (-1), DD13.11 (~PE), DD13.16 (VCC), DD14.4 (-1), DD14.11 (~PE), DD14.16 (VCC), DD15.1 (~R), DD15.14 (VCC), DD16.4 (-1), DD16.9 (D3), DD16.16 (VCC), DD17.4 (-1), DD17.9 (D3), DD17.16 (VCC), DD18.4 (~S), DD18.10 (~S), DD18.14 (VCC), DD19.14 (VCC), DD20.1 (~R), DD20.4 (~S), DD20.11 (C), DD20.12 (D), DD20.14 (VCC), DD21.14 (VCC), DD22.14 (VCC), DD23.14 (VCC), DD24.14 (VCC), DD25.11 (VCC), DD26.16 (VCC), DD27.14 (4A), DD27.16 (VCC), DD28.16 (VCC), DD29.16 (VCC), DD30.16 (VCC), DD31.16 (VCC), DD32.16 (VCC), DD33.16 (VCC), DD34.16 (VCC), DD35.16 (VCC), DD36.16 (VCC), DD37.16 (VCC), DD38.20 (VCC), DD39.10 (3B), DD39.13 (4B), DD39.16 (VCC), DD40.1 (A14), DD40.27 (~WE), DD40.28 (VCC), DD41.1 (A14), DD41.27 (~WE), DD41.28 (VCC), DD42.20 (VCC), DD43.16 (VCC), DD44.1 (S0), DD44.2 (G1), DD44.3 (G2), DD44.20 (VCC), DD45.16 (VCC), DD46.20 (VCC), DD47.20 (VCC), DD49.14 (VCC), DD50.14 (VCC), DD51.14 (VCC), DD52.13 (4B), DD52.14 (4A), DD52.16 (VCC), DD53.14 (VCC), R9.2 (R), R11.2 (R), R12.2 (R), R13.2 (R), R14.2 (R), R15.2 (R), R16.2 (R), R17.2 (R), R18.2 (R), R19.2 (R), R20.2 (R), R21.2 (R), R22.2 (R), R23.2 (R), R24.2 (R), R25.2 (R), R26.2 (R), R27.2 (R), R28.2 (R), R37.2 (R), R38.2 (R), R39.2 (R), R40.2 (R), R41.2 (R), R42.2 (R), R43.2 (R), R44.2 (R), R46.2 (R), R47.2 (R), R55.1 (L), R59.1 (L), R67.2 (R), R68.2 (R), R69.2 (R), R84.1 (L), R86.1 (L), R105.1 (L), R118.2 (R), R121.2 (R), VT1.1 (E), VT3.3 (C), VT4.3 (C), VT5.3 (C), VT9.3 (C), X6.6, X72.3
A0: DD3.13 (A0), DD25.30 (A0), DD28.2 (1A), DD40.10 (A0), DD41.10 (A0), X72.9
A1: DD3.3 (A1), DD25.31 (A1), DD28.5 (2A), DD40.9 (A1), DD41.9 (A1), X72.10
A2: DD2.10, DD25.32 (A2), DD28.11 (3A), DD40.8 (A2), DD41.8 (A2), X72.11
A3: DD2.12, DD25.33 (A3), DD28.14 (4A), DD40.7 (A3), DD41.7 (A3), X72.12
A4: DD2.13, DD25.34 (A4), DD29.2 (1A), DD40.6 (A4), DD41.6 (A4), X72.24
A5: DD25.35 (A5), DD29.5 (2A), DD40.5 (A5), DD41.5 (A5), X72.23
A6: DD25.36 (A6), DD29.11 (3A), DD40.4 (A6), DD41.4 (A6), X72.22
A7: DD25.37 (A7), DD28.3 (1B), DD40.3 (A7), DD41.3 (A7), X72.21
A8: DD25.38 (A8), DD28.6 (2B), DD40.25 (A8), DD41.25 (A8), VD1.1 (K), X71.26
A9: DD25.39 (A9), DD28.10 (3B), DD40.24 (A9), DD41.24 (A9), VD7.1 (K), X72.27
A10: DD25.40 (A10), DD28.13 (4B), DD40.21 (A10), DD41.21 (A10), VD5.1 (K), X71.27
A11: DD25.1 (A11), DD29.3 (1B), DD40.23 (A11), DD41.23 (A11), VD4.1 (K), X72.28
A12: DD25.2 (A12), DD29.6 (2B), DD40.2 (A12), DD41.2 (A12), VD3.1 (K), X72.2
A12*: VD3.2 (A), X5.6, X9.6
A13: DD11.13, DD25.3 (A13), DD29.10 (3B), DD40.20 (~CS), DD40.26 (A13), DD41.26 (A13), VD6.1 (K), X71.2
A14: DD23.11, DD25.4 (A14), DD29.14 (4A), VD2.1 (K), X72.1
A15: DD23.12, DD25.5 (A15), DD29.13 (4B), VD8.1 (K), X71.1
B: DD43.4 (1Y), DD49.1, R71.1 (L), VD10.2 (A)
BB: DD10.2 (Q0), R71.2 (R)
BG: DD10.6 (Q2), R73.2 (R)
BI: DD46.3 (D0), DD49.3, DD52.3 (1B), DD52.11 (3A)
BORD: DD20.6 (~Q), DD43.15 (~G)
BR: DD10.5 (Q1), R72.2 (R)
BT: DD46.9 (Q3), R102.1 (L)
CLK: DD21.6, DD25.6 (CLK), R59.2 (R)
COPY: DD1.6, DD6.17 (D6), R8.2 (R), X2.4
D0: DD6.2 (Q0), DD7.2 (Q0), DD8.2 (Q0), DD9.3 (D0), DD10.3 (D0), DD25.14 (D0), DD30.2 (DI), DD38.2 (Q0), DD40.11 (D0), DD41.11 (D0), R37.1 (L), X71.6
D1: DD6.5 (Q1), DD7.5 (Q1), DD8.5 (Q1), DD9.4 (D1), DD10.4 (D1), DD25.15 (D1), DD31.2 (DI), DD38.5 (Q1), DD40.12 (D1), DD41.12 (D1), R38.1 (L), X71.7
D2: DD6.6 (Q2), DD7.6 (Q2), DD8.6 (Q2), DD9.7 (D2), DD10.7 (D2), DD25.12 (D2), DD32.2 (DI), DD38.6 (Q2), DD40.13 (D2), DD41.13 (D2), R39.1 (L), X71.8
D3: DD6.9 (Q3), DD7.9 (Q3), DD8.9 (Q3), DD9.8 (D3), DD10.8 (D3), DD25.8 (D3), DD33.2 (DI), DD38.9 (Q3), DD40.15 (D3), DD41.15 (D3), R40.1 (L), X71.11
D4: DD6.12 (Q4), DD7.12 (Q4), DD8.12 (Q4), DD9.13 (D4), DD10.13 (D4), DD25.7 (D4), DD34.2 (DI), DD38.12 (Q4), DD40.16 (D4), DD41.16 (D4), R41.1 (L), X71.12
D5: DD6.15 (Q5), DD7.15 (Q5), DD8.15 (Q5), DD9.14 (D5), DD10.14 (D5), DD25.9 (D5), DD35.2 (DI), DD38.15 (Q5), DD40.17 (D5), DD41.17 (D5), R42.1 (L), X71.10
D6: DD6.16 (Q6), DD7.16 (Q6), DD8.16 (Q6), DD9.17 (D6), DD10.17 (D6), DD25.10 (D6), DD36.2 (DI), DD38.16 (Q6), DD40.18 (D6), DD41.18 (D6), R43.1 (L), X71.9
D7: DD6.19 (Q7), DD7.19 (Q7), DD8.19 (Q7), DD9.18 (D7), DD10.18 (D7), DD25.13 (D7), DD37.2 (DI), DD38.19 (Q7), DD40.19 (D7), DD41.19 (D7), R44.1 (L), X71.3
DC0: DD12.12 (D), DD13.3 (Q0), DD21.13, DD22.2, DD22.4
DC1: DD13.2 (Q1), DD21.11, DD22.5, DD28.15 (~G), DD29.15 (~G)
DC2: DD13.6 (Q2), DD21.9, DD39.1 (S)
FL: DD1.8, DD4.10, R2.2 (R)
G: DD43.9 (3Y), DD49.9, R73.1 (L), VD12.2 (A)
GI: DD47.3 (D0), DD49.8, DD51.4, DD51.5, DD52.6 (2B)
GND: *C59.2, C6.2, C12.2, C13.2, C17.2, C18.2, C20.2, C22.2, C23.2, C24.2, C57.2, C58.2, DD1.7 (GND), DD2.7 (GND), DD3.8 (GND), DD4.7 (GND), DD5.7 (GND), DD6.10 (GND), DD7.10 (GND), DD8.10 (GND), DD9.1 (~OE), DD9.10 (GND), DD10.1 (~OE), DD10.10 (GND), DD11.7 (GND), DD12.7 (GND), DD13.8 (GND), DD14.8 (GND), DD15.7 (GND), DD16.1 (D1), DD16.8 (GND), DD16.10 (D2), DD16.14 (R), DD16.15 (D0), DD17.1 (D1), DD17.8 (GND), DD17.10 (D2), DD17.14 (R), DD17.15 (D0), DD18.7 (GND), DD19.7 (GND), DD20.7 (GND), DD21.7 (GND), DD22.7 (GND), DD23.7 (GND), DD24.7 (GND), DD25.29 (GND), DD26.8 (GND), DD27.8 (GND), DD27.10 (3B), DD27.13 (4B), DD28.8 (GND), DD29.8 (GND), DD30.8 (GND), DD31.8 (GND), DD32.8 (GND), DD33.8 (GND), DD34.8 (GND), DD35.8 (GND), DD36.8 (GND), DD37.8 (GND), DD38.10 (GND), DD39.8 (GND), DD39.15 (~G), DD40.14 (GND), DD41.14 (GND), DD42.1 (~OE), DD42.10 (GND), DD43.8 (GND), DD44.10 (GND), DD45.8 (GND), DD46.1 (~OE), DD46.10 (GND), DD47.1 (~OE), DD47.10 (GND), DD49.7 (GND), DD50.7 (GND), DD51.7 (GND), DD52.8 (GND), DD53.7 (GND), R3.1 (L), R29.2 (R), R30.2 (R), R31.2 (R), R32.2 (R), R33.2 (R), R34.2 (R), R35.2 (R), R36.2 (R), R51.1 (L), R52.1 (L), R54.1 (L), R56.1 (L), R61.2 (R), R70.1 (L), R84.2 (R), R87.2 (R), R90.1 (L), R96.1 (L), R97.1 (L), R98.1 (L), R111.1 (L), R112.1 (L), R113.2 (R), R115.1 (L), R116.1 (L), R119.1 (L), R123.1 (L), X1.2, X1.6, X2.2, X2.6, X3.2, X3.6, X10.12, X11.2, X72.6, X72.7, X81.14, X81.16, X82.1, X82.2, X82.3, X82.4, X82.5, X82.6, X82.7, X82.8, X82.10, X82.15
GT: DD47.9 (Q3), R104.1 (L)
H0: DD13.7 (Q3), DD26.2 (1A)
H1: DD14.3 (Q0), DD19.3 (C), DD26.5 (2A)
H2: DD11.9, DD11.11, DD14.2 (Q1), DD26.11 (3A)
H3: DD14.6 (Q2), DD15.3 (C), DD15.11 (C), DD26.14 (4A)
H4: DD14.7 (Q3), DD15.2 (D), DD15.12 (D), DD19.2 (D), DD27.2 (1A)
HBL: DD19.4 (~S), DD19.6 (~Q), DD50.11
HBR: DD15.8 (~Q), DD15.10 (~S), DD23.2, R53.2 (R)
KEMP0: DD8.3 (D0), R29.1 (L), X6.3
KEMP1: DD8.4 (D1), R30.1 (L), X6.2
KEMP2: DD8.7 (D2), R31.1 (L), X6.1
KEMP3: DD8.8 (D3), R32.1 (L), X6.4
KEMP4: DD8.13 (D4), R33.1 (L), X6.5
KINV: DD5.3 (C), R12.1 (L), X9.10
KSPK: DD5.11 (C), R11.1 (L), X9.11
K_D0: DD6.3 (D0), R14.1 (L), X5.5, X10.2
K_D0*: DD7.3 (D0), R21.1 (L), X10.1
K_D1: DD6.4 (D1), R15.1 (L), X5.4, X10.4
K_D1*: DD7.4 (D1), R22.1 (L), X10.3
K_D2: DD6.7 (D2), R16.1 (L), X5.1, X10.5
K_D2*: DD7.7 (D2), R23.1 (L), X10.8
K_D3: DD6.8 (D3), R17.1 (L), X5.3, X10.6
K_D3*: DD7.8 (D3), R24.1 (L), X10.9
K_D4: DD6.13 (D4), R18.1 (L), X5.2, X10.7
K_D4*: DD7.13 (D4), R25.1 (L), X10.10
K_D5*: DD7.14 (D5), R26.1 (L), X10.11
MA0: DD26.4 (1Y), DD28.4 (1Y), DD30.13 (A6), DD31.13 (A6), DD32.13 (A6), DD33.13 (A6), DD34.13 (A6), DD35.13 (A6), DD36.13 (A6), DD37.13 (A6)
MA1: DD26.7 (2Y), DD28.7 (2Y), DD30.12 (A3), DD31.12 (A3), DD32.12 (A3), DD33.12 (A3), DD34.12 (A3), DD35.12 (A3), DD36.12 (A3), DD37.12 (A3)
MA2: DD26.9 (3Y), DD28.9 (3Y), DD30.11 (A4), DD31.11 (A4), DD32.11 (A4), DD33.11 (A4), DD34.11 (A4), DD35.11 (A4), DD36.11 (A4), DD37.11 (A4)
MA3: DD26.12 (4Y), DD28.12 (4Y), DD30.10 (A5), DD31.10 (A5), DD32.10 (A5), DD33.10 (A5), DD34.10 (A5), DD35.10 (A5), DD36.10 (A5), DD37.10 (A5)
MA4: DD27.4 (1Y), DD29.4 (1Y), DD30.5 (A0), DD31.5 (A0), DD32.5 (A0), DD33.5 (A0), DD34.5 (A0), DD35.5 (A0), DD36.5 (A0), DD37.5 (A0)
MA5: DD27.7 (2Y), DD29.7 (2Y), DD30.6 (A2), DD31.6 (A2), DD32.6 (A2), DD33.6 (A2), DD34.6 (A2), DD35.6 (A2), DD36.6 (A2), DD37.6 (A2)
MA6: DD27.9 (3Y), DD29.9 (3Y), DD30.7 (A1), DD31.7 (A1), DD32.7 (A1), DD33.7 (A1), DD34.7 (A1), DD35.7 (A1), DD36.7 (A1), DD37.7 (A1)
MA7: DD27.12 (4Y), DD29.12 (4Y), DD30.9 (A7), DD31.9 (A7), DD32.9 (A7), DD33.9 (A7), DD34.9 (A7), DD35.9 (A7), DD36.9 (A7), DD37.9 (A7)
MD0: DD30.14 (DO), DD38.3 (D0), DD42.3 (D0), DD44.7 (D0)
MD1: DD31.14 (DO), DD38.4 (D1), DD42.4 (D1), DD44.13 (D1)
MD2: DD32.14 (DO), DD38.7 (D2), DD42.7 (D2), DD44.6 (D2)
MD3: DD33.14 (DO), DD38.8 (D3), DD42.8 (D3), DD44.14 (D3)
MD4: DD34.14 (DO), DD38.13 (D4), DD42.13 (D4), DD44.5 (D4)
MD5: DD35.14 (DO), DD38.14 (D5), DD42.14 (D5), DD44.15 (D5)
MD6: DD36.14 (DO), DD38.17 (D6), DD42.17 (D6), DD44.4 (D6)
MD7: DD37.14 (DO), DD38.18 (D7), DD42.18 (D7), DD44.16 (D7)
MIC: C2.2, DD10.9 (Q3), R10.1 (L), X2.1
unnamed: C1.1, R1.2 (R)
unnamed: C1.2, DD1.9, DD1.10
unnamed: C3.1, R4.2 (R)
unnamed: C3.2, X1.3
unnamed: C7.2, DD24.12, R61.1 (L)
unnamed: C8.1, DD11.8
unnamed: C8.2, DD15.4 (~S), R52.2 (R), R53.1 (L)
unnamed: C9.1, DD13.14 (R), DD14.14 (R), R51.2 (R)
unnamed: C9.2, DD15.9 (Q)
unnamed: C10.1, R122.2 (R), VD26.2 (A)
unnamed: C10.2, DD18.1 (~R)
unnamed: C11.1, DD16.11 (~PE), DD17.11 (~PE)
unnamed: C11.2, DD18.8 (~Q), R54.2 (R), R55.2 (R)
unnamed: C12.1, DD20.2 (D), R58.1 (L)
unnamed: C13.1, R88.1 (L), VT9.2 (B)
unnamed: C14.1, R74.1 (L), R75.2 (R)
unnamed: C14.2, R74.2 (R), R81.1 (L), R82.1 (L), R83.2 (R)
unnamed: C15.1, DD53.12, R81.2 (R), VD23.2 (A)
unnamed: C15.2, DD53.10, R82.2 (R), VD24.2 (A), VD25.2 (A)
unnamed: C16.1, R85.2 (R)
unnamed: C16.2, R86.2 (R), R87.1 (L), R88.2 (R), R92.2 (R), R93.2 (R), R94.2 (R), R95.2 (R), R120.2 (R), VD19.2 (A), VD20.2 (A)
unnamed: C17.1, C19.1, L1.1, R109.1 (L), R110.2 (R)
unnamed: C18.1, R110.1 (L), R111.2 (R), VT6.2 (B)
unnamed: C19.2, C21.2, L1.2, VT6.3 (C)
unnamed: C20.1, C21.1, C25.2, R112.2 (R), VT6.1 (E)
unnamed: C22.1, R113.3, R114.2 (R)
unnamed: C23.1, R109.2 (R), R113.1 (L), R117.2 (R), R118.1 (L), VT8.3 (D)
unnamed: C24.1, R116.2 (R), VT7.1 (E), VT8.2 (S)
unnamed: C25.1, R114.1 (L), R115.2 (R), VT7.2 (B)
unnamed: C26.1, R89.2 (R), R90.2 (R), X3.1
unnamed: C26.2, R117.1 (L), VT7.3 (C)
unnamed: C57.1, R83.1 (L), R84.3
unnamed: DD1.1, R4.1 (L), R5.1 (L)
unnamed: DD1.2, R5.2 (R), R6.1 (L)
unnamed: DD1.3, R6.2 (R), R7.1 (L), R8.1 (L)
unnamed: DD1.4, DD1.5
unnamed: DD1.11, DD1.12
unnamed: DD1.13, R1.1 (L), R2.1 (L)
unnamed: DD2.6, DD2.9
unnamed: DD2.8, DD3.2 (IB), DD3.14 (IA)
unnamed: DD3.1 (EB), DD4.11
unnamed: DD4.2, DD4.6
unnamed: DD4.3, DD4.4, X81.1
unnamed: DD4.8, DD49.12
unnamed: DD4.9, DD42.19 (Q7)
unnamed: DD5.8 (~Q), DD5.12 (D)
unnamed: DD6.14 (D5), R19.1 (L)
unnamed: DD6.18 (D7), R20.1 (L)
unnamed: DD7.17 (D6), R27.1 (L)
unnamed: DD7.18 (D7), R28.1 (L)
unnamed: DD8.14 (D5), R34.1 (L)
unnamed: DD8.17 (D6), R35.1 (L)
unnamed: DD9.2 (Q0), X81.2
unnamed: DD9.5 (Q1), X81.3
unnamed: DD9.6 (Q2), X81.4
unnamed: DD9.9 (Q3), X81.5
unnamed: DD9.12 (Q4), X81.6
unnamed: DD9.15 (Q5), X81.7
unnamed: DD9.16 (Q6), X81.8
unnamed: DD9.19 (Q7), X81.9
unnamed: DD11.1, R50.1 (L), ZQ1.1
unnamed: DD11.2, DD11.3
unnamed: DD11.4, DD11.5, ZQ1.2
unnamed: DD11.6, DD12.3 (C), R50.2 (R)
unnamed: DD11.10, R122.1 (L), VD26.1 (K)
unnamed: DD11.12, DD41.20 (~CS)
unnamed: DD13.12 (P+), DD14.5 (+1)
unnamed: DD14.12 (P+), DD15.13 (~R)
unnamed: DD16.12 (P+), DD17.5 (+1)
unnamed: DD17.12 (P+), DD18.13 (~R)
unnamed: DD20.13 (~R), DD24.8
unnamed: DD22.6, DD22.9
unnamed: DD23.1, R58.2 (R)
unnamed: DD23.4, DD24.9
unnamed: DD23.10, DD24.2, DD24.5
unnamed: DD23.13, DD24.1
unnamed: DD24.3, DD24.4, R63.1 (L)
unnamed: DD24.6, R62.1 (L)
unnamed: DD24.11, R60.1 (L)
unnamed: DD42.2 (Q0), DD43.2 (1A)
unnamed: DD42.5 (Q1), DD43.5 (2A)
unnamed: DD42.6 (Q2), DD43.11 (3A)
unnamed: DD42.9 (Q3), DD43.3 (1B)
unnamed: DD42.12 (Q4), DD43.6 (2B)
unnamed: DD42.15 (Q5), DD43.10 (3B)
unnamed: DD42.16 (Q6), DD43.13 (4B), DD43.14 (4A)
unnamed: DD43.1 (S), DD49.11
unnamed: DD44.17 (Q7), DD45.4 (D1)
unnamed: DD45.2 (Q1), DD45.5 (D2)
unnamed: DD45.10 (Q3), DD45.13 (D4)
unnamed: DD45.7 (Q2), DD45.12 (D3)
unnamed: DD45.15 (Q4), DD49.13
unnamed: DD46.2 (Q0), DD46.4 (D1)
unnamed: DD46.5 (Q1), DD46.7 (D2)
unnamed: DD46.6 (Q2), DD46.8 (D3)
unnamed: DD46.12 (Q4), DD46.14 (D5)
unnamed: DD46.15 (Q5), DD46.17 (D6)
unnamed: DD46.16 (Q6), DD46.18 (D7)
unnamed: DD47.2 (Q0), DD47.4 (D1)
unnamed: DD47.5 (Q1), DD47.7 (D2)
unnamed: DD47.6 (Q2), DD47.8 (D3)
unnamed: DD47.12 (Q4), DD47.14 (D5)
unnamed: DD47.15 (Q5), DD47.17 (D6)
unnamed: DD47.16 (Q6), DD47.18 (D7)
unnamed: DD50.2, DD50.3, DD50.4
unnamed: DD51.8, DD52.15 (~G)
unnamed: DD51.9, DD51.10, DD51.11
unnamed: DD52.4 (1Y), R76.1 (L)
unnamed: DD52.7 (2Y), R77.1 (L)
unnamed: DD52.9 (3Y), R78.1 (L)
unnamed: DD52.12 (4Y), R79.1 (L)
unnamed: DD53.1, DD53.9, DD53.11
unnamed: DD53.2, DD53.6, VD23.1 (K)
unnamed: DD53.3, DD53.4, R85.1 (L), VD24.1 (K)
unnamed: DD53.5, DD53.8, DD53.13
unnamed: R7.2 (R), R9.1 (L), R10.3
unnamed: R45.2 (R), R46.1 (L), VT1.2 (B)
unnamed: R47.1 (L), VT1.3 (C), VT2.3 (C)
unnamed: R48.2 (R), VT2.2 (B)
unnamed: R49.1 (L), VT2.1 (E)
unnamed: R49.2 (R), X11.1
unnamed: R56.2 (R), R57.1 (L), VD9.2 (A)
unnamed: R89.1 (L), VT9.1 (E)
unnamed: R92.1 (L), VD21.2 (A)
unnamed: R96.2 (R), VT3.1 (E), X3.4
unnamed: R97.2 (R), VT4.1 (E), X3.3
unnamed: R98.2 (R), VT5.1 (E), X3.5
unnamed: R99.1 (L), VD15.1 (K), VD18.2 (A)
unnamed: R100.1 (L), VD14.1 (K), VD17.2 (A)
unnamed: R94.1 (L), R100.2 (R), R103.2 (R), R107.2 (R), VT4.2 (B)
unnamed: R101.1 (L), VD13.1 (K), VD16.2 (A)
unnamed: R95.1 (L), R101.2 (R), R102.2 (R), R106.2 (R), VT3.2 (B)
unnamed: R93.1 (L), R99.2 (R), R104.2 (R), R108.2 (R), VT5.2 (B)
unnamed: R105.2 (R), R106.1 (L), R107.1 (L), R108.1 (L), VD22.2 (A)
unnamed: R119.2 (R), R120.1 (L), VT8.1 (G)
unnamed: R75.1 (L), R76.2 (R), R77.2 (R), R78.2 (R), R79.2 (R), R80.2 (R), R123.2 (R)
unnamed: VD1.2 (A), X9.8
unnamed: VD2.2 (A), X9.7
unnamed: VD4.2 (A), X9.5
unnamed: VD5.2 (A), X9.4
unnamed: VD6.2 (A), X9.3
unnamed: VD7.2 (A), X9.2
unnamed: VD8.2 (A), X9.1
OSC: DD12.2 (D), DD12.6 (~Q), DD12.11 (C)
OUT: C2.1, R3.2 (R), X2.3
R: DD43.7 (2Y), DD49.5, R72.1 (L), VD11.2 (A)
RAS: DD12.8 (~Q), DD21.1, DD24.10
RI: DD46.13 (D4), DD49.6, DD51.1, DD51.2
RT: DD46.19 (Q7), R103.1 (L)
S0: *C59.1, DD21.4, DD21.5, DD26.1 (S), DD27.1 (S), DD28.1 (S), DD29.1 (S)
SCR: DD22.8, DD44.19 (S1)
SPK: DD10.12 (Q4), R10.2 (R), R48.1 (L), X2.5
UINV: DD5.5 (Q), DD49.2, DD49.4, DD49.10, DD50.9, VD22.1 (K)
USPK: DD5.9 (Q), R45.1 (L)
V0: DD16.3 (Q0), DD39.2 (1A), DD52.1 (S), R80.1 (L)
V0V6: DD26.6 (2B), DD39.4 (1Y)
V1: DD16.2 (Q1), DD39.5 (2A)
V1V7: DD26.10 (3B), DD39.7 (2Y)
V2: DD16.6 (Q2), DD22.12
V3: DD16.7 (Q3), DD19.11 (C), DD27.5 (2A)
V4: DD17.3 (Q0), DD19.12 (D), DD27.11 (3A)
V5: DD17.2 (Q1), DD26.3 (1B)
V6: DD17.6 (Q2), DD18.3 (C), DD18.11 (C), DD39.3 (1B), DD39.11 (3A)
V7: DD17.7 (Q3), DD18.2 (D), DD18.12 (D), DD39.6 (2B), DD39.14 (4A)
V20: DD22.11, DD26.13 (4B)
V61: DD27.3 (1B), DD39.9 (3Y)
V71: DD27.6 (2B), DD39.12 (4Y)
VBL: DD19.8 (~Q), DD19.10 (~S), DD50.12, DD51.12
VBR: DD18.9 (Q), DD23.3, R57.2 (R), VD9.1 (K)
VSYN: C7.1, DD18.5 (Q)
WRBUF: DD22.3, DD38.11 (C)
Y: DD43.12 (4Y), DD47.13 (D4), R70.2 (R)
Y0: DD50.1, VD16.1 (K), VD17.1 (K), VD18.1 (K)
Y1: DD50.10, R121.1 (L), VD13.2 (A), VD14.2 (A), VD15.2 (A)
YT: DD47.19 (Q7), DD50.6, DD50.8
~BL: DD50.13, VD10.1 (K), VD11.1 (K), VD12.1 (K), VD21.1 (K)
~BUSRQ: DD25.25 (~BREQ), R69.1 (L), X72.19
~BUSY: DD25.23 (~BUSY), X72.26
~CAS: DD21.12, DD30.15 (~CS), DD31.15 (~CS), DD32.15 (~CS), DD33.15 (~CS), DD34.15 (~CS), DD35.15 (~CS), DD36.15 (~CS), DD37.15 (~CS)
~DC1: DD20.10 (~S), DD21.10, DD22.1, DD26.15 (~G), DD27.15 (~G)
~DC2: DD20.3 (C), DD21.8, DD22.10, DD22.13, DD42.11 (C)
~GI: DD51.6, DD52.5 (2A)
~HALT: DD25.18 (~HALT), X71.15
~HBL: DD19.5 (Q)
~HSYN: DD15.5 (Q), DD16.5 (+1), DD19.1 (~R), VD19.1 (K), VD25.1 (K)
~INT: DD25.16 (~INT), R60.2 (R), X71.13
~IORQE: DD2.5, R65.2 (R), X72.13
~IORQI: R66.2 (R), X71.17
~IORQ: DD25.20 (~IORQ), R65.1 (L), R66.1 (L), X71.28
~M1: DD25.27 (~M1), X71.24
~MREQE: DD23.6, DD23.8, R64.2 (R), X71.22
~MREQ: DD25.19 (~MREQ), R64.1 (L), X71.16
~NMI: DD25.17 (~NMI), R68.1 (L), X71.14
~OSC: DD12.5 (Q), DD13.5 (+1), DD44.12 (C), DD45.9 (C), DD46.11 (C), DD47.11 (C)
~PDKEY: DD3.9 (0A), DD7.1 (~OE)
~PKEM: DD3.12 (3A), DD8.1 (~OE)
~PKEY: DD3.11 (2A), DD6.1 (~OE)
~POUT: DD3.5 (2B), DD10.11 (C)
~RAS: DD21.2, DD21.3, DD30.4 (~RS), DD31.4 (~RS), DD32.4 (~RS), DD33.4 (~RS), DD34.4 (~RS), DD35.4 (~RS), DD36.4 (~RS), DD37.4 (~RS)
~RDRAM: DD38.1 (~OE), R62.2 (R), X71.4
~RDROM: DD40.22 (~OE), DD41.22 (~OE), R63.2 (R), X72.25
~RDY: DD8.18 (D7), R36.1 (L), X81.11
~RD: DD3.15 (EA), DD23.9, DD25.21 (~RD), X71.18
~RES: C6.1, DD25.26 (~RES), R13.1 (L), X9.12, X72.20
~RFSH: DD25.28 (~RFSH), X71.25
~RI: DD51.3, DD52.2 (1A), DD52.10 (3B)
~UINV: DD5.2 (D), DD5.6 (~Q), DD50.5
~VBL: DD19.9 (Q)
~VSYN: DD18.6 (~Q), DD19.13 (~R), VD20.1 (K)
~WAIT: DD25.24 (~WAIT), R67.1 (L), X71.21
~WERAM: DD20.9 (Q), DD30.3 (~WR), DD31.3 (~WR), DD32.3 (~WR), DD33.3 (~WR), DD34.3 (~WR), DD35.3 (~WR), DD36.3 (~WR), DD37.3 (~WR)
~WR00: DD3.7 (0B), DD4.5
~WR01: DD3.6 (1B), DD4.1, DD9.11 (C)
~WR: DD4.12, DD23.5, DD25.22 (~WR), X71.19

Notes on the sheet:
UncleRus
