UncleRus/quorum-reborn/kicad/Magic-05/keyboard.kicad_sch

## KiCad design kicad/Magic-05/keyboard.kicad_sch (2023-06-19)

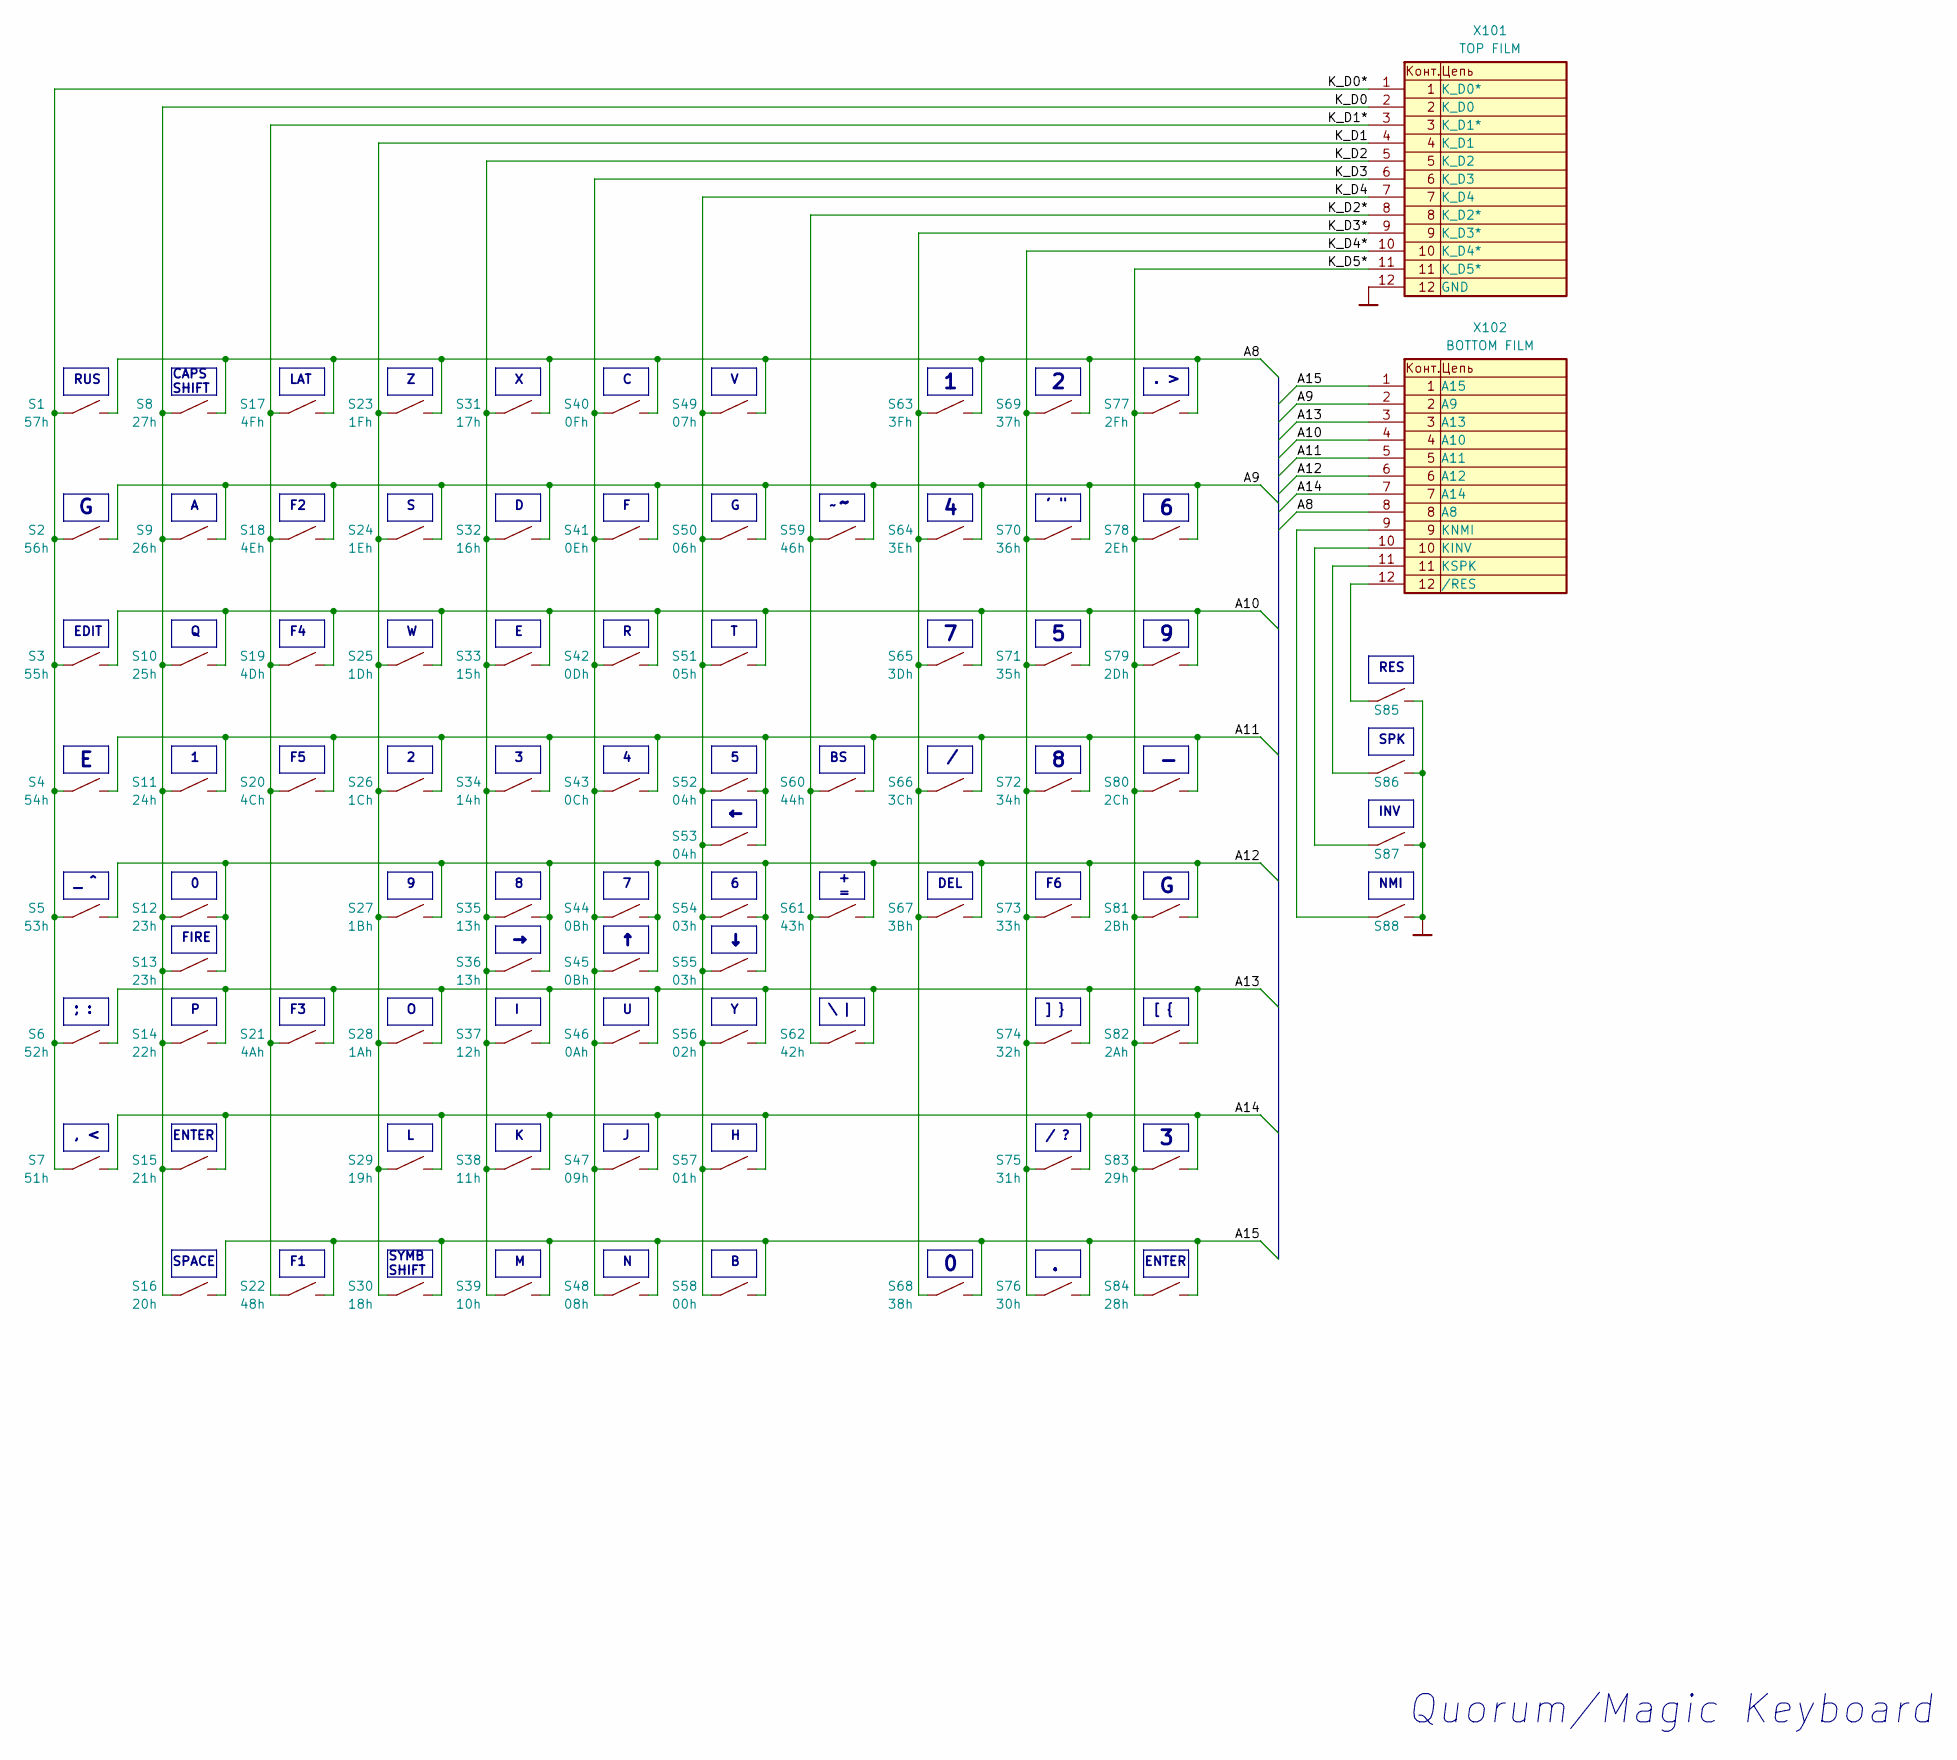
[picture p50: schematic keyboard.kicad_sch]

Parts:
S1: 57h
S2: 56h
S3: 55h
S4: 54h
S5: 53h
S6: 52h
S7: 51h
S8: 27h
S9: 26h
S10: 25h
S11: 24h
S12, S13: 23h
S14: 22h
S15: 21h
S16: 20h
S17: 4Fh
S18: 4Eh
S19: 4Dh
S20: 4Ch
S21: 4Ah
S22: 48h
S23: 1Fh
S24: 1Eh
S25: 1Dh
S26: 1Ch
S27: 1Bh
S28: 1Ah
S29: 19h
S30: 18h
S31: 17h
S32: 16h
S33: 15h
S34: 14h
S35, S36: 13h
S37: 12h
S38: 11h
S39: 10h
S40: 0Fh
S41: 0Eh
S42: 0Dh
S43: 0Ch
S44, S45: 0Bh
S46: 0Ah
S47: 09h
S48: 08h
S49: 07h
S50: 06h
S51: 05h
S52, S53: 04h
S54, S55: 03h
S56: 02h
S57: 01h
S58: 00h
S59: 46h
S60: 44h
S61: 43h
S62: 42h
S63: 3Fh
S64: 3Eh
S65: 3Dh
S66: 3Ch
S67: 3Bh
S68: 38h
S69: 37h
S70: 36h
S71: 35h
S72: 34h
S73: 33h
S74: 32h
S75: 31h
S76: 30h
S77: 2Fh
S78: 2Eh
S79: 2Dh
S80: 2Ch
S81: 2Bh
S82: 2Ah
S83: 29h
S84: 28h
S85: RES
S86: SPK
S87: INV
S88: NMI
X101: TOP FILM
X102: BOTTOM FILM

Connections:
A8: S1.2 (R), S8.2 (R), S17.2 (R), S23.2 (R), S31.2 (R), S40.2 (R), S49.2 (R), S63.2 (R), S69.2 (R), S77.2 (R), X102.8
A9: S2.2 (R), S9.2 (R), S18.2 (R), S24.2 (R), S32.2 (R), S41.2 (R), S50.2 (R), S59.2 (R), S64.2 (R), S70.2 (R), S78.2 (R), X102.2
A10: S3.2 (R), S10.2 (R), S19.2 (R), S25.2 (R), S33.2 (R), S42.2 (R), S51.2 (R), S65.2 (R), S71.2 (R), S79.2 (R), X102.4
A11: S4.2 (R), S11.2 (R), S20.2 (R), S26.2 (R), S34.2 (R), S43.2 (R), S52.2 (R), S53.2 (R), S60.2 (R), S66.2 (R), S72.2 (R), S80.2 (R), X102.5
A12: S5.2 (R), S12.2 (R), S13.2 (R), S27.2 (R), S35.2 (R), S36.2 (R), S44.2 (R), S45.2 (R), S54.2 (R), S55.2 (R), S61.2 (R), S67.2 (R), S73.2 (R), S81.2 (R), X102.6
A13: S6.2 (R), S14.2 (R), S21.2 (R), S28.2 (R), S37.2 (R), S46.2 (R), S56.2 (R), S62.2 (R), S74.2 (R), S82.2 (R), X102.3
A14: S7.2 (R), S15.2 (R), S29.2 (R), S38.2 (R), S47.2 (R), S57.2 (R), S75.2 (R), S83.2 (R), X102.7
A15: S16.2 (R), S22.2 (R), S30.2 (R), S39.2 (R), S48.2 (R), S58.2 (R), S68.2 (R), S76.2 (R), S84.2 (R), X102.1
GND: S85.2 (R), S86.2 (R), S87.2 (R), S88.2 (R), X101.12
K_D0: S8.1 (L), S9.1 (L), S10.1 (L), S11.1 (L), S12.1 (L), S13.1 (L), S14.1 (L), S15.1 (L), S16.1 (L), X101.2
K_D0*: S1.1 (L), S2.1 (L), S3.1 (L), S4.1 (L), S5.1 (L), S6.1 (L), S7.1 (L), X101.1
K_D1: S23.1 (L), S24.1 (L), S25.1 (L), S26.1 (L), S27.1 (L), S28.1 (L), S29.1 (L), S30.1 (L), X101.4
K_D1*: S17.1 (L), S18.1 (L), S19.1 (L), S20.1 (L), S21.1 (L), S22.1 (L), X101.3
K_D2: S31.1 (L), S32.1 (L), S33.1 (L), S34.1 (L), S35.1 (L), S36.1 (L), S37.1 (L), S38.1 (L), S39.1 (L), X101.5
K_D2*: S59.1 (L), S60.1 (L), S61.1 (L), S62.1 (L), X101.8
K_D3: S40.1 (L), S41.1 (L), S42.1 (L), S43.1 (L), S44.1 (L), S45.1 (L), S46.1 (L), S47.1 (L), S48.1 (L), X101.6
K_D3*: S63.1 (L), S64.1 (L), S65.1 (L), S66.1 (L), S67.1 (L), S68.1 (L), X101.9
K_D4: S49.1 (L), S50.1 (L), S51.1 (L), S52.1 (L), S53.1 (L), S54.1 (L), S55.1 (L), S56.1 (L), S57.1 (L), S58.1 (L), X101.7
K_D4*: S69.1 (L), S70.1 (L), S71.1 (L), S72.1 (L), S73.1 (L), S74.1 (L), S75.1 (L), S76.1 (L), X101.10
K_D5*: S77.1 (L), S78.1 (L), S79.1 (L), S80.1 (L), S81.1 (L), S82.1 (L), S83.1 (L), S84.1 (L), X101.11
unnamed: S85.1 (L), X102.12
unnamed: S86.1 (L), X102.11
unnamed: S87.1 (L), X102.10
unnamed: S88.1 (L), X102.9

Notes on the sheet:
DEL
' "
INV
NMI
/ ?
SPACE
SPK
. >
+ =
[ {
; :
SYMB SHIFT
EDIT
Quorum/Magic Keyboard
\ |
_ ^
ENTER
, <
RUS
] }
CAPS SHIFT
RES
LAT
FIRE
