UncleRus/quorum-reborn/kicad/Quorum-128/Quorum-128.kicad_sch

## KiCad design kicad/Quorum-128/Quorum-128.kicad_sch (2023-06-19)

Schematic: Quorum-128.kicad_sch

Parts:
A1: TV MODULATOR
C1, C6, C9, C15: 0,1; C_Rect_L7.0mm_W2.5mm_P5.00mm
C2: 5,0; CP_Radial_D7.5mm_P2.50mm
C3: 20,0; CP_Radial_D7.5mm_P2.50mm
C4: 1,0; CP_Radial_D7.5mm_P2.50mm
C5, C7, C8: 0,01; C_Rect_L7.0mm_W2.5mm_P5.00mm
C10, C14: 100; C_Rect_L7.0mm_W2.5mm_P5.00mm
C11: 27..56; C_Rect_L7.0mm_W2.5mm_P5.00mm
C12: 43; C_Rect_L7.0mm_W2.5mm_P5.00mm
C13: 1000; C_Rect_L7.0mm_W2.5mm_P5.00mm
DD1, DD6, DD15: К555ЛН1; DIP-14_W7.62mm_Socket_LongPads
DD2, DD5, DD22: К555ТМ2; DIP-14_W7.62mm_Socket_LongPads
DD3: К555ЛЛ1; DIP-14_W7.62mm_Socket_LongPads
DD4, DD24: К555ЛА3; DIP-14_W7.62mm_Socket_LongPads
DD7, DD14: К555ЛЛ1
DD8, DD9, DD10, DD21: К555ИР22; DIP-20_W7.62mm_Socket_LongPads
DD11: К554СА3
DD12: КБ01ВГ1-2
DD13: К555ИД4; DIP-16_W7.62mm_Socket_LongPads
DD16: CODER SECAM
DD17: Z80; DIP-40_W15.24mm_Socket_LongPads
DD18: К555АП6; DIP-20_W7.62mm_Socket_LongPads
DD19, DD20: W27C512; DIP-28_W15.24mm_Socket_LongPads
DD23: КР531ГГ1
DD25, DD26, DD27, DD28, DD29, DD30, DD31, DD32, DD33, DD34, DD35, DD36, DD37, DD38, DD39, DD40: К565РУ5; DIP-16_W7.62mm_Socket_LongPads
DD41: К555ТМ8; DIP-16_W7.62mm_Socket_LongPads
FU1: FUSE
L1: DM-0,3-40
R1, R2, R5, R63, R102, R103: 360; R_Axial_DIN0204_L3.6mm_D1.6mm_P7.62mm_Horizontal
R3, R7, R10, R11, R12, R13, R14, R30, R31, R32, R33, R34, R36, R37, R39, R40, R41, R42, R60, R62, R66, R68, R74, R79, R84, R85, R88, R90, R94, R101, R104: 1k; R_Axial_DIN0204_L3.6mm_D1.6mm_P7.62mm_Horizontal
R4: 2M; R_Axial_DIN0204_L3.6mm_D1.6mm_P7.62mm_Horizontal
R6, R28, R75: 680; R_Axial_DIN0204_L3.6mm_D1.6mm_P7.62mm_Horizontal
R8, R27: 22k; R_Axial_DIN0204_L3.6mm_D1.6mm_P7.62mm_Horizontal
R9, R59: 2k2; R_Axial_DIN0204_L3.6mm_D1.6mm_P7.62mm_Horizontal
R15, R65, R82: 3k6; R_Axial_DIN0204_L3.6mm_D1.6mm_P7.62mm_Horizontal
R16, R17, R18, R19, R20, R21, R22, R23, R24, R25, R26, R43, R44, R45, R46, R47, R48, R49, R50, R61, R99: 10k; R_Axial_DIN0204_L3.6mm_D1.6mm_P7.62mm_Horizontal
R29, R76, R80, R93: 47k; R_Axial_DIN0204_L3.6mm_D1.6mm_P7.62mm_Horizontal
R35, R69, R70, R71, R72, R92: 100; R_Axial_DIN0204_L3.6mm_D1.6mm_P7.62mm_Horizontal
R38: 4k7; R_Axial_DIN0204_L3.6mm_D1.6mm_P7.62mm_Horizontal
R51, R52, R53, R54, R55, R56, R57, R58: 430; R_Axial_DIN0204_L3.6mm_D1.6mm_P7.62mm_Horizontal
R64: 33; R_Axial_DIN0204_L3.6mm_D1.6mm_P7.62mm_Horizontal
R67: 2k7*; R_Axial_DIN0204_L3.6mm_D1.6mm_P7.62mm_Horizontal
R73: 510; R_Axial_DIN0204_L3.6mm_D1.6mm_P7.62mm_Horizontal
R77, R78: 5k1; R_Axial_DIN0204_L3.6mm_D1.6mm_P7.62mm_Horizontal
R81: 22k
R83: 4k7
R86: 820; R_Axial_DIN0204_L3.6mm_D1.6mm_P7.62mm_Horizontal
R87: 4k3; R_Axial_DIN0204_L3.6mm_D1.6mm_P7.62mm_Horizontal
R89: 2k; R_Axial_DIN0204_L3.6mm_D1.6mm_P7.62mm_Horizontal
R91: 100
R95: 1k*; R_Axial_DIN0204_L3.6mm_D1.6mm_P7.62mm_Horizontal
R96, R97, R98: 47; R_Axial_DIN0204_L3.6mm_D1.6mm_P7.62mm_Horizontal
R100: 100k; R_Axial_DIN0204_L3.6mm_D1.6mm_P7.62mm_Horizontal
TP1, TP2, TP3, TP4, TP5, TP6, TP7, TP8, TP9, TP10, TP11, TP12, TP13, TP14, TP15, TP16, TP20, TP22, TP23: TestPoint
VD1, VD2, VD3, VD4, VD5, VD6, VD7, VD8, VD12: D; D_DO-35_SOD27_P7.62mm_Horizontal
VD9, VD11, VD13, VD14, VD15, VD16, VD17: КД522; D_DO-35_SOD27_P7.62mm_Horizontal
VD10: КС139
VT1: KT3107; TO-92_Inline_Wide
VT2, VT3, VT4, VT5, VT6, VT7, VT8, VT9: KT3102; TO-92_Inline_Wide
X1: KEMPSTON; DIN5-RA-PTH
X2: SINCLAIR; DIN5-RA-PTH
X3: KEYBOARD 1; PinHeader_1x12_P2.54mm_Vertical
X4: KEYBOARD 2; PinHeader_1x12_P2.54mm_Vertical
X5: RESET; PinHeader_1x02_P2.54mm_Vertical
X6: TAPE IN; DIN5-RA-PTH
X8: RGB OUT; DIN5-RA-PTH
X9: CENTRONICS
X10: SPEAKER; PinHeader_1x02_P2.54mm_Vertical
X11: TAPE OUT; DIN5-RA-PTH
X12_1: EXPANSION BOTTOM
X12_2: EXPANSION TOP
X13: TV; DIN5-RA-PTH
XJ2: 16/8 MHz
ZQ1: 16(8) MHz; Crystal_HC49-U_Horizontal_1EP_style2

Connections:
+5V: A1.2.6 (VCC), C15.2, DD1.14 (VCC), DD2.1 (~R), DD2.4 (~S), DD2.14 (VCC), DD3.14 (VCC), DD4.14 (VCC), DD5.1 (~R), DD5.13 (~R), DD5.14 (VCC), DD6.14 (VCC), DD7.14 (VCC), DD8.11 (C), DD8.20 (VCC), DD9.11 (C), DD9.17 (D6), DD9.18 (D7), DD9.20 (VCC), DD10.11 (C), DD10.14 (D5), DD10.18 (D7), DD10.20 (VCC), DD11.11 (+U), DD12.24 (VCC), DD13.16 (VCC), DD14.14 (VCC), DD15.14 (VCC), DD16.28 (VCC), DD17.11 (VCC), DD18.20 (VCC), DD19.28 (VCC), DD20.28 (VCC), DD21.20 (VCC), DD22.2 (D), DD22.3 (C), DD22.10 (~S), DD22.14 (VCC), DD24.14 (VCC), DD25.16 (VCC), DD26.16 (VCC), DD27.16 (VCC), DD28.16 (VCC), DD29.16 (VCC), DD30.16 (VCC), DD31.16 (VCC), DD32.16 (VCC), DD33.16 (VCC), DD34.16 (VCC), DD35.16 (VCC), DD36.16 (VCC), DD37.16 (VCC), DD38.16 (VCC), DD39.16 (VCC), DD40.16 (VCC), DD41.16 (VCC), L1.1, R4.1 (L), R5.1 (L), R8.1 (L), R16.2 (R), R17.2 (R), R18.2 (R), R19.2 (R), R20.2 (R), R21.2 (R), R22.2 (R), R23.2 (R), R24.2 (R), R25.2 (R), R26.2 (R), R27.2 (R), R30.2 (R), R36.1 (L), R38.1 (L), R39.2 (R), R42.2 (R), R43.2 (R), R44.2 (R), R45.2 (R), R46.2 (R), R47.2 (R), R48.2 (R), R49.2 (R), R50.2 (R), R60.2 (R), R67.2 (R), R68.2 (R), R72.1 (L), R85.2 (R), R86.1 (L), R94.1 (L), R101.2 (R), R104.2 (R), TP6.1, VD16.1 (K), VT1.1 (E), VT3.3 (C), VT4.3 (C), VT5.3 (C), VT6.3 (C), VT7.3 (C), VT8.3 (C), VT9.3 (C), X1.6, X12_1.3, X13.5, XJ2.1
A0: DD12.7 (A0), DD14.1, DD17.30 (A0), DD19.10 (A0), DD20.10 (A0), X12_1.9
A1: DD7.5, DD12.15 (A1), DD17.31 (A1), DD19.9 (A1), DD20.9 (A1), X12_1.10
A2: DD12.17 (A2), DD17.32 (A2), DD19.8 (A2), DD20.8 (A2), X12_1.11
A3: DD12.11 (A3), DD13.13 (A0), DD17.33 (A3), DD19.7 (A3), DD20.7 (A3), X12_1.12
A4: DD12.9 (A4), DD13.3 (A1), DD17.34 (A4), DD19.6 (A4), DD20.6 (A4), X12_1.24
A5: DD12.23 (A5), DD17.35 (A5), DD19.5 (A5), DD20.5 (A5), X12_1.23
A6: DD12.63 (A6), DD17.36 (A6), DD19.4 (A6), DD20.4 (A6), X12_1.22
A7: DD12.1 (A7), DD14.2, DD17.37 (A7), DD19.3 (A7), DD20.3 (A7), X12_1.21
A8: DD12.20 (A8), DD17.38 (A8), DD19.25 (A8), DD20.25 (A8), VD8.1 (K), X12_2.26
A9: DD12.22 (A9), DD17.39 (A9), DD19.24 (A9), DD20.24 (A9), VD2.1 (K), X12_1.27
A10: DD7.2, DD17.40 (A10), DD19.21 (A10), DD20.21 (A10), VD4.1 (K), X12_2.27
A11: DD12.21 (A11), DD17.1 (A11), DD19.23 (A11), DD20.23 (A11), VD5.1 (K), X12_1.28
A12: DD12.3 (A12), DD17.2 (A12), DD19.2 (A12), DD20.2 (A12), VD6.1 (K), X12_1.2
A12*: VD6.2 (A), X2.6, X4.6
A13: DD12.18 (A13), DD17.3 (A13), DD20.26 (A13), TP4.1, TP12.1, VD3.1 (K), X12_2.2
A14: DD3.1, DD12.64 (A14), DD17.4 (A14), VD7.1 (K), X12_1.1
A15: DD3.2, DD12.2 (A15), DD17.5 (A15), VD1.1 (K), X12_2.1
B: DD12.37 (B), DD16.7 (BI)
BD0: DD8.2 (Q0), DD9.2 (Q0), DD10.2 (Q0), DD18.2 (A0), DD19.11 (D0), DD20.11 (D0), R43.1 (L), X12_2.6
BD1: DD8.5 (Q1), DD9.5 (Q1), DD10.5 (Q1), DD18.3 (A1), DD19.12 (D1), DD20.12 (D1), R44.1 (L), X12_2.7
BD2: DD8.6 (Q2), DD9.6 (Q2), DD10.6 (Q2), DD18.4 (A2), DD19.13 (D2), DD20.13 (D2), R45.1 (L), X12_2.8
BD3: DD8.9 (Q3), DD9.9 (Q3), DD10.9 (Q3), DD18.5 (A3), DD19.15 (D3), DD20.15 (D3), R46.1 (L), X12_2.11
BD4: DD8.12 (Q4), DD9.12 (Q4), DD10.12 (Q4), DD18.6 (A4), DD19.16 (D4), DD20.16 (D4), R47.1 (L), X12_2.12
BD5: DD8.15 (Q5), DD9.15 (Q5), DD10.15 (Q5), DD18.7 (A5), DD19.17 (D5), DD20.17 (D5), R48.1 (L), X12_2.10
BD6: DD8.16 (Q6), DD9.16 (Q6), DD10.16 (Q6), DD18.8 (A6), DD19.18 (D6), DD20.18 (D6), R49.1 (L), X12_2.9
BD7: DD8.19 (Q7), DD9.19 (Q7), DD10.19 (Q7), DD18.9 (A7), DD19.19 (D7), DD20.19 (D7), R50.1 (L), X12_2.3
BUSY: DD8.18 (D7), R15.1 (L), X9.11
CGND: FU1.2 (R), X6.2, X6.6, X11.2, X11.6
CLK: DD6.13, DD12.56 (CLK4), DD17.6 (CLK)
CLK8: DD12.55 (CLK), DD16.3 (CLK), TP2.1
COPY: DD10.17 (D6), DD11.9 (OK), R61.1 (L), R100.2 (R), R101.1 (L)
D0: DD17.14 (D0), DD18.18 (B0), DD21.3 (D0), DD41.4 (D1), R51.2 (R)
D1: DD17.15 (D1), DD18.17 (B1), DD21.4 (D1), R52.2 (R)
D2: DD17.12 (D2), DD18.16 (B2), DD21.7 (D2), DD41.5 (D2), R53.2 (R)
D3: DD17.8 (D3), DD18.15 (B3), DD21.8 (D3), R54.2 (R)
D4: DD17.7 (D4), DD18.14 (B4), DD21.13 (D4), R55.2 (R)
D5: DD17.9 (D5), DD18.13 (B5), DD21.14 (D5), DD41.12 (D3), R56.2 (R)
D6: DD17.10 (D6), DD18.12 (B6), DD21.17 (D6), DD41.13 (D4), R57.2 (R)
D7: DD17.13 (D7), DD18.11 (B7), DD21.18 (D7), R58.2 (R)
DIR: DD4.3, DD18.1 (T)
G: DD12.36 (G), DD16.23 (GI)
GND: A1.1.2 (GND), A1.1.3 (GND), A1.1.5 (GND), A1.2.1 (GND), A1.2.2 (GND), A1.2.5 (GND), C2.2, C3.2, C5.1, C6.1, C7.1, C8.1, C9.1, C10.1, C15.1, DD1.7 (GND), DD2.7 (GND), DD3.7 (GND), DD4.7 (GND), DD5.7 (GND), DD6.7 (GND), DD7.7 (GND), DD8.10 (GND), DD8.14 (D5), DD8.17 (D6), DD9.10 (GND), DD10.10 (GND), DD11.2 (OE), DD11.6 (-U), DD12.54 (GND), DD13.8 (GND), DD14.7 (GND), DD15.7 (GND), DD16.14 (GND), DD16.21 (TS1), DD17.29 (GND), DD18.10 (GND), DD19.14 (GND), DD20.14 (GND), DD21.1 (~OE), DD21.10 (GND), DD22.7 (GND), DD23.8 (GND1), DD23.9 (GND2), DD24.7 (GND), DD25.8 (GND), DD26.8 (GND), DD27.8 (GND), DD28.8 (GND), DD29.8 (GND), DD30.8 (GND), DD31.8 (GND), DD32.8 (GND), DD33.8 (GND), DD34.8 (GND), DD35.8 (GND), DD36.8 (GND), DD37.8 (GND), DD38.8 (GND), DD39.8 (GND), DD40.8 (GND), DD41.8 (GND), FU1.1 (L), R6.2 (R), R10.2 (R), R11.2 (R), R12.2 (R), R13.2 (R), R14.2 (R), R15.2 (R), R29.1 (L), R31.1 (L), R34.1 (L), R35.1 (L), R66.2 (R), R69.1 (L), R70.1 (L), R71.1 (L), R73.1 (L), R78.1 (L), R83.1 (L), R90.2 (R), R91.2 (R), R92.1 (L), R93.1 (L), R95.1 (L), R100.1 (L), R102.2 (R), R103.1 (L), TP9.1, VD10.2 (A), VD17.2 (A), X3.12, X5.2, X8.2, X8.6, X9.18, X9.19, X9.20, X9.21, X9.22, X9.23, X9.24, X9.25, X10.2, X12_1.6, X12_1.7, X12_1.14, X13.2
KEMP0: DD8.3 (D0), R14.1 (L), X1.3
KEMP1: DD8.4 (D1), R13.1 (L), X1.2
KEMP2: DD8.7 (D2), R12.1 (L), X1.1
KEMP3: DD8.8 (D3), R11.1 (L), X1.4
KEMP4: DD8.13 (D4), R10.1 (L), X1.5
KNMI: C1.2, R4.2 (R), X4.9
KRES: C2.1, DD6.3, R8.2 (R)
KSPK: DD22.11 (C), R27.1 (L), X4.10, X4.11
K_D0: DD10.3 (D0), R22.1 (L), X2.5, X3.2
K_D0*: DD9.3 (D0), R16.1 (L), X3.1
K_D1: DD10.4 (D1), R23.1 (L), X2.4, X3.4
K_D1*: DD9.4 (D1), R17.1 (L), X3.3
K_D2: DD10.7 (D2), R24.1 (L), X2.1, X3.5
K_D2*: DD9.7 (D2), R18.1 (L), X3.8
K_D3: DD10.8 (D3), R25.1 (L), X2.3, X3.6
K_D3*: DD9.8 (D3), R19.1 (L), X3.9
K_D4: DD10.13 (D4), R26.1 (L), X2.2, X3.7
K_D4*: DD9.13 (D4), R20.1 (L), X3.10
K_D5*: DD9.14 (D5), R21.1 (L), X3.11
unnamed: A1.1.1 (VIDEO), R91.3, X13.1
unnamed: A1.2.4 (RF_OUT), X13.3
unnamed: C1.1, DD5.2 (D), R5.2 (R), R6.1 (L)
unnamed: C3.1, DD6.11, R9.2 (R)
unnamed: C4.1, R28.1 (L), VD16.2 (A), VD17.1 (K)
unnamed: C4.2, R29.2 (R), X6.3, X6.5
unnamed: C5.2, DD11.4 (W-), R28.2 (R), R99.2 (R)
unnamed: C6.2, R30.1 (L), R31.2 (R), R32.1 (L), R99.1 (L)
unnamed: C7.2, DD24.12, R39.1 (L), VD9.2 (A)
unnamed: C8.2, R65.2 (R), R66.1 (L), X11.3, X11.5
unnamed: C9.2, R72.2 (R), R77.2 (R), R79.2 (R), VD10.1 (K)
unnamed: C10.2, R74.2 (R), R76.1 (L)
unnamed: C11.1, R75.2 (R)
unnamed: C11.2, DD23.2 (UF), R76.2 (R), R77.1 (L), R78.2 (R)
unnamed: C12.1, DD23.5 (C2)
unnamed: C12.2, DD23.4 (C1)
unnamed: C13.1, DD15.11, R38.2 (R), R93.2 (R)
unnamed: C13.2, DD3.12, DD4.8
unnamed: C14.1, R86.2 (R), R87.2 (R), R88.2 (R), R89.2 (R), R90.1 (L), VD11.2 (A), VT7.2 (B)
unnamed: C14.2, R84.1 (L), R103.2 (R)
unnamed: DD1.1, R1.1 (L), ZQ1.1
unnamed: DD1.2, DD1.3, R1.2 (R), R2.1 (L)
unnamed: DD1.4, DD1.5, R2.2 (R), ZQ1.2
unnamed: DD1.6, DD2.3 (C), TP3.1
unnamed: DD1.8, DD20.22 (~OE)
unnamed: DD1.9, DD19.22 (~OE), TP14.1
unnamed: DD1.10, DD21.11 (C)
unnamed: DD1.13, DD4.6
unnamed: DD2.2 (D), DD2.6 (~Q)
unnamed: DD2.5 (Q), TP1.1
unnamed: DD3.3, DD3.4
unnamed: DD3.8, DD4.1, R3.1 (L)
unnamed: DD3.11, DD4.2
unnamed: DD4.5, DD5.9 (Q)
unnamed: DD4.9, DD4.10, DD4.11
unnamed: DD5.11 (C), DD6.2
unnamed: DD5.5 (Q), DD5.12 (D), R7.1 (L)
unnamed: DD6.4, DD6.5, R9.1 (L)
unnamed: DD6.8, DD7.1
unnamed: DD11.3 (W+), R32.2 (R)
unnamed: DD12.45 (~INT), R40.1 (L)
unnamed: DD12.50 (~WAIT), R41.1 (L)
unnamed: DD7.6, DD13.1 (EB)
unnamed: DD13.4 (3B), R37.1 (L)
unnamed: DD13.9 (0A), DD14.9
unnamed: DD13.12 (3A), DD14.4
unnamed: DD13.15 (EA), DD14.3
unnamed: DD14.8, DD41.9 (C)
unnamed: DD14.11, DD24.2
unnamed: DD14.13, DD41.3 (~Q1)
unnamed: DD7.11, DD15.1
unnamed: DD7.9, DD15.2
unnamed: DD15.4, DD16.10 (SSYN), DD24.13, VD9.1 (K)
unnamed: DD15.5, DD24.11
unnamed: DD15.6, DD16.9 (KSYN)
unnamed: DD15.8, VD12.1 (K)
unnamed: DD15.9, DD15.10
unnamed: DD15.13, DD24.6
unnamed: DD16.8 (VC2), R81.1 (L)
unnamed: DD16.13 (RO), VD13.2 (A), VT3.2 (B)
unnamed: DD16.18 (VC1), DD16.27 (DAC), R67.1 (L), VT6.2 (B)
unnamed: DD16.19 (BO), VD14.2 (A), VT5.2 (B)
unnamed: DD16.20 (GO), VD15.2 (A), VT4.2 (B)
unnamed: DD18.19 (~OE), DD24.3
unnamed: DD19.1 (A15), R104.1 (L), TP8.1
unnamed: DD19.26 (A13), TP5.1
unnamed: DD19.27 (A14), TP22.1
unnamed: DD20.27 (A14), TP10.1
unnamed: DD21.2 (Q0), X9.2
unnamed: DD21.5 (Q1), X9.3
unnamed: DD21.6 (Q2), X9.4
unnamed: DD21.9 (Q3), X9.5
unnamed: DD21.12 (Q4), X9.6
unnamed: DD21.15 (Q5), X9.7
unnamed: DD21.16 (Q6), X9.8
unnamed: DD21.19 (Q7), X9.9
unnamed: DD22.6 (~Q), X9.1
unnamed: DD22.9 (Q), R59.1 (L)
unnamed: DD22.8 (~Q), DD22.12 (D)
unnamed: DD23.3 (UD), R79.1 (L), R80.2 (R), R82.2 (R)
unnamed: DD23.6 (~E), R85.1 (L), X13.6
unnamed: DD23.7 (Q), R84.2 (R)
unnamed: DD23.15 (VCC1), DD23.16 (VCC2), L1.2
unnamed: DD24.4, XJ2.2
unnamed: DD7.4, DD7.12, DD41.14 (~Q4)
unnamed: R33.2 (R), R34.2 (R), VT8.2 (B)
unnamed: R35.2 (R), VT8.1 (E), X8.1
unnamed: R59.2 (R), R60.1 (L), VT1.2 (B)
unnamed: R61.2 (R), R62.2 (R), VT2.2 (B)
unnamed: R63.2 (R), R64.1 (L), VT2.1 (E)
unnamed: R64.2 (R), X10.1
unnamed: R69.2 (R), R96.1 (L), X8.3
unnamed: R70.2 (R), R97.1 (L), X8.5
unnamed: R71.2 (R), R98.1 (L), X8.4
unnamed: R73.2 (R), R74.1 (L), R75.1 (L), VT6.1 (E)
unnamed: R80.1 (L), R81.2 (R), R81.3
unnamed: R82.1 (L), R83.2 (R), R83.3
unnamed: R87.1 (L), R98.2 (R), VT5.1 (E)
unnamed: R88.1 (L), R97.2 (R), VT4.1 (E)
unnamed: R89.1 (L), R96.2 (R), VT3.1 (E)
unnamed: R91.1 (L), VT7.1 (E)
unnamed: R94.2 (R), R95.2 (R), VT9.2 (B)
unnamed: R102.1 (L), VD13.1 (K), VD14.1 (K), VD15.1 (K), VT9.1 (E)
unnamed: VD1.2 (A), X4.1
unnamed: VD2.2 (A), X4.2
unnamed: VD3.2 (A), X4.3
unnamed: VD4.2 (A), X4.4
unnamed: VD5.2 (A), X4.5
unnamed: VD7.2 (A), X4.7
unnamed: VD8.2 (A), X4.8
unnamed: VT1.3 (C), VT2.3 (C)
R: DD12.35 (R), DD16.4 (RI)
RA0: DD12.10 (RA0), DD25.5 (A0), DD26.5 (A0), DD27.5 (A0), DD28.5 (A0), DD29.5 (A0), DD30.5 (A0), DD31.5 (A0), DD32.5 (A0), DD33.5 (A0), DD34.5 (A0), DD35.5 (A0), DD36.5 (A0), DD37.5 (A0), DD38.5 (A0), DD39.5 (A0), DD40.5 (A0)
RA1: DD12.13 (RA1), DD25.7 (A1), DD26.7 (A1), DD27.7 (A1), DD28.7 (A1), DD29.7 (A1), DD30.7 (A1), DD31.7 (A1), DD32.7 (A1), DD33.7 (A1), DD34.7 (A1), DD35.7 (A1), DD36.7 (A1), DD37.7 (A1), DD38.7 (A1), DD39.7 (A1), DD40.7 (A1)
RA2: DD12.12 (RA2), DD25.6 (A2), DD26.6 (A2), DD27.6 (A2), DD28.6 (A2), DD29.6 (A2), DD30.6 (A2), DD31.6 (A2), DD32.6 (A2), DD33.6 (A2), DD34.6 (A2), DD35.6 (A2), DD36.6 (A2), DD37.6 (A2), DD38.6 (A2), DD39.6 (A2), DD40.6 (A2)
RA3: DD12.8 (RA3), DD25.12 (A3), DD26.12 (A3), DD27.12 (A3), DD28.12 (A3), DD29.12 (A3), DD30.12 (A3), DD31.12 (A3), DD32.12 (A3), DD33.12 (A3), DD34.12 (A3), DD35.12 (A3), DD36.12 (A3), DD37.12 (A3), DD38.12 (A3), DD39.12 (A3), DD40.12 (A3)
RA4: DD12.6 (RA4), DD25.11 (A4), DD26.11 (A4), DD27.11 (A4), DD28.11 (A4), DD29.11 (A4), DD30.11 (A4), DD31.11 (A4), DD32.11 (A4), DD33.11 (A4), DD34.11 (A4), DD35.11 (A4), DD36.11 (A4), DD37.11 (A4), DD38.11 (A4), DD39.11 (A4), DD40.11 (A4)
RA5: DD12.14 (RA5), DD25.10 (A5), DD26.10 (A5), DD27.10 (A5), DD28.10 (A5), DD29.10 (A5), DD30.10 (A5), DD31.10 (A5), DD32.10 (A5), DD33.10 (A5), DD34.10 (A5), DD35.10 (A5), DD36.10 (A5), DD37.10 (A5), DD38.10 (A5), DD39.10 (A5), DD40.10 (A5)
RA6: DD12.5 (RA6), DD25.13 (A6), DD26.13 (A6), DD27.13 (A6), DD28.13 (A6), DD29.13 (A6), DD30.13 (A6), DD31.13 (A6), DD32.13 (A6), DD33.13 (A6), DD34.13 (A6), DD35.13 (A6), DD36.13 (A6), DD37.13 (A6), DD38.13 (A6), DD39.13 (A6), DD40.13 (A6)
RA7: DD12.4 (RA7), DD25.9 (A7), DD26.9 (A7), DD27.9 (A7), DD28.9 (A7), DD29.9 (A7), DD30.9 (A7), DD31.9 (A7), DD32.9 (A7), DD33.9 (A7), DD34.9 (A7), DD35.9 (A7), DD36.9 (A7), DD37.9 (A7), DD38.9 (A7), DD39.9 (A7), DD40.9 (A7)
RA10: DD7.3, DD12.19 (A10)
RA14: DD12.51 (RA14), TP7.1, X12_2.20
SO: DD12.34 (SO), R62.1 (L)
SPK: A1.1.6 (AUDIO), R63.1 (L), R92.2 (R), X13.4
TO: DD12.33 (TO), R65.1 (L)
VD0: DD12.30 (D0), DD25.2 (DI), DD25.14 (DO), DD33.2 (DI), DD33.14 (DO), R51.1 (L)
VD1: DD12.29 (D1), DD26.2 (DI), DD26.14 (DO), DD34.2 (DI), DD34.14 (DO), R52.1 (L)
VD2: DD12.28 (D2), DD27.2 (DI), DD27.14 (DO), DD35.2 (DI), DD35.14 (DO), R53.1 (L)
VD3: DD12.32 (D3), DD28.2 (DI), DD28.14 (DO), DD36.2 (DI), DD36.14 (DO), R54.1 (L)
VD4: DD12.31 (D4), DD29.2 (DI), DD29.14 (DO), DD37.2 (DI), DD37.14 (DO), R55.1 (L)
VD5: DD12.27 (D5), DD30.2 (DI), DD30.14 (DO), DD38.2 (DI), DD38.14 (DO), R56.1 (L)
VD6: DD12.26 (D6), DD31.2 (DI), DD31.14 (DO), DD39.2 (DI), DD39.14 (DO), R57.1 (L)
VD7: DD12.25 (D7), DD32.2 (DI), DD32.14 (DO), DD40.2 (DI), DD40.14 (DO), R58.1 (L)
Y: DD12.38 (Y), DD16.22 (YI)
~BUSAK: DD17.23 (~BUSY), X12_1.26
~BUSRQ: DD17.25 (~BREQ), R42.1 (L), X12_1.19
~CAS0: DD12.58 (~CAS0), DD33.15 (~CS), DD34.15 (~CS), DD35.15 (~CS), DD36.15 (~CS), DD37.15 (~CS), DD38.15 (~CS), DD39.15 (~CS), DD40.15 (~CS), XJ2.3
~CAS1*: DD15.12, DD25.15 (~CS), DD26.15 (~CS), DD27.15 (~CS), DD28.15 (~CS), DD29.15 (~CS), DD30.15 (~CS), DD31.15 (~CS), DD32.15 (~CS)
~CAS1: DD12.57 (~CAS1), DD24.5
~CLK: DD6.12, X12_1.8
~HLT: DD17.18 (~HALT), X12_2.15
~INT: DD17.16 (~INT), R40.2 (R), X12_2.13
~IORQGE: DD12.47 (~IORQ), R37.2 (R), X12_1.13
~IORQ: DD3.13, DD13.2 (IB), DD13.14 (IA), DD17.20 (~IORQ), X12_2.17
~M1: DD4.13, DD5.3 (C), DD6.1, DD12.48 (~M1), DD17.27 (~M1), X12_2.24
~MREQ: DD3.5, DD12.53 (~MREQ), DD17.19 (~MREQ), X12_2.16
~NMI: DD17.17 (~NMI), R7.2 (R), X12_2.14
~RAM0: DD3.6, DD3.9, DD7.13, DD14.12
~RAMCS: DD24.1, R36.2 (R), X12_2.4
~RAS: DD12.59 (~RAS), DD25.4 (~RS), DD26.4 (~RS), DD27.4 (~RS), DD28.4 (~RS), DD29.4 (~RS), DD30.4 (~RS), DD31.4 (~RS), DD32.4 (~RS), DD33.4 (~RS), DD34.4 (~RS), DD35.4 (~RS), DD36.4 (~RS), DD37.4 (~RS), DD38.4 (~RS), DD39.4 (~RS), DD40.4 (~RS)
~RCPU: DD6.9, DD6.10, DD17.26 (~RES)
~RDKD: DD9.1 (~OE), DD14.6
~RDKEY: DD10.1 (~OE), DD12.44 (~RDKEY)
~RDP0: DD8.1 (~OE), DD12.40 (~RDP0)
~RD: DD3.10, DD4.12, DD12.52 (~RD), DD14.5, DD17.21 (~RD), X12_2.18
~RES: DD4.4, DD5.4 (~S), DD5.10 (~S), DD6.6, DD12.16 (~RES), DD22.13 (~R), X4.12, X5.1, X12_1.20
~RFSH: DD12.49 (~RFSH), DD17.28 (~RFSH), X12_2.25
~RM: DD1.12, DD41.1 (R)
~ROMCS: DD19.20 (~CE), DD20.20 (~CE), R3.2 (R), X12_1.25
~SP: DD41.7 (Q2), TP13.1
~SR: DD41.10 (Q3), TP20.1
~SYN: DD12.39 (~S), DD15.3, R33.1 (L), VD11.1 (K)
~TRD: DD20.1 (A15), R68.1 (L), TP15.1, X12_2.23
~WAIT: DD17.24 (~WAIT), R41.2 (R), VD12.2 (A), X12_2.21
~WERAM: DD7.8, DD25.3 (~WR), DD26.3 (~WR), DD27.3 (~WR), DD28.3 (~WR), DD29.3 (~WR), DD30.3 (~WR), DD31.3 (~WR), DD32.3 (~WR), DD33.3 (~WR), DD34.3 (~WR), DD35.3 (~WR), DD36.3 (~WR), DD37.3 (~WR), DD38.3 (~WR), DD39.3 (~WR), DD40.3 (~WR)
~WE: DD7.10, DD12.60 (~WE)
~WRP0: DD12.41 (~WRP0), DD22.4 (~S)
~WRP3: DD1.11, DD12.43 (~WRP3), DD22.1 (~R)
~WR: DD12.46 (~WR), DD14.10, DD17.22 (~WR), X12_2.19

Notes on the sheet:
UncleRus
16/8 МГц
