UncleRus/quorum-reborn/kicad/Quorum-BK04/Quorum-BK04-mods.sch

## KiCad design kicad/Quorum-BK04/Quorum-BK04-mods.sch (2020-11-30)

Schematic: Quorum-BK04-mods.sch

Parts:
*C36: 22-56; C_Rect_L7.0mm_W2.5mm_P5.00mm
*DD101: КР1533ИР22; DIP-20_W7.62mm_Socket_LongPads
*DD102: КР1533ЛЛ1; DIP-14_W7.62mm_Socket_LongPads
*DD103: КР1533ЛИ1; DIP-14_W7.62mm_Socket_LongPads
*DD104: КР1533ЛЕ1; DIP-14_W7.62mm_Socket_LongPads
*R107: 22k; R_Axial_DIN0204_L3.6mm_D1.6mm_P7.62mm_Horizontal
*R109: 1k; R_Axial_DIN0204_L3.6mm_D1.6mm_P7.62mm_Horizontal
A1: RF MODULATOR
C1, C10: 1,0; CP_Radial_D7.5mm_P2.50mm
C2, C3, C8, C11: 0,01; C_Rect_L7.0mm_W2.5mm_P5.00mm
C4, C5, C35, C38: 0,1; C_Rect_L7.0mm_W2.5mm_P5.00mm
C6: 4700; C_Rect_L7.0mm_W2.5mm_P5.00mm
C7: 5,0; CP_Radial_D7.5mm_P2.50mm
C37, C40, C41: 100; C_Rect_L7.0mm_W2.5mm_P5.00mm
C39: 56; C_Rect_L7.0mm_W2.5mm_P5.00mm
DD1, DD2, DD3, DD35: КР1533ИР22; DIP-20_W7.62mm_Socket_LongPads
DD4, DD51: 1006ВИ1; DIP-8_W7.62mm_Socket_LongPads
DD5, DD15, DD34: КР1533ЛН1; DIP-14_W7.62mm_Socket_LongPads
DD6, DD7, DD8, DD9, DD10: КР1533ИЕ5; DIP-14_W7.62mm_Socket_LongPads
DD11, DD12, DD18: КР1533ТМ2; DIP-14_W7.62mm_Socket_LongPads
DD13, DD19, DD45, DD52: КР1533ЛИ1; DIP-14_W7.62mm_Socket_LongPads
DD14, DD17, DD40: КР1533ЛЕ1; DIP-14_W7.62mm_Socket_LongPads
DD16, DD39, DD50, DD58: КР1533ЛА3; DIP-14_W7.62mm_Socket_LongPads
DD20, DD21, DD22, DD23, DD24, DD44: КР1533КП11; DIP-16_W7.62mm_Socket_LongPads
DD25, DD26, DD27, DD28, DD29, DD30, DD31, DD32: К565РУ5; DIP-16_W7.62mm_Socket_LongPads
DD33: Z80; DIP-40_W15.24mm_Socket_LongPads
DD36, DD37: AT28C256; DIP-28_W15.24mm_Socket_LongPads
DD38: КР1533ИД4; DIP-16_W7.62mm_Socket_LongPads
DD41, DD43, DD49, DD53, DD54, DD59, DD60: КР1533ИР23; DIP-20_W7.62mm_Socket_LongPads
DD42: КР1533ИР24; DIP-20_W7.62mm_Socket_LongPads
DD46, DD48: КР1533ЛП5; DIP-14_W7.62mm_Socket_LongPads
DD47: КР1533ТМ8; DIP-16_W7.62mm_Socket_LongPads
DD55, DD56: КР1533ИД10; DIP-16_W7.62mm_Socket_LongPads
DD57: КР531ГГ1; DIP-16_W7.62mm_Socket_LongPads
FU1: FUSE
HL1: АЛ307
KT1, KT2, KT3, KT4, KT5, KT6, KT7, KT8, KT9: TestPoint; TestPoint_THTPad_D1.5mm_Drill0.7mm
L1: DM-0,1-100
R1, R2, R3, R4, R5, R84, R85, R89, R100: 510; R_Axial_DIN0204_L3.6mm_D1.6mm_P7.62mm_Horizontal
R6, R48, R95: 3k6; R_Axial_DIN0204_L3.6mm_D1.6mm_P7.62mm_Horizontal
R7, R8, R9, R10, R11, R12, R13, R14, R15, R16, R17, R18, R19, R20, R21, R22, R23, R24, R25, R31, R32, R47: 10k; R_Axial_DIN0204_L3.6mm_D1.6mm_P7.62mm_Horizontal
R26, R103: 47k; R_Axial_DIN0204_L3.6mm_D1.6mm_P7.62mm_Horizontal
R27, R102: 680; R_Axial_DIN0204_L3.6mm_D1.6mm_P7.62mm_Horizontal
R28, R29: 22k; R_Axial_DIN0204_L3.6mm_D1.6mm_P7.62mm_Horizontal
R33, R34, R35, R78, R80, R82: 360; R_Axial_DIN0204_L3.6mm_D1.6mm_P7.62mm_Horizontal
R36, R37, R38, R41, R42, R43, R44, R46, R49, R56, R58, R61, R64, R68, R70, R77, R94, R98, R101, R105, R114: 1k; R_Axial_DIN0204_L3.6mm_D1.6mm_P7.62mm_Horizontal
R39, R45, R57, R59, R60, R62, R63, R65, R83, R104, R106, R111, R112: 5k1; R_Axial_DIN0204_L3.6mm_D1.6mm_P7.62mm_Horizontal
R40: 1k(2k); R_Axial_DIN0204_L3.6mm_D1.6mm_P7.62mm_Horizontal
R50, R51, R52, R53, R87: 1k5; R_Axial_DIN0204_L3.6mm_D1.6mm_P7.62mm_Horizontal
R54: 100k; R_Axial_DIN0204_L3.6mm_D1.6mm_P7.62mm_Horizontal
R55: 390k; R_Axial_DIN0204_L3.6mm_D1.6mm_P7.62mm_Horizontal
R66: 4k3; R_Axial_DIN0204_L3.6mm_D1.6mm_P7.62mm_Horizontal
R67, R76: 2k; R_Axial_DIN0204_L3.6mm_D1.6mm_P7.62mm_Horizontal
R69: 150; R_Axial_DIN0204_L3.6mm_D1.6mm_P7.62mm_Horizontal
R71: 820; R_Axial_DIN0204_L3.6mm_D1.6mm_P7.62mm_Horizontal
R72, R73, R74, R75: 100
R79: 33; R_Axial_DIN0204_L3.6mm_D1.6mm_P7.62mm_Horizontal
R81, R99: 100; R_Axial_DIN0204_L3.6mm_D1.6mm_P7.62mm_Horizontal
R88: 1k8; R_Axial_DIN0204_L3.6mm_D1.6mm_P7.62mm_Horizontal
R90: 620; R_Axial_DIN0204_L3.6mm_D1.6mm_P7.62mm_Horizontal
R91: 4k7; R_Axial_DIN0204_L3.6mm_D1.6mm_P7.62mm_Horizontal
R92: 6k2; R_Axial_DIN0204_L3.6mm_D1.6mm_P7.62mm_Horizontal
R93: 1k2; R_Axial_DIN0204_L3.6mm_D1.6mm_P7.62mm_Horizontal
R96: 750; R_Axial_DIN0204_L3.6mm_D1.6mm_P7.62mm_Horizontal
R97: 2k2; R_Axial_DIN0204_L3.6mm_D1.6mm_P7.62mm_Horizontal
R108: 22k
R110: 4k7
S1: TURBO
VD1, VD2, VD3, VD4, VD5, VD6, VD7, VD8: D; D_DO-35_SOD27_P7.62mm_Horizontal
VD9, VD10, VD12, VD13, VD14: КД522; D_DO-35_SOD27_P7.62mm_Horizontal
VD11: КС139; D_DO-35_SOD27_P7.62mm_Horizontal
VT1, VT2, VT3, VT4, VT6, VT7: KT315; TO-92_Inline_Wide
VT5: KT361; TO-92_Inline_Wide
X1: SINCLAIR; DIN5-RA-PTH
X2: KEMPSTON; DIN5-RA-PTH
X3: KEYBOARD 1; PinHeader_1x12_P2.54mm_Vertical
X4: KEYBOARD 2; PinHeader_1x12_P2.54mm_Vertical
X5: TAPE IN; DIN5-RA-PTH
X6.1: EXPANSION B
X6.2: EXPANSION A
X8: SPEAKER; PinHeader_1x02_P2.54mm_Vertical
X9: VIDEO; DIN5-RA-PTH
X10: RGB; DIN5-RA-PTH
X11: TAPE OUT; DIN5-RA-PTH
X12: CENTRONICS
ZQ1: 14MHz; Crystal_HC49-U_Horizontal_1EP_style2

Notes on the sheet:
UncleRus
*Pentagon
